ApotheoTech/Aper-Oculus/APT-KRIA-FMC.kicad_sch

## KiCad design APT-KRIA-FMC.kicad_sch (2023-12-22)

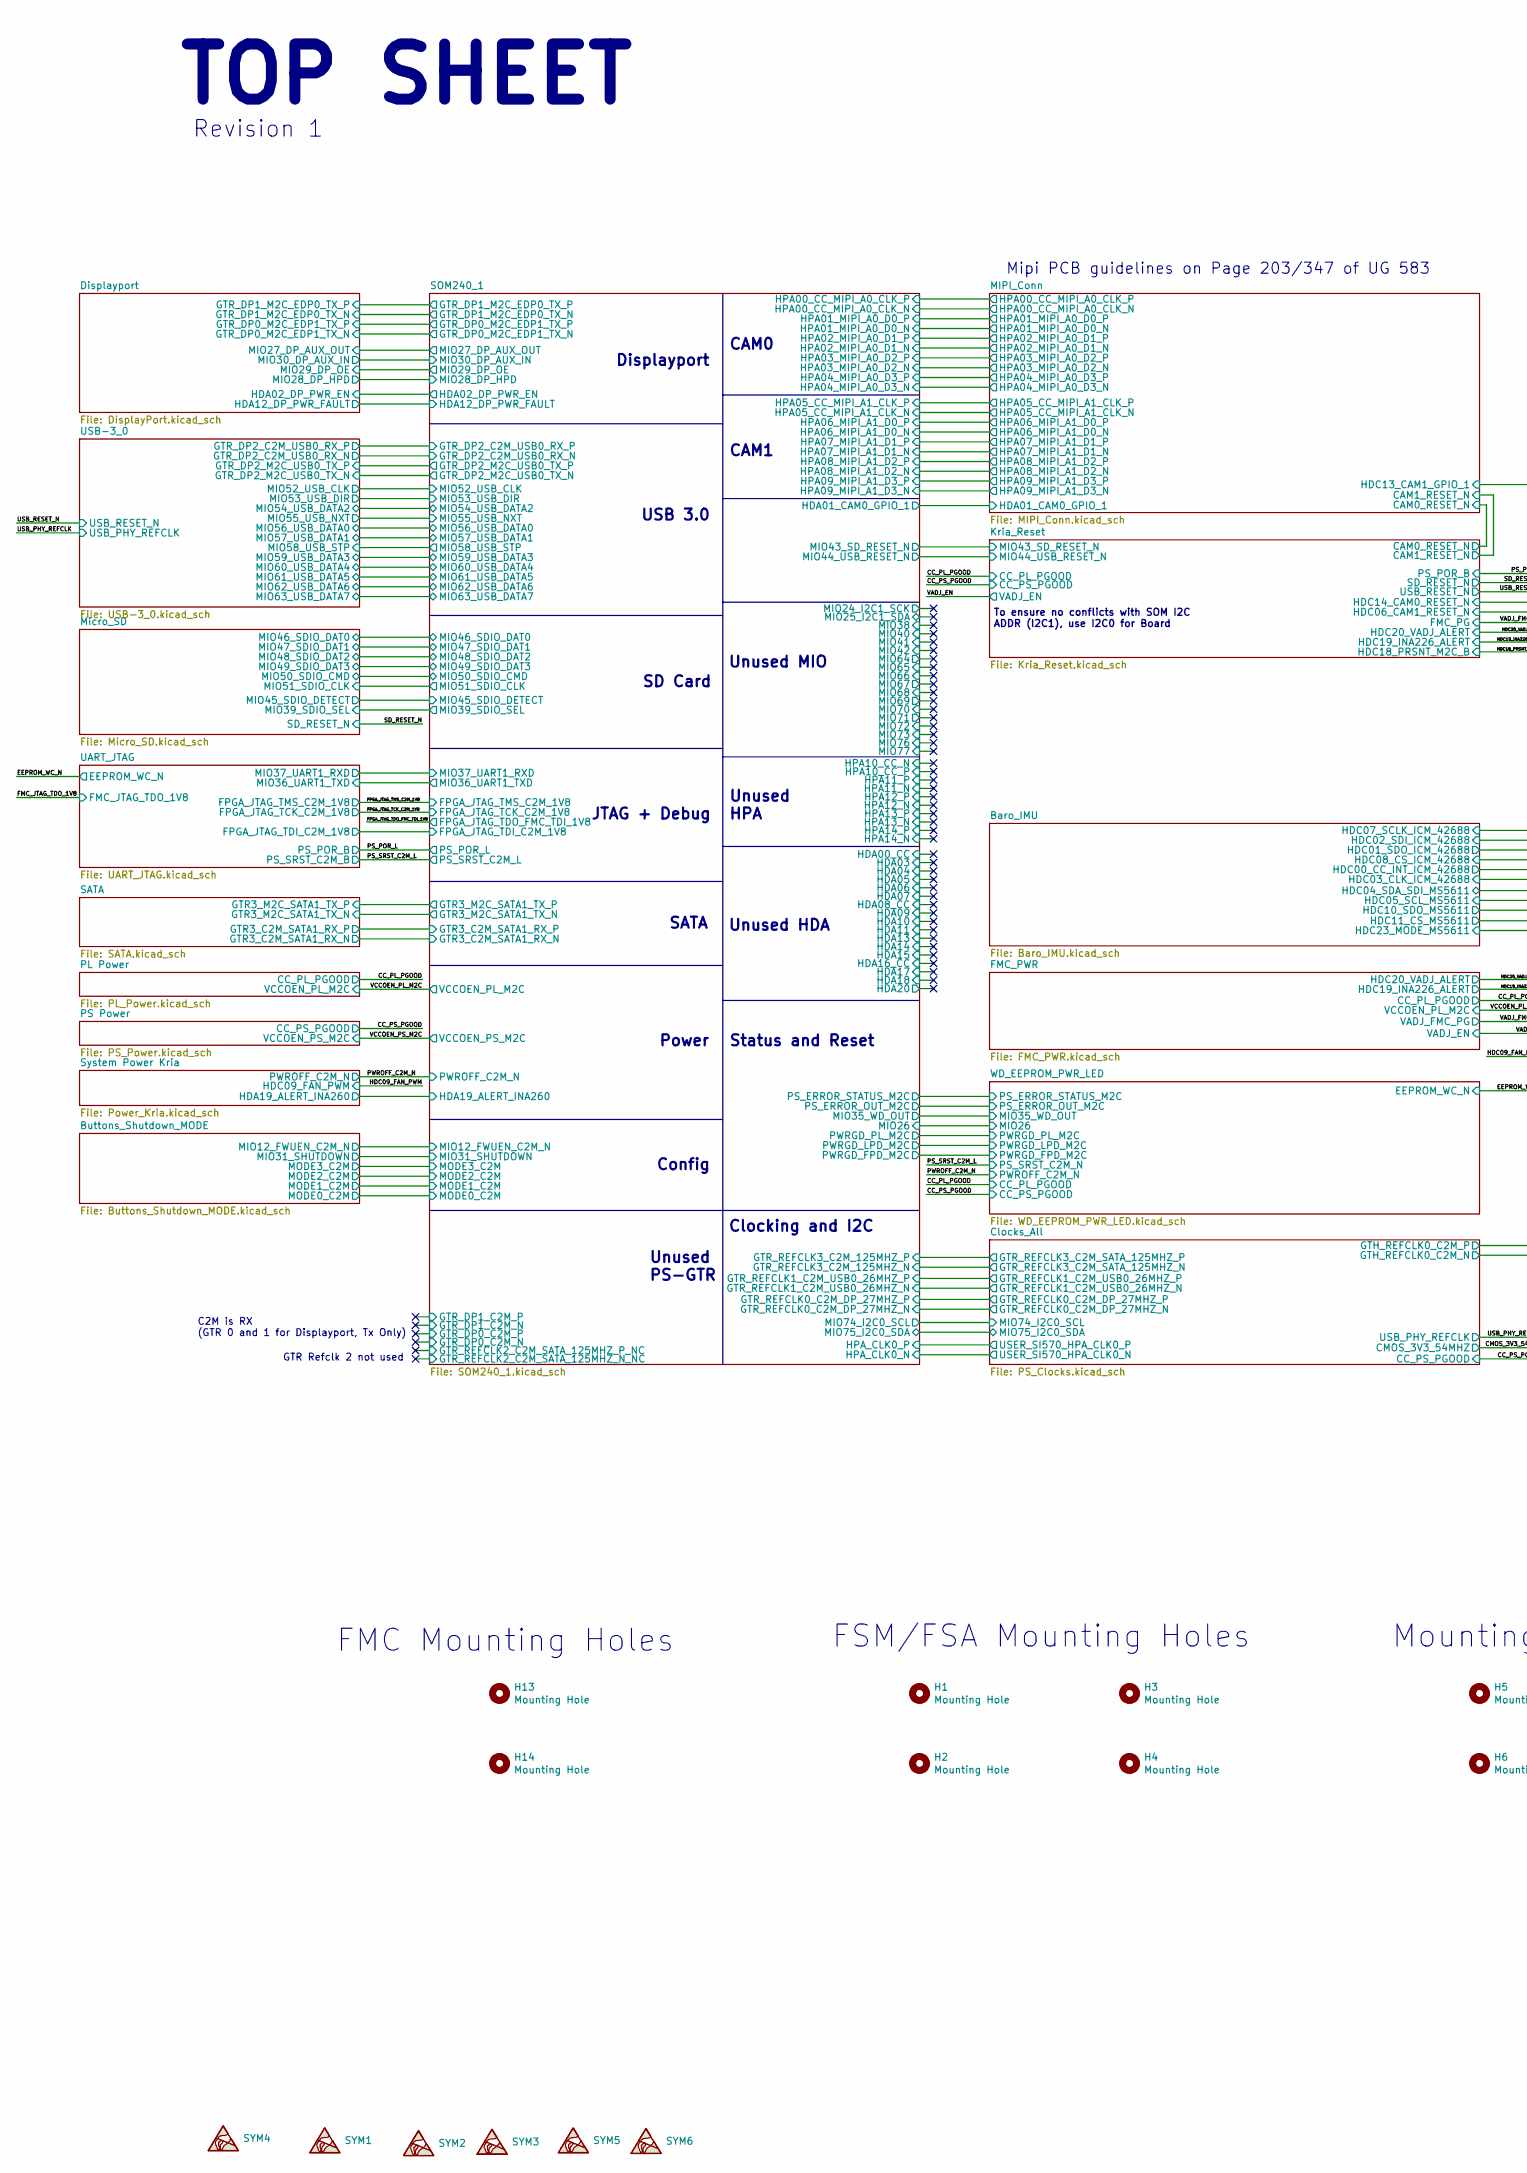
[picture p6: schematic APT-KRIA-FMC.kicad_sch, part in row 1, column 1]

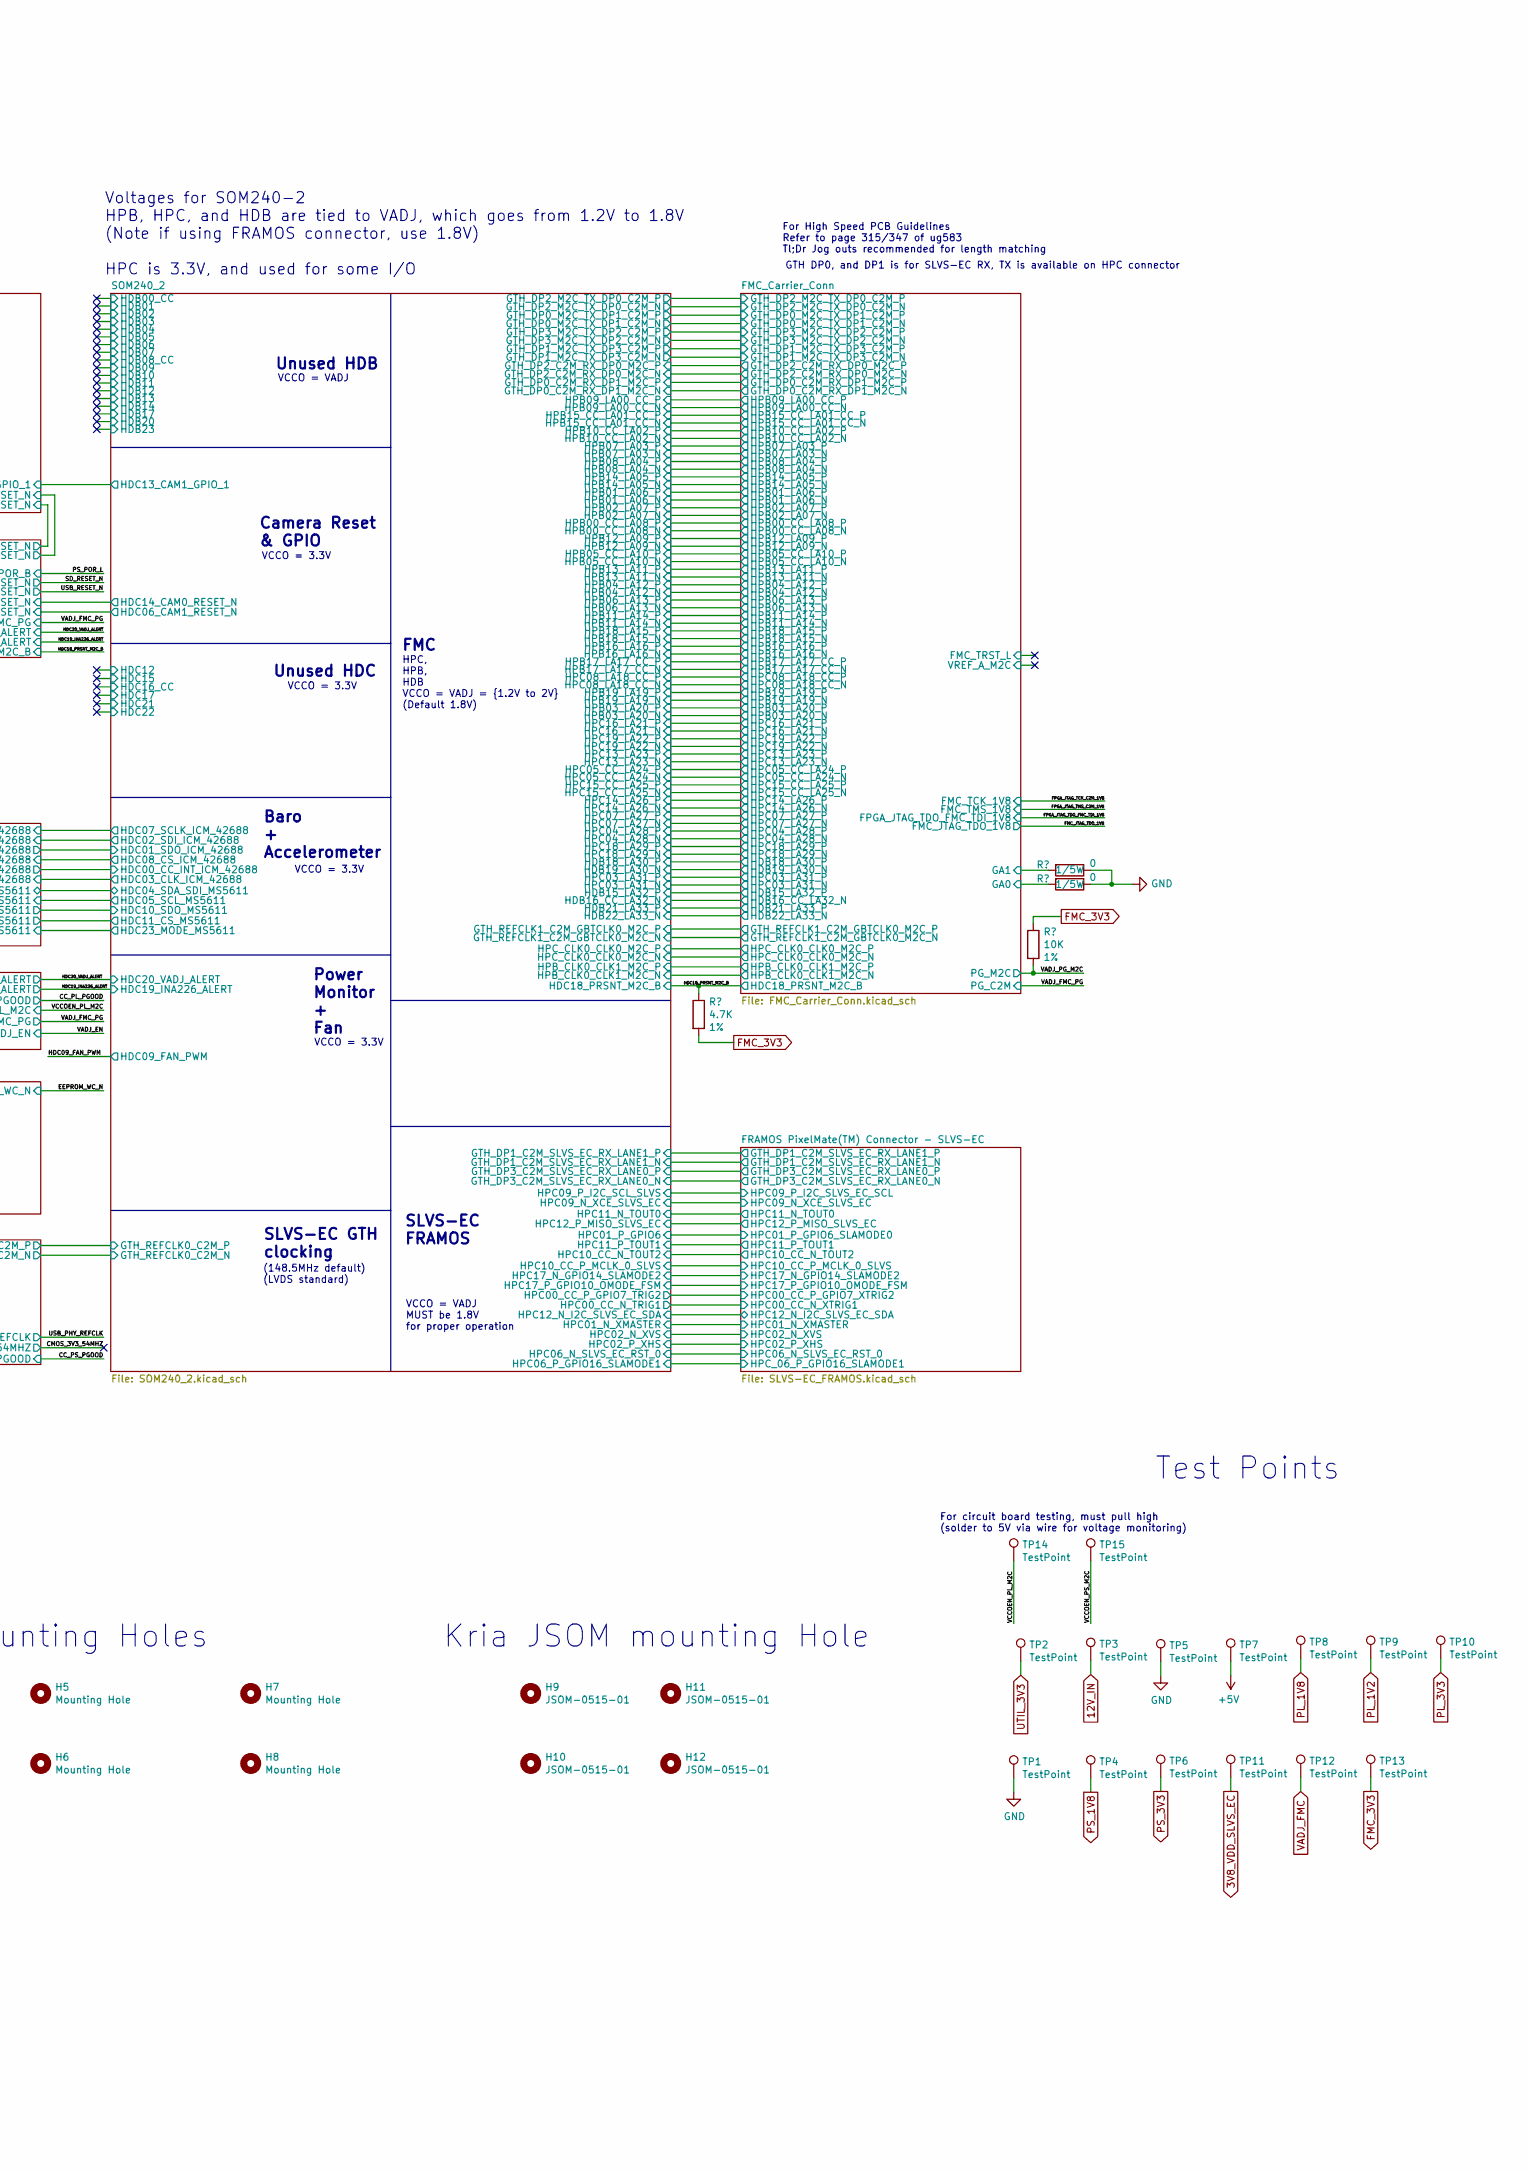
[picture p7: schematic APT-KRIA-FMC.kicad_sch, part in row 1, column 2]

Parts:
H1, H2, H3, H4: Mounting Hole; M1_6_FRAMOS
H5, H6, H7, H8: Mounting Hole; 3.4mm_Mounting_Hole
H9, H10, H11, H12: JSOM-0515-01
H13, H14: Mounting Hole; MountingHole_2.7mm_M2.5_Pad_2.9mm
R5, R6: 0; R_0402_1005Metric; PartNumber CRCW04020000Z0EDHP
R11: 4.7K; R_0402_1005Metric; Tolerance 1%; PartNumber CRCW04024K70FKED
R33: 10K; R_0402_1005Metric; Tolerance 1%; PartNumber ERJ-2RKF1002X
SYM1: SYM_ESD_Small; ApotheoTech_Sym
SYM2: SYM_ESD_Small; WEEE-Logo_4.2x6mm_SilkScreen
SYM3: SYM_ESD_Small; ESD-Logo_6.6x6mm_SilkScreen
SYM4: SYM_ESD_Small; ApotheoTech_Logo_Small
SYM5: SYM_ESD_Small; CE-Logo_8.5x6mm_SilkScreen
SYM6: SYM_ESD_Small; UKCA_Logo_8_5mm
TP1, TP2, TP3, TP4, TP5, TP6, TP7, TP8, TP9, TP10, TP11, TP12, TP13, TP14, TP15: TestPoint

Connections:
3V8_VDD_SLVS_EC: TP11.1
12V_IN: TP3.1
+5V: TP7.1
FMC_3V3: R11.2, R33.1, TP13.1
GA0: R6.2
GA1: R5.2
GND: R5.1, R6.1, TP1.1, TP5.1
HDC18_PRSNT_M2C_B: R11.1
PL_1V2: TP9.1
PL_1V8: TP8.1
PL_3V3: TP10.1
PS_1V8: TP4.1
PS_3V3: TP6.1
UTIL_3V3: TP2.1
VADJ_FMC: TP12.1
VADJ_PG_M2C: R33.2
VCCOEN_PL_M2C: TP14.1
VCCOEN_PS_M2C: TP15.1

Notes on the sheet:
VCCO = VADJ
SLVS-EC FRAMOS
VCCO = 3.3V
For High Speed PCB Guidelines Refer to page 315/347 of ug583 Tl;Dr Jog outs recommended for length matching
SD Card
Power
(148.5MHz default) (LVDS standard)
Unused HDA
Baro + Accelerometer
To ensure no conflicts with SOM I2C ADDR (I2C1), use I2C0 for Board
Mipi PCB guidelines on Page 203/347 of UG 583
Unused HDB
Clocking and I2C
FMC Mounting Holes
Config
USB 3.0
FMC
CAM0
Unused PS-GTR
Displayport
Kria JSOM mounting Hole
Test Points
VCCO = VADJ MUST be 1.8V for proper operation
SATA
Revision 1
Voltages for SOM240-2 HPB, HPC, and HDB are tied to VADJ, which goes from 1.2V to 1.8V (Note if using FRAMOS connector, use 1.8V) HPC is 3.3V, and used for some I/O
TOP SHEET
JTAG + Debug
FSM/FSA Mounting Holes
C2M is RX (GTR 0 and 1 for Displayport, Tx Only)
HPC, HPB, HDB VCCO = VADJ = {1.2V to 2V} (Default 1.8V)
GTR Refclk 2 not used
Unused HPA
Status and Reset
CAM1
For circuit board testing, must pull high (solder to 5V via wire for voltage monitoring)
SLVS-EC GTH clocking
Camera Reset & GPIO
Power Monitor + Fan
GTH DP0, and DP1 is for SLVS-EC RX, TX is available on HPC connector
Mounting Holes
Unused MIO
Unused HDC
