ApotheoTech/Aper-Oculus/Baro_IMU.kicad_sch

## KiCad design Baro_IMU.kicad_sch (2023-12-22)

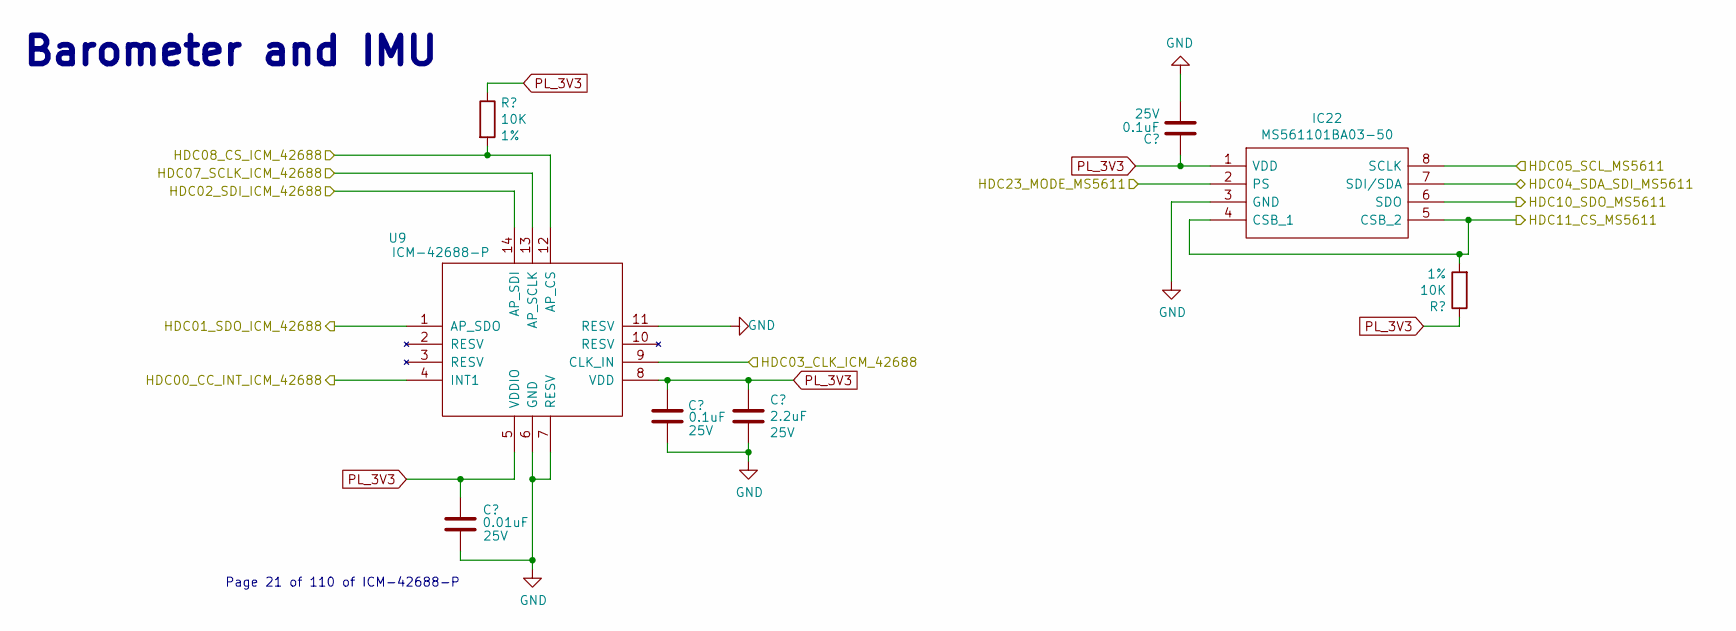
[picture p8: schematic Baro_IMU.kicad_sch]

Parts:
C179: 0.01uF; C_0402_1005Metric; Tolerance +-10%; Voltage 25V; PartNumber 04023D103KAT2A
C180, C264: 0.1uF; C_0402_1005Metric; Tolerance +-10%; Voltage 25V; PartNumber TMK105BJ104KVHF
C263: 2.2uF; C_0402_1005Metric; Tolerance +-10%; Voltage 25V; PartNumber GRM155R61E225KE1D
IC22: MS561101BA03-50; Mouser Part Number 824-MS561101BA03-50
R44, R51: 10K; R_0402_1005Metric; Tolerance 1%; PartNumber ERJ-2RKF1002X
U9: ICM-42688-P

Connections:
GND: C179.1, C180.1, C263.2, C264.1, IC22.3 (GND), U9.6 (GND), U9.7 (RESV), U9.11 (RESV)
HDC00_CC_INT_ICM_42688: U9.4 (INT1)
HDC01_SDO_ICM_42688: U9.1 (AP_SDO)
HDC02_SDI_ICM_42688: U9.14 (AP_SDI)
HDC03_CLK_ICM_42688: U9.9 (CLK_IN)
HDC04_SDA_SDI_MS5611: IC22.7 (SDI/SDA)
HDC05_SCL_MS5611: IC22.8 (SCLK)
HDC07_SCLK_ICM_42688: U9.13 (AP_SCLK)
HDC08_CS_ICM_42688: R44.2, U9.12 (AP_CS)
HDC10_SDO_MS5611: IC22.6 (SDO)
HDC11_CS_MS5611: IC22.4 (CSB_1), IC22.5 (CSB_2), R51.2
HDC23_MODE_MS5611: IC22.2 (PS)
PL_3V3: C179.2, C180.2, C263.1, C264.2, IC22.1 (VDD), R44.1, R51.1, U9.5 (VDDIO), U9.8 (VDD)

Notes on the sheet:
Barometer and IMU
Page 21 of 110 of ICM-42688-P
