ApotheoTech/Aper-Oculus/Buttons_Shutdown_MODE.kicad_sch

## KiCad design Buttons_Shutdown_MODE.kicad_sch (2023-12-22)

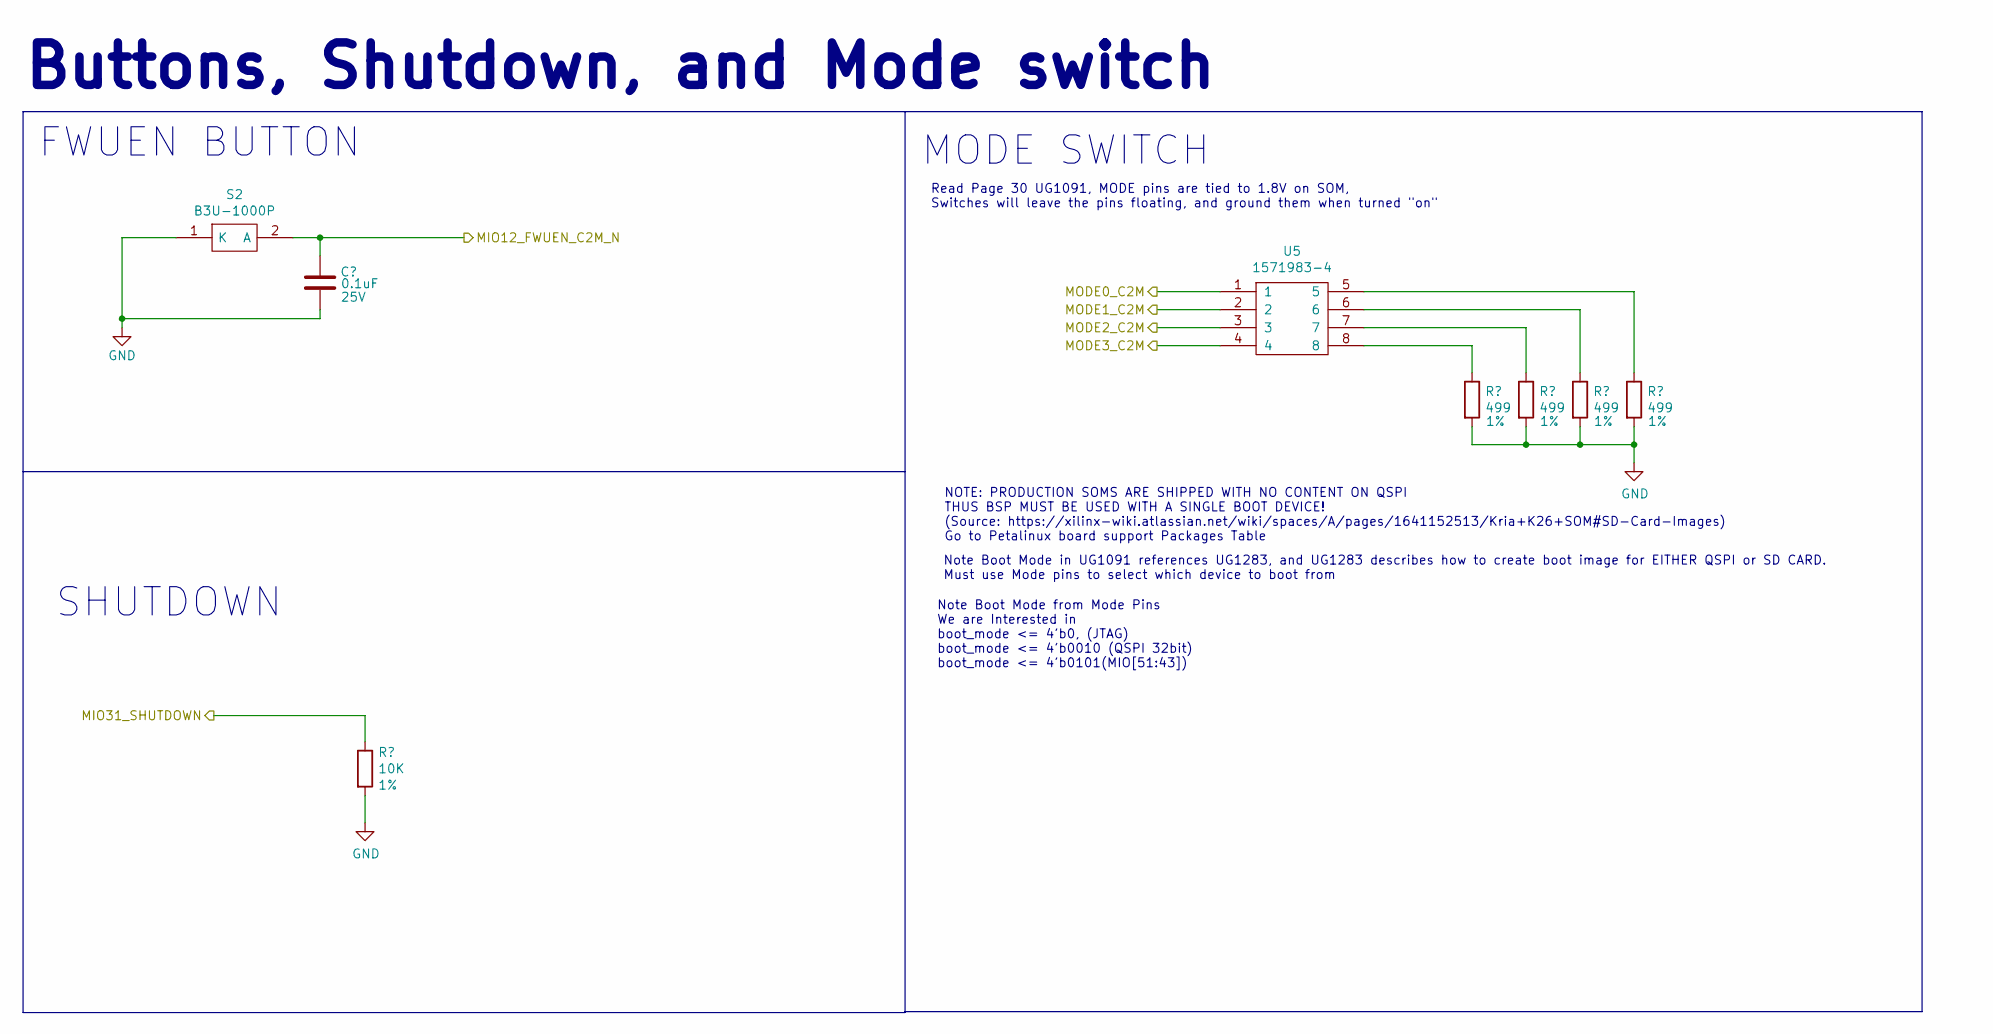
[picture p9: schematic Buttons_Shutdown_MODE.kicad_sch]

Parts:
C258: 0.1uF; C_0402_1005Metric; Tolerance +-10%; Voltage 25V; PartNumber TMK105BJ104KVHF
R218: 10K; R_0402_1005Metric; Tolerance 1%; PartNumber ERJ-2RKF1002X
R219, R220, R221, R222: 499; R_0402_1005Metric; PartNumber ERJ-2RKF4990X
S2: B3U-1000P; Mouser Part Number 653-B3U-1000P
U5: 1571983-4

Connections:
GND: C258.1, R218.2, R219.2, R220.2, R221.2, R222.2, S2.1 (K)
MIO12_FWUEN_C2M_N: C258.2, S2.2 (A)
MIO31_SHUTDOWN: R218.1
MODE0_C2M: U5.1
MODE1_C2M: U5.2
MODE2_C2M: U5.3
MODE3_C2M: U5.4
unnamed: R219.1, U5.8
unnamed: R220.1, U5.7
unnamed: R221.1, U5.6
unnamed: R222.1, U5.5

Notes on the sheet:
NOTE: PRODUCTION SOMS ARE SHIPPED WITH NO CONTENT ON QSPI THUS BSP MUST BE USED WITH A SINGLE BOOT DEVICE! (Source: https://xilinx-wiki.atlassian.net/wiki/spaces/A/pages/1641152513/Kria+K26+SOM#SD-Card-Images) Go to Petalinux board support Packages Table
SHUTDOWN
Read Page 30 UG1091, MODE pins are tied to 1.8V on SOM, Switches will leave the pins floating, and ground them when turned "on"
Buttons, Shutdown, and Mode switch
Note Boot Mode from Mode Pins We are Interested in boot_mode <= 4'b0, (JTAG) boot_mode <= 4'b0010 (QSPI 32bit) boot_mode <= 4'b0101(MIO[51:43])
MODE SWITCH
Note Boot Mode in UG1091 references UG1283, and UG1283 describes how to create boot image for EITHER QSPI or SD CARD. Must use Mode pins to select which device to boot from
FWUEN BUTTON
