ApotheoTech/Aper-Oculus/DisplayPort.kicad_sch

## KiCad design DisplayPort.kicad_sch (2023-12-22)

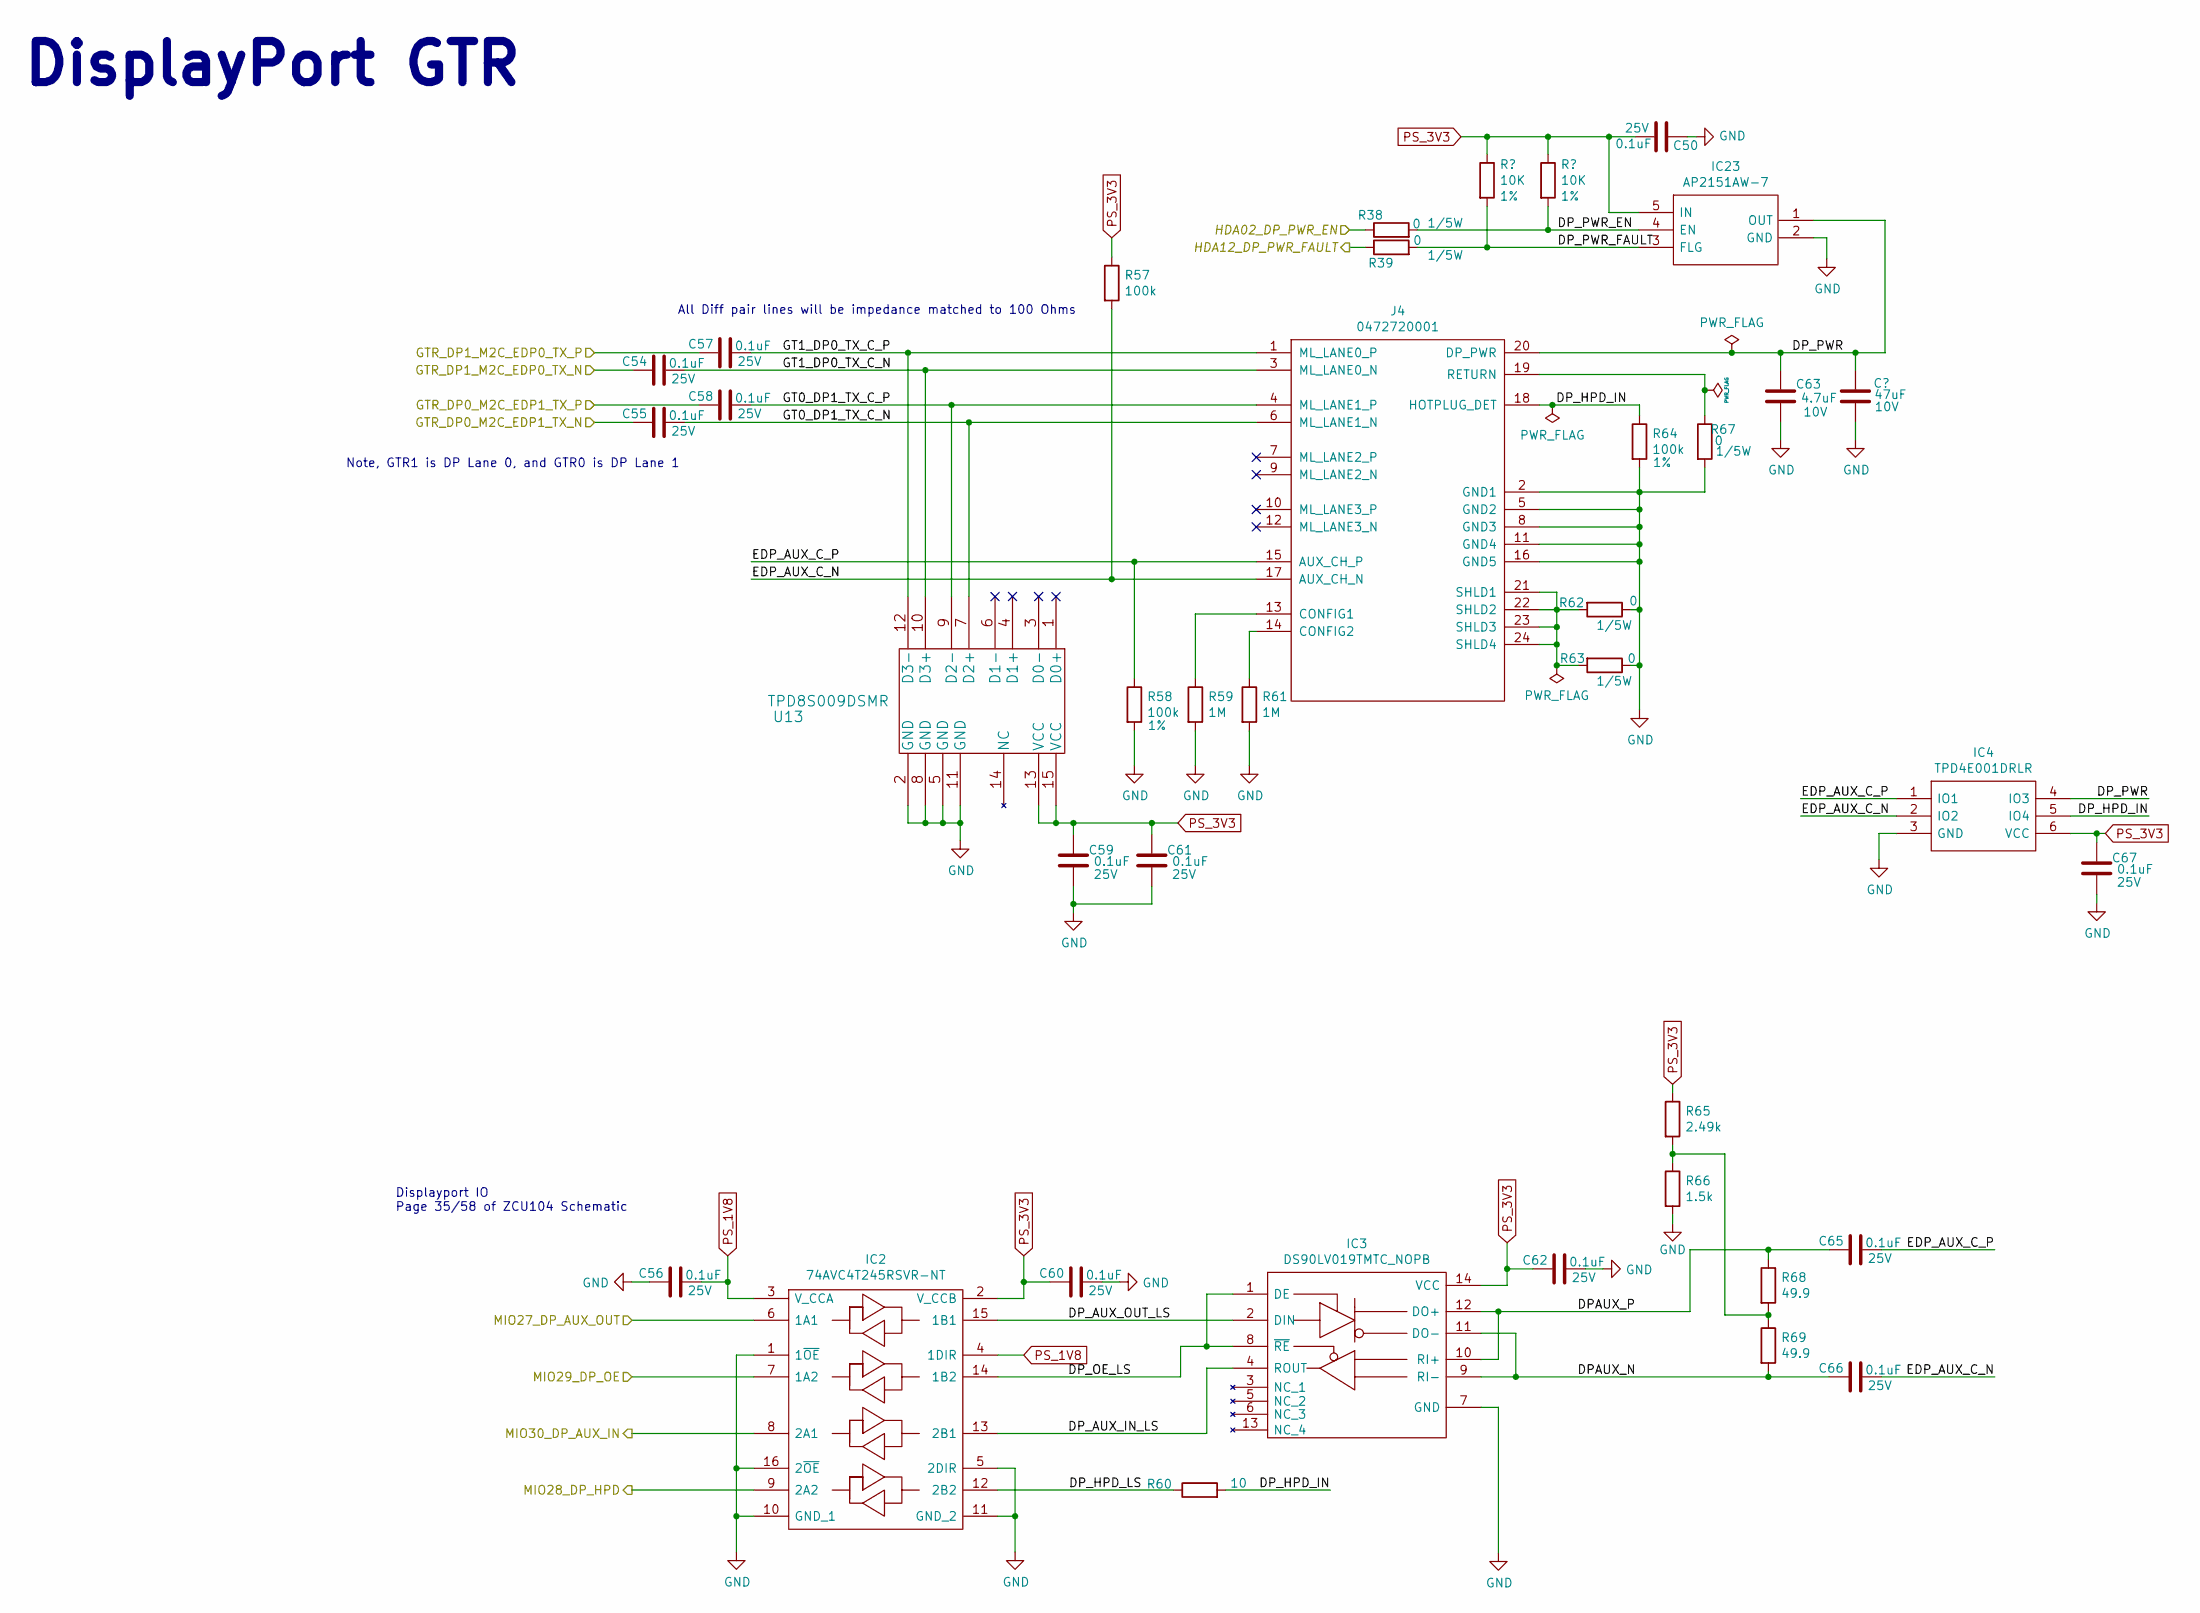
[picture p10: schematic DisplayPort.kicad_sch]

Parts:
C50, C54, C55, C56, C57, C58, C59, C60, C61, C62, C67: 0.1uF; C_0402_1005Metric; Tolerance +-10%; Voltage 25V; PartNumber TMK105BJ104KVHF
C51: 47uF; C_0805_2012Metric; Tolerance +-20%; Voltage 10V; PartNumber GRM21BR61A476ME15L
C63: 4.7uF; C_0402_1005Metric; Tolerance +-10%; Voltage 10V; PartNumber CL05A475KP5NRNC
C65, C66: 0.1uF; C_0402_1005Metric_smaller_footprint; Tolerance +-10%; Voltage 25V; PartNumber TMK105BJ104KVHF
IC2: 74AVC4T245RSVR-NT; Mouser Part Number 595-74AVC4T245RSVRNT
IC3: DS90LV019TMTC_NOPB; Mouser Part Number 926-S90LV019TMTCNOPB
IC4: TPD4E001DRLR; Mouser Part Number 595-TPD4E001DRLR
IC23: AP2151AW-7; Mouser Part Number 621-AP2151AW-7
J4: 0472720001‎
R38, R39, R62, R63, R67: 0; R_0402_1005Metric; PartNumber CRCW04020000Z0EDHP
R40, R41: 10K; R_0402_1005Metric; Tolerance 1%; PartNumber ERJ-2RKF1002X
R57, R58, R64: 100k; R_0402_1005Metric; PartNumber CRCW0402100KFKEDHP
R59, R61: 1M; R_0402_1005Metric; PartNumber CRCW04021M00FKED
R60: 10; R_0402_1005Metric; PartNumber ERJ-2RKF10R0X
R65: 2.49k; R_0402_1005Metric; PartNumber ERJ-2RKF2491X
R66: 1.5k; R_0402_1005Metric; PartNumber ERJ-H2RF1501X
R68, R69: 49.9; R_0402_1005Metric; PartNumber ERJ-2RKF49R9X
U13: TPD8S009DSMR

Connections:
DPAUX_N: C66.1, IC3.9 (RI-), IC3.11 (DO-), R69.2
DPAUX_P: C65.1, IC3.10 (RI+), IC3.12 (DO+), R68.1
DP_AUX_IN_LS: IC2.13 (2B1), IC3.4 (ROUT)
DP_AUX_OUT_LS: IC2.15 (1B1), IC3.2 (DIN)
DP_HPD_IN: IC4.5 (IO4), J4.18 (HOTPLUG_DET), R60.2, R64.1
DP_HPD_LS: IC2.12 (2B2), R60.1
DP_OE_LS: IC2.14 (1B2), IC3.1 (DE), IC3.8 (~RE)
DP_PWR: C51.2, C63.1, IC4.4 (IO3), IC23.1 (OUT), J4.20 (DP_PWR)
DP_PWR_EN: IC23.4 (EN), R38.2, R41.2
DP_PWR_FAULT: IC23.3 (FLG), R39.2, R40.2
EDP_AUX_C_N: C66.2, IC4.2 (IO2), J4.17 (AUX_CH_N), R57.2
EDP_AUX_C_P: C65.2, IC4.1 (IO1), J4.15 (AUX_CH_P), R58.1
GND: C50.1, C51.1, C56.1, C59.1, C60.2, C61.1, C62.2, C63.2, C67.1, IC2.1 (1~OE), IC2.5 (2DIR), IC2.10 (GND_1), IC2.11 (GND_2), IC2.16 (2~OE), IC3.7 (GND), IC4.3 (GND), IC23.2 (GND), J4.2 (GND1), J4.5 (GND2), J4.8 (GND3), J4.11 (GND4), J4.16 (GND5), R58.2, R59.2, R61.2, R62.1, R63.1, R64.2, R66.2, R67.2, U13.2 (GND), U13.5 (GND), U13.8 (GND), U13.11 (GND)
GT0_DP1_TX_C_N: C55.2, J4.6 (ML_LANE1_N), U13.7 (D2+)
GT0_DP1_TX_C_P: C58.2, J4.4 (ML_LANE1_P), U13.9 (D2-)
GT1_DP0_TX_C_N: C54.2, J4.3 (ML_LANE0_N), U13.10 (D3+)
GT1_DP0_TX_C_P: C57.2, J4.1 (ML_LANE0_P), U13.12 (D3-)
GTR_DP0_M2C_EDP1_TX_N: C55.1
GTR_DP0_M2C_EDP1_TX_P: C58.1
GTR_DP1_M2C_EDP0_TX_N: C54.1
GTR_DP1_M2C_EDP0_TX_P: C57.1
HDA02_DP_PWR_EN: R38.1
HDA12_DP_PWR_FAULT: R39.1
MIO27_DP_AUX_OUT: IC2.6 (1A1)
MIO28_DP_HPD: IC2.9 (2A2)
MIO29_DP_OE: IC2.7 (1A2)
MIO30_DP_AUX_IN: IC2.8 (2A1)
unnamed: J4.13 (CONFIG1), R59.1
unnamed: J4.14 (CONFIG2), R61.1
unnamed: J4.19 (RETURN), R67.1
unnamed: J4.21 (SHLD1), J4.22 (SHLD2), J4.23 (SHLD3), J4.24 (SHLD4), R62.2, R63.2
unnamed: R65.2, R66.1, R68.2, R69.1
PS_1V8: C56.2, IC2.3 (V_CCA), IC2.4 (1DIR)
PS_3V3: C50.2, C59.2, C60.1, C61.2, C62.1, C67.2, IC2.2 (V_CCB), IC3.14 (VCC), IC4.6 (VCC), IC23.5 (IN), R40.1, R41.1, R57.1, R65.1, U13.13 (VCC), U13.15 (VCC)

Notes on the sheet:
DisplayPort GTR
Displayport IO Page 35/58 of ZCU104 Schematic
All Diff pair lines will be impedance matched to 100 Ohms
Note, GTR1 is DP Lane 0, and GTR0 is DP Lane 1
