ApotheoTech/Aper-Oculus/FMC_Carrier_Conn.kicad_sch

## KiCad design FMC_Carrier_Conn.kicad_sch (2023-12-22)

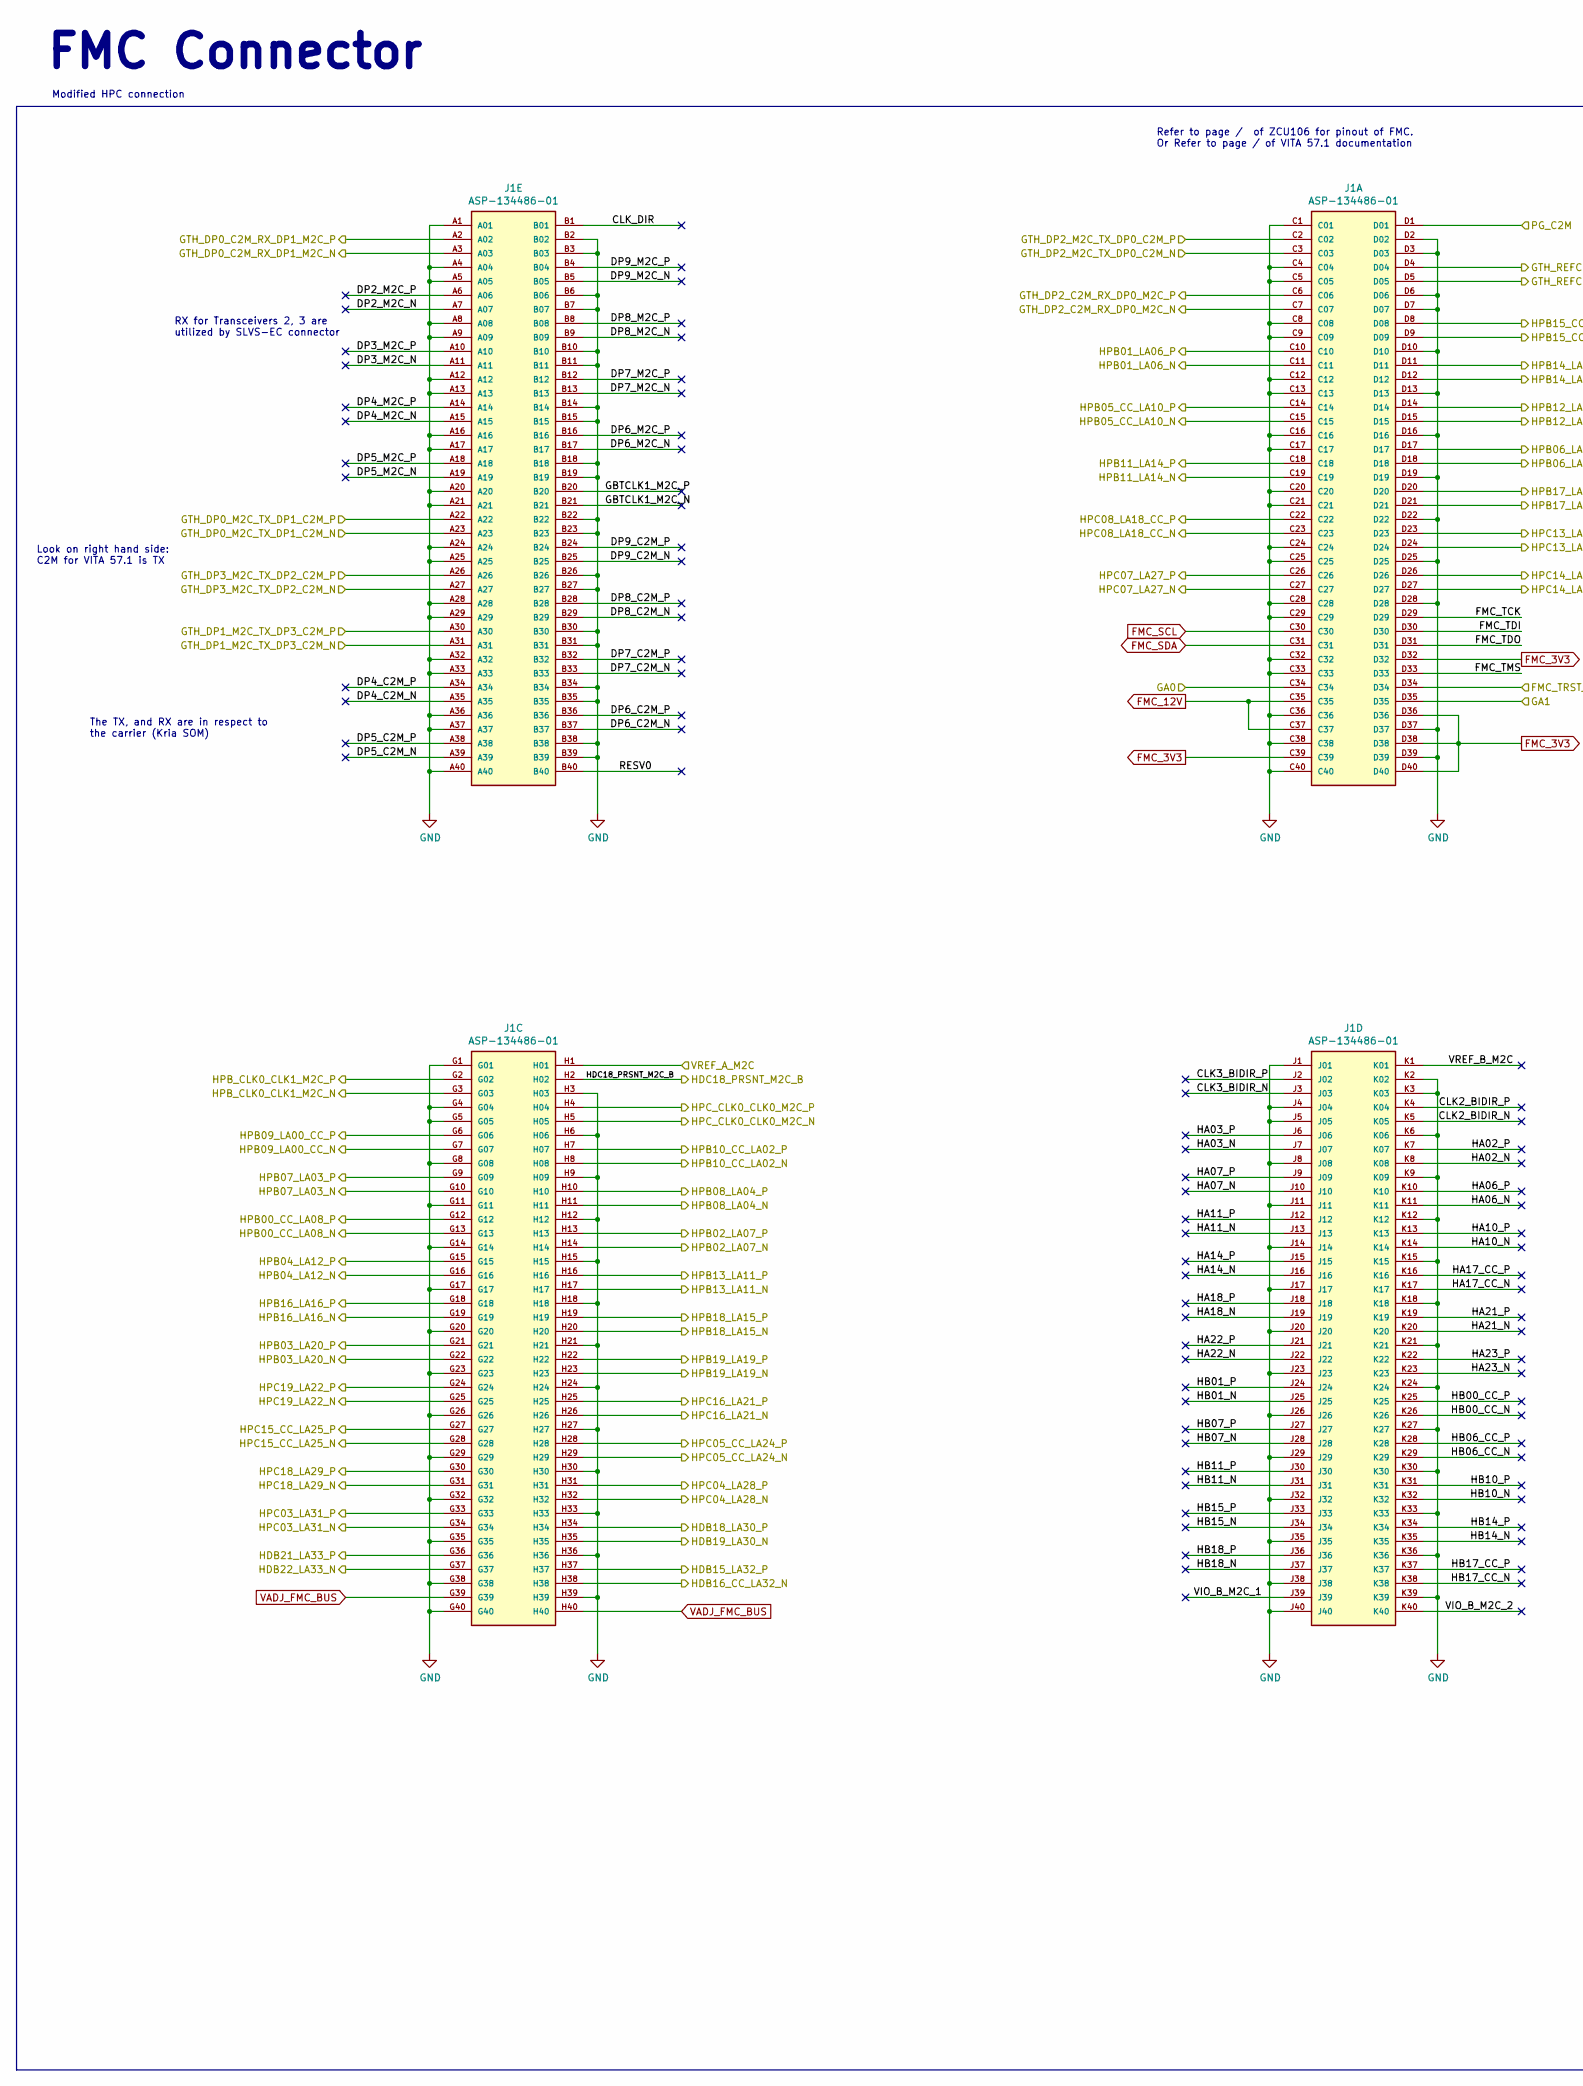
[picture p11: schematic FMC_Carrier_Conn.kicad_sch, part in row 1, column 1]

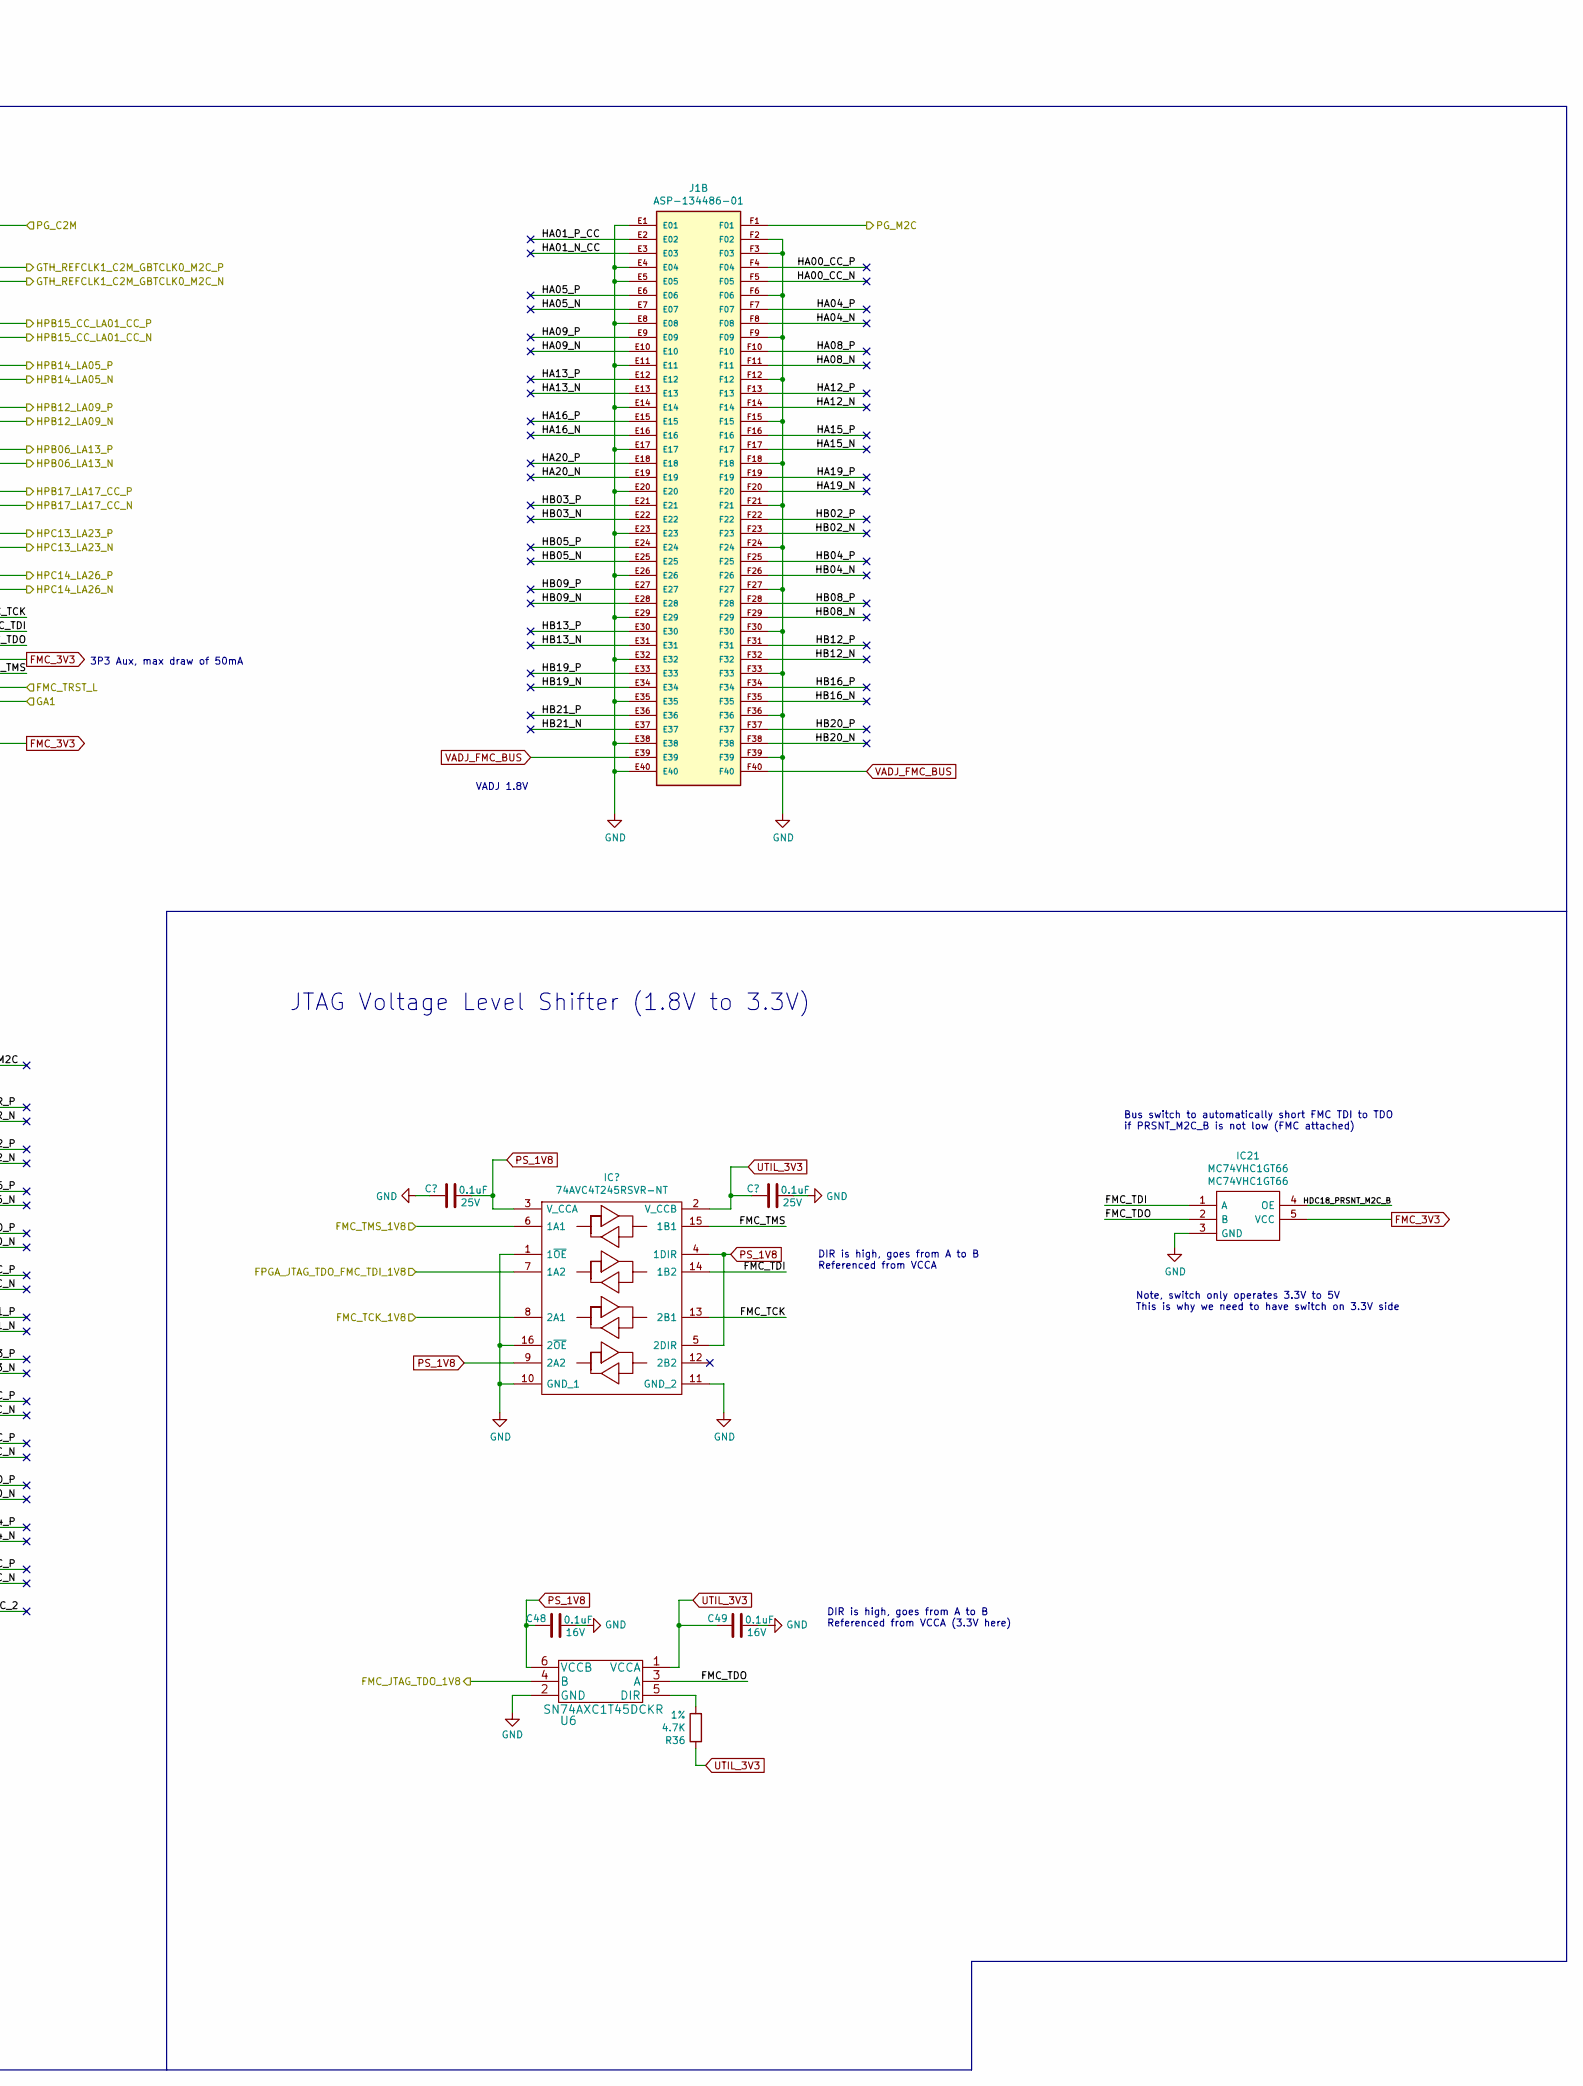
[picture p12: schematic FMC_Carrier_Conn.kicad_sch, part in row 1, column 2]

Parts:
C46, C47: 0.1uF; C_0402_1005Metric; Tolerance +-10%; Voltage 25V; PartNumber TMK105BJ104KVHF
C48, C49: 0.1uF; C_0402_1005Metric; Tolerance +-10%; Voltage 16V; PartNumber EMK105B7104KV-F
IC17: 74AVC4T245RSVR-NT; Mouser Part Number 595-74AVC4T245RSVRNT
IC21: MC74VHC1GT66; M74VHC1GT66; PartNumber MC74VHC1GT66
J1: ASP-134486-01; PARTREV P
R36: 4.7K; R_0402_1005Metric; Tolerance 1%; PartNumber CRCW04024K70FKED
U6: SN74AXC1T45DCKR

Connections:
CLK2_BIDIR_N: J1.K5 (K05)
CLK2_BIDIR_P: J1.K4 (K04)
CLK3_BIDIR_N: J1.J3 (J03)
CLK3_BIDIR_P: J1.J2 (J02)
CLK_DIR: J1.B1 (B01)
DP2_M2C_N: J1.A7 (A07)
DP2_M2C_P: J1.A6 (A06)
DP3_M2C_N: J1.A11
DP3_M2C_P: J1.A10
DP4_C2M_N: J1.A35
DP4_C2M_P: J1.A34
DP4_M2C_N: J1.A15
DP4_M2C_P: J1.A14
DP5_C2M_N: J1.A39
DP5_C2M_P: J1.A38
DP5_M2C_N: J1.A19
DP5_M2C_P: J1.A18
DP6_C2M_N: J1.B37
DP6_C2M_P: J1.B36
DP6_M2C_N: J1.B17
DP6_M2C_P: J1.B16
DP7_C2M_N: J1.B33
DP7_C2M_P: J1.B32
DP7_M2C_N: J1.B13
DP7_M2C_P: J1.B12
DP8_C2M_N: J1.B29
DP8_C2M_P: J1.B28
DP8_M2C_N: J1.B9 (B09)
DP8_M2C_P: J1.B8 (B08)
DP9_C2M_N: J1.B25
DP9_C2M_P: J1.B24
DP9_M2C_N: J1.B5 (B05)
DP9_M2C_P: J1.B4 (B04)
FMC_3V3: IC21.5 (VCC), J1.C39, J1.D32, J1.D36, J1.D38, J1.D40
FMC_12V: J1.C35, J1.C37
FMC_JTAG_TDO_1V8: U6.4 (B)
FMC_SCL: J1.C30
FMC_SDA: J1.C31
FMC_TCK: IC17.13 (2B1), J1.D29
FMC_TCK_1V8: IC17.8 (2A1)
FMC_TDI: IC17.14 (1B2), IC21.1 (A), J1.D30
FMC_TDO: IC21.2 (B), J1.D31, U6.3 (A)
FMC_TMS: IC17.15 (1B1), J1.D33
FMC_TMS_1V8: IC17.6 (1A1)
FMC_TRST_L: J1.D34
FPGA_JTAG_TDO_FMC_TDI_1V8: IC17.7 (1A2)
GA0: J1.C34
GA1: J1.D35
GBTCLK1_M2C_N: J1.B21
GBTCLK1_M2C_P: J1.B20
GND: C46.1, C47.2, C48.2, C49.2, IC17.1 (1~OE), IC17.10 (GND_1), IC17.11 (GND_2), IC17.16 (2~OE), IC21.3 (GND), J1.A1 (A01), J1.A4 (A04), J1.A5 (A05), J1.A8 (A08), J1.A9 (A09), J1.A12, J1.A13, J1.A16, J1.A17, J1.A20, J1.A21, J1.A24, J1.A25, J1.A28, J1.A29, J1.A32, J1.A33, J1.A36, J1.A37, J1.A40, J1.B2 (B02), J1.B3 (B03), J1.B6 (B06), J1.B7 (B07), J1.B10, J1.B11, J1.B14, J1.B15, J1.B18, J1.B19, J1.B22, J1.B23, J1.B26, J1.B27, J1.B30, J1.B31, J1.B34, J1.B35, J1.B38, J1.B39, J1.C1 (C01), J1.C4 (C04), J1.C5 (C05), J1.C8 (C08), J1.C9 (C09), J1.C12, J1.C13, J1.C16, J1.C17, J1.C20, J1.C21, J1.C24, J1.C25, J1.C28, J1.C29, J1.C32, J1.C33, J1.C36, J1.C38, J1.C40, J1.D2 (D02), J1.D3 (D03), J1.D6 (D06), J1.D7 (D07), J1.D10, J1.D13, J1.D16, J1.D19, J1.D22, J1.D25, J1.D28, J1.D37, J1.D39, J1.E1 (E01), J1.E4 (E04), J1.E5 (E05), J1.E8 (E08), J1.E11, J1.E14, J1.E17, J1.E20, J1.E23, J1.E26, J1.E29, J1.E32, J1.E35, J1.E38, J1.E40, J1.F2 (F02), J1.F3 (F03), J1.F6 (F06), J1.F9 (F09), J1.F12, J1.F15, J1.F18, J1.F21, J1.F24, J1.F27, J1.F30, J1.F33, J1.F36, J1.F39, J1.G1 (G01), J1.G4 (G04), J1.G5 (G05), J1.G8 (G08), J1.G11, J1.G14, J1.G17, J1.G20, J1.G23, J1.G26, J1.G29, J1.G32, J1.G35, J1.G38, J1.G40, J1.H3 (H03), J1.H6 (H06), J1.H9 (H09), J1.H12, J1.H15, J1.H18, J1.H21, J1.H24, J1.H27, J1.H30, J1.H33, J1.H36, J1.H39, J1.J1 (J01), J1.J4 (J04), J1.J5 (J05), J1.J8 (J08), J1.J11, J1.J14, J1.J17, J1.J20, J1.J23, J1.J26, J1.J29, J1.J32, J1.J35, J1.J38, J1.J40, J1.K2 (K02), J1.K3 (K03), J1.K6 (K06), J1.K9 (K09), J1.K12, J1.K15, J1.K18, J1.K21, J1.K24, J1.K27, J1.K30, J1.K33, J1.K36, J1.K39, U6.2 (GND)
GTH_DP0_C2M_RX_DP1_M2C_N: J1.A3 (A03)
GTH_DP0_C2M_RX_DP1_M2C_P: J1.A2 (A02)
GTH_DP0_M2C_TX_DP1_C2M_N: J1.A23
GTH_DP0_M2C_TX_DP1_C2M_P: J1.A22
GTH_DP1_M2C_TX_DP3_C2M_N: J1.A31
GTH_DP1_M2C_TX_DP3_C2M_P: J1.A30
GTH_DP2_C2M_RX_DP0_M2C_N: J1.C7 (C07)
GTH_DP2_C2M_RX_DP0_M2C_P: J1.C6 (C06)
GTH_DP2_M2C_TX_DP0_C2M_N: J1.C3 (C03)
GTH_DP2_M2C_TX_DP0_C2M_P: J1.C2 (C02)
GTH_DP3_M2C_TX_DP2_C2M_N: J1.A27
GTH_DP3_M2C_TX_DP2_C2M_P: J1.A26
GTH_REFCLK1_C2M_GBTCLK0_M2C_N: J1.D5 (D05)
GTH_REFCLK1_C2M_GBTCLK0_M2C_P: J1.D4 (D04)
HA00_CC_N: J1.F5 (F05)
HA00_CC_P: J1.F4 (F04)
HA01_N_CC: J1.E3 (E03)
HA01_P_CC: J1.E2 (E02)
HA02_N: J1.K8 (K08)
HA02_P: J1.K7 (K07)
HA03_N: J1.J7 (J07)
HA03_P: J1.J6 (J06)
HA04_N: J1.F8 (F08)
HA04_P: J1.F7 (F07)
HA05_N: J1.E7 (E07)
HA05_P: J1.E6 (E06)
HA06_N: J1.K11
HA06_P: J1.K10
HA07_N: J1.J10
HA07_P: J1.J9 (J09)
HA08_N: J1.F11
HA08_P: J1.F10
HA09_N: J1.E10
HA09_P: J1.E9 (E09)
HA10_N: J1.K14
HA10_P: J1.K13
HA11_N: J1.J13
HA11_P: J1.J12
HA12_N: J1.F14
HA12_P: J1.F13
HA13_N: J1.E13
HA13_P: J1.E12
HA14_N: J1.J16
HA14_P: J1.J15
HA15_N: J1.F17
HA15_P: J1.F16
HA16_N: J1.E16
HA16_P: J1.E15
HA17_CC_N: J1.K17
HA17_CC_P: J1.K16
HA18_N: J1.J19
HA18_P: J1.J18
HA19_N: J1.F20
HA19_P: J1.F19
HA20_N: J1.E19
HA20_P: J1.E18
HA21_N: J1.K20
HA21_P: J1.K19
HA22_N: J1.J22
HA22_P: J1.J21
HA23_N: J1.K23
HA23_P: J1.K22
HB00_CC_N: J1.K26
HB00_CC_P: J1.K25
HB01_N: J1.J25
HB01_P: J1.J24
HB02_N: J1.F23
HB02_P: J1.F22
HB03_N: J1.E22
HB03_P: J1.E21
HB04_N: J1.F26
HB04_P: J1.F25
HB05_N: J1.E25
HB05_P: J1.E24
HB06_CC_N: J1.K29
HB06_CC_P: J1.K28
HB07_N: J1.J28
HB07_P: J1.J27
HB08_N: J1.F29
HB08_P: J1.F28
HB09_N: J1.E28
HB09_P: J1.E27
HB10_N: J1.K32
HB10_P: J1.K31
HB11_N: J1.J31
HB11_P: J1.J30
HB12_N: J1.F32
HB12_P: J1.F31
HB13_N: J1.E31
HB13_P: J1.E30
HB14_N: J1.K35
HB14_P: J1.K34
HB15_N: J1.J34
HB15_P: J1.J33
HB16_N: J1.F35
HB16_P: J1.F34
HB17_CC_N: J1.K38
HB17_CC_P: J1.K37
HB18_N: J1.J37
HB18_P: J1.J36
HB19_N: J1.E34
HB19_P: J1.E33
HB20_N: J1.F38
HB20_P: J1.F37
HB21_N: J1.E37
HB21_P: J1.E36
HDB15_LA32_P: J1.H37
HDB16_CC_LA32_N: J1.H38
HDB18_LA30_P: J1.H34
HDB19_LA30_N: J1.H35
HDB21_LA33_P: J1.G36
HDB22_LA33_N: J1.G37
HDC18_PRSNT_M2C_B: IC21.4 (OE), J1.H2 (H02)
HPB00_CC_LA08_N: J1.G13
HPB00_CC_LA08_P: J1.G12
HPB01_LA06_N: J1.C11
HPB01_LA06_P: J1.C10
HPB02_LA07_N: J1.H14
HPB02_LA07_P: J1.H13
HPB03_LA20_N: J1.G22
HPB03_LA20_P: J1.G21
HPB04_LA12_N: J1.G16
HPB04_LA12_P: J1.G15
HPB05_CC_LA10_N: J1.C15
HPB05_CC_LA10_P: J1.C14
HPB06_LA13_N: J1.D18
HPB06_LA13_P: J1.D17
HPB07_LA03_N: J1.G10
HPB07_LA03_P: J1.G9 (G09)
HPB08_LA04_N: J1.H11
HPB08_LA04_P: J1.H10
HPB09_LA00_CC_N: J1.G7 (G07)
HPB09_LA00_CC_P: J1.G6 (G06)
HPB10_CC_LA02_N: J1.H8 (H08)
HPB10_CC_LA02_P: J1.H7 (H07)
HPB11_LA14_N: J1.C19
HPB11_LA14_P: J1.C18
HPB12_LA09_N: J1.D15
HPB12_LA09_P: J1.D14
HPB13_LA11_N: J1.H17
HPB13_LA11_P: J1.H16
HPB14_LA05_N: J1.D12
HPB14_LA05_P: J1.D11
HPB15_CC_LA01_CC_N: J1.D9 (D09)
HPB15_CC_LA01_CC_P: J1.D8 (D08)
HPB16_LA16_N: J1.G19
HPB16_LA16_P: J1.G18
HPB17_LA17_CC_N: J1.D21
HPB17_LA17_CC_P: J1.D20
HPB18_LA15_N: J1.H20
HPB18_LA15_P: J1.H19
HPB19_LA19_N: J1.H23
HPB19_LA19_P: J1.H22
HPB_CLK0_CLK1_M2C_N: J1.G3 (G03)
HPB_CLK0_CLK1_M2C_P: J1.G2 (G02)
HPC03_LA31_N: J1.G34
HPC03_LA31_P: J1.G33
HPC04_LA28_N: J1.H32
HPC04_LA28_P: J1.H31
HPC05_CC_LA24_N: J1.H29
HPC05_CC_LA24_P: J1.H28
HPC07_LA27_N: J1.C27
HPC07_LA27_P: J1.C26
HPC08_LA18_CC_N: J1.C23
HPC08_LA18_CC_P: J1.C22
HPC13_LA23_N: J1.D24
HPC13_LA23_P: J1.D23
HPC14_LA26_N: J1.D27
HPC14_LA26_P: J1.D26
HPC15_CC_LA25_N: J1.G28
HPC15_CC_LA25_P: J1.G27
HPC16_LA21_N: J1.H26
HPC16_LA21_P: J1.H25
HPC18_LA29_N: J1.G31
HPC18_LA29_P: J1.G30
HPC19_LA22_N: J1.G25
HPC19_LA22_P: J1.G24
HPC_CLK0_CLK0_M2C_N: J1.H5 (H05)
HPC_CLK0_CLK0_M2C_P: J1.H4 (H04)
unnamed: R36.2, U6.5 (DIR)
PG_C2M: J1.D1 (D01)
PG_M2C: J1.F1 (F01)
PS_1V8: C46.2, C48.1, IC17.3 (V_CCA), IC17.4 (1DIR), IC17.5 (2DIR), IC17.9 (2A2), U6.6 (VCCB)
RESV0: J1.B40
UTIL_3V3: C47.1, C49.1, IC17.2 (V_CCB), R36.1, U6.1 (VCCA)
VADJ_FMC_BUS: J1.E39, J1.F40, J1.G39, J1.H40
VIO_B_M2C_1: J1.J39
VIO_B_M2C_2: J1.K40
VREF_A_M2C: J1.H1 (H01)
VREF_B_M2C: J1.K1 (K01)

Notes on the sheet:
The TX, and RX are in respect to the carrier (Kria SOM)
DIR is high, goes from A to B Referenced from VCCA (3.3V here)
JTAG Voltage Level Shifter (1.8V to 3.3V)
Note, switch only operates 3.3V to 5V This is why we need to have switch on 3.3V side
Look on right hand side: C2M for VITA 57.1 is TX
DIR is high, goes from A to B Referenced from VCCA
FMC Connector
Modified HPC connection
Bus switch to automatically short FMC TDI to TDO if PRSNT_M2C_B is not low (FMC attached)
3P3 Aux, max draw of 50mA
Refer to page / of ZCU106 for pinout of FMC. Or Refer to page / of VITA 57.1 documentation
VADJ 1.8V
RX for Transceivers 2, 3 are utilized by SLVS-EC connector
