ApotheoTech/Aper-Oculus/FMC_PWR.kicad_sch

## KiCad design FMC_PWR.kicad_sch (2023-12-22)

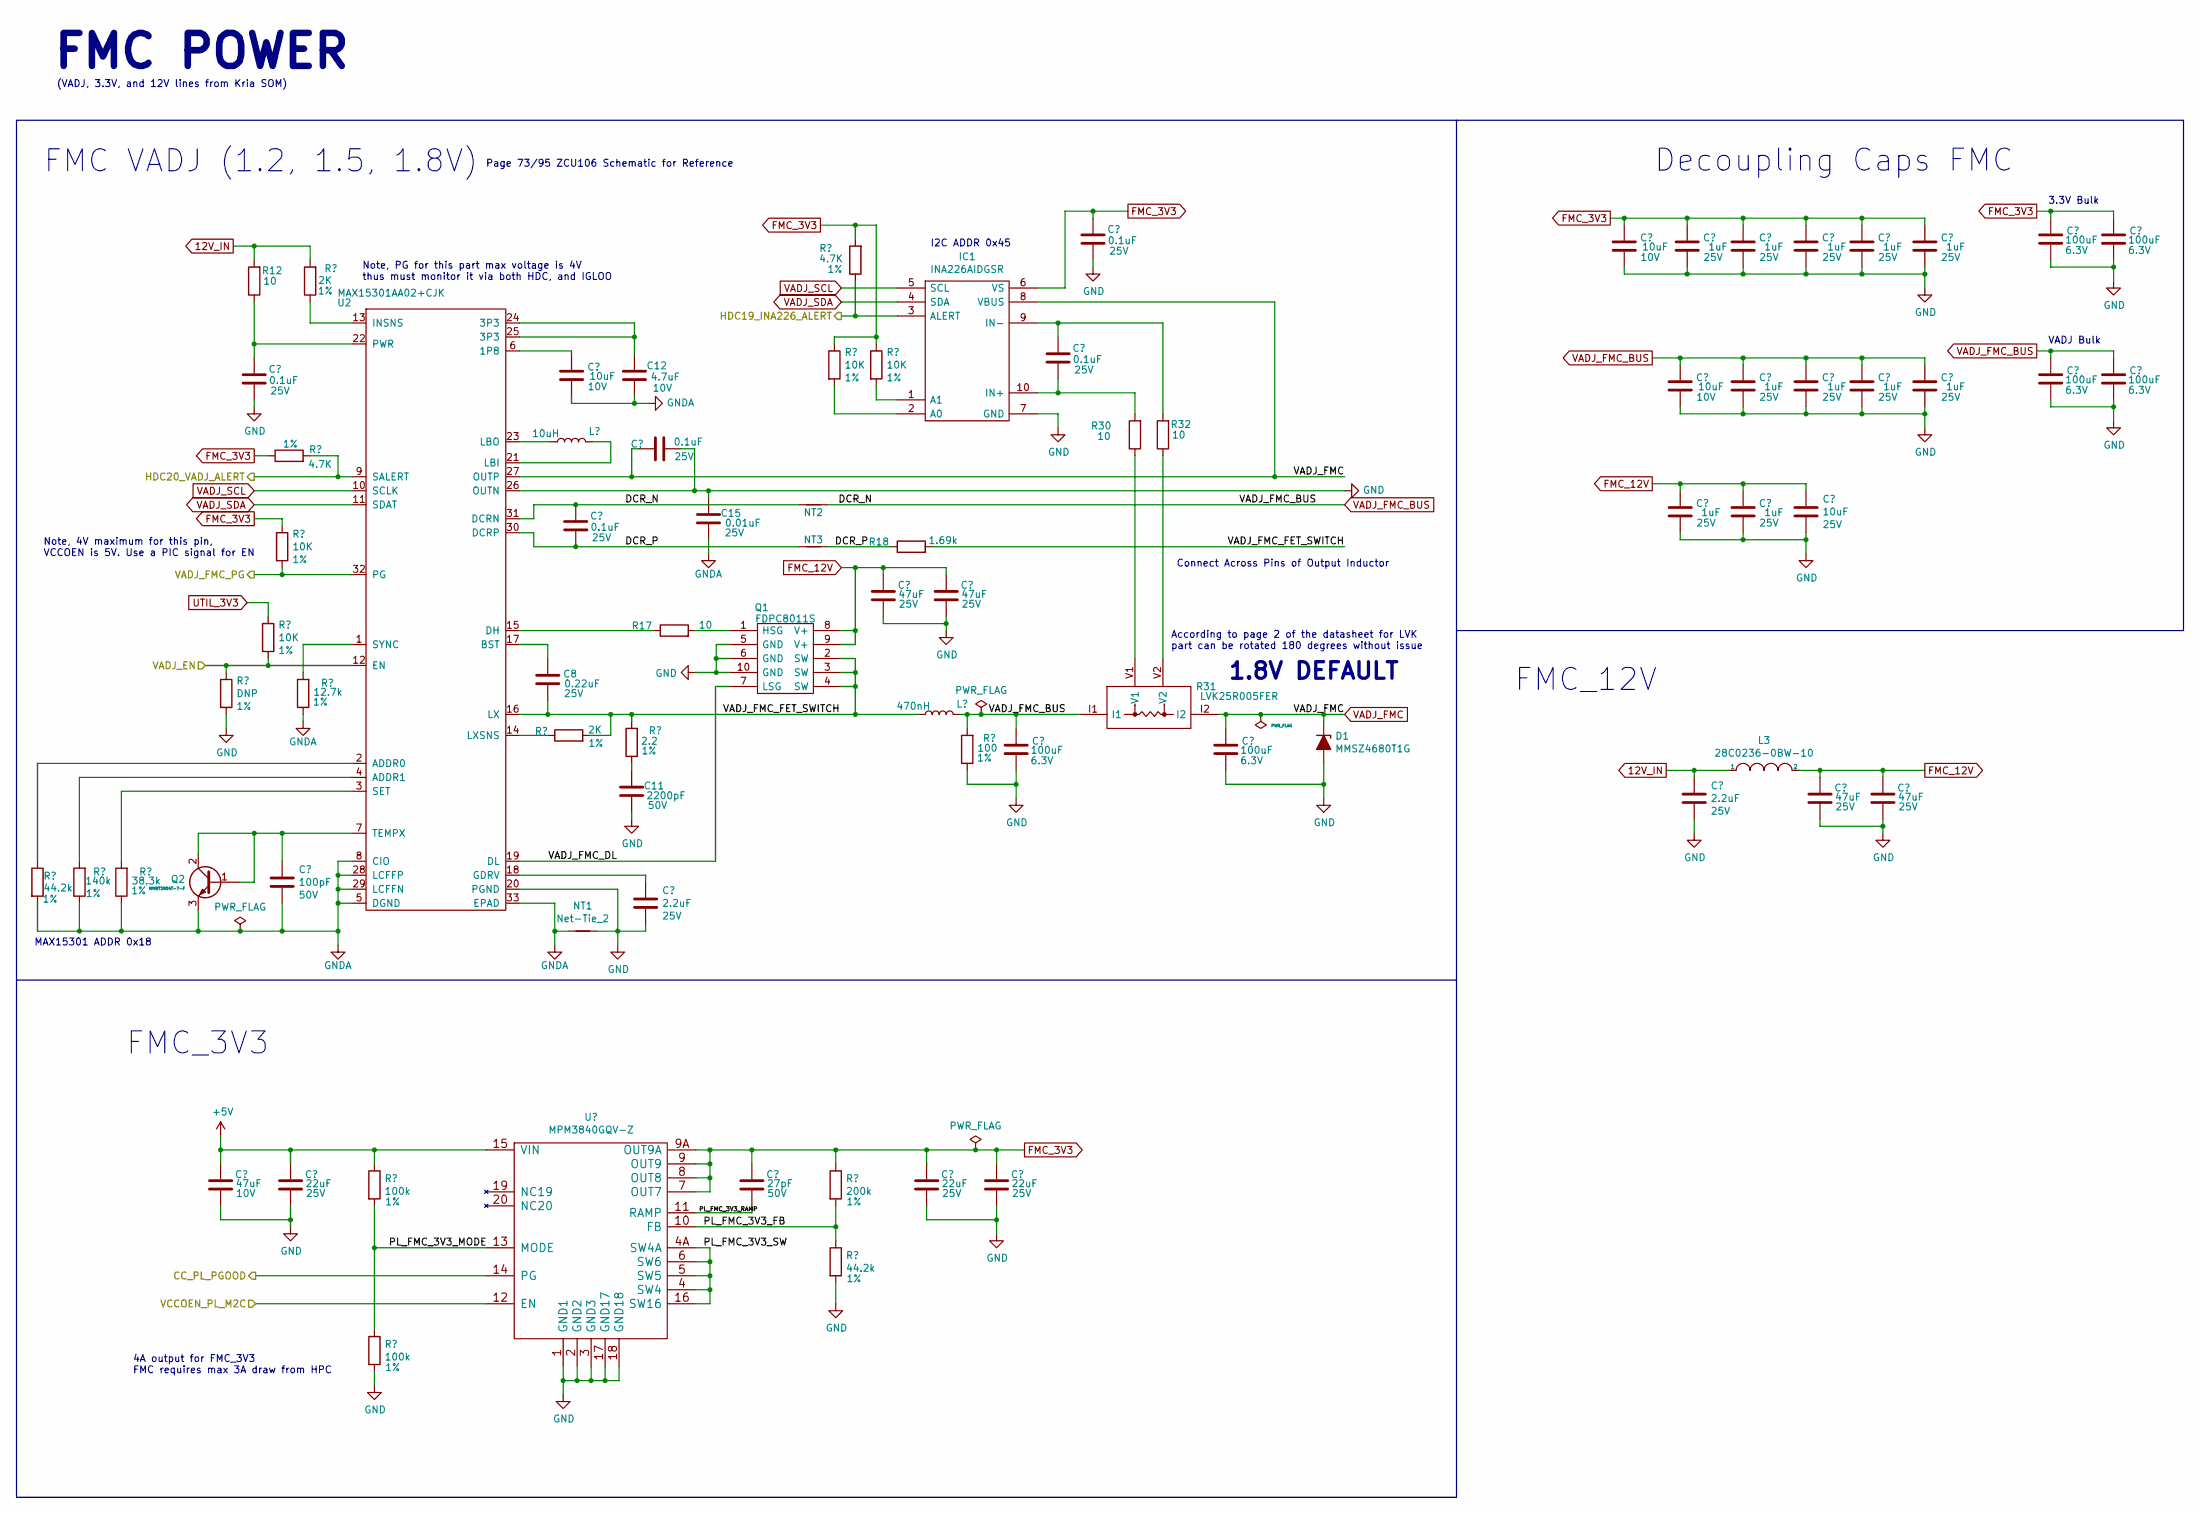
[picture p13: schematic FMC_PWR.kicad_sch]

Parts:
C1: 47uF; C_0805_2012Metric; Tolerance +-20%; Voltage 10V; PartNumber GRM21BR61A476ME15L
C2, C4, C5: 22uF; C_0805_2012Metric; Tolerance +-20%; Voltage 25V; PartNumber CC0805MKX5R8BB226
C3: 27pF; C_0402_1005Metric; Tolerance +-5%; Voltage 50V; PartNumber 04025A270JAT2A
C7, C10, C14, C20, C21: 0.1uF; C_0402_1005Metric; Tolerance +-10%; Voltage 25V; PartNumber TMK105BJ104KVHF
C8: 0.22uF; C_0402_1005Metric; Tolerance +-10%; Voltage 25V; PartNumber C1005X5R1E224K050BC
C9, C23, C24: 10uF; C_0402_1005Metric; Tolerance +-20%; Voltage 10V; PartNumber CL05A106MP5NUNC
C11: 2200pF; C_0402_1005Metric; Tolerance +-5%; Voltage 50V; PartNumber GRM155R71H222JA01J
C12: 4.7uF; C_0402_1005Metric; Tolerance +-10%; Voltage 10V; PartNumber CL05A475KP5NRNC
C13, C41: 2.2uF; C_0805_2012Metric; Tolerance +-10%; Voltage 25V; PartNumber CL21B225KAFNNNE
C15: 0.01uF; C_0402_1005Metric; Tolerance +-10%; Voltage 25V; PartNumber 04023D103KAT2A
C16, C17, C42, C43: 47uF; C_1206_3216Metric; Tolerance +-20%; Voltage 25V; PartNumber C3216X5R1E476M160AC
C18, C22, C37, C38, C39, C40: 100uF; C_1210_3225Metric; Tolerance +-20%; Voltage 6.3V; PartNumber C3225X6S0J107M250AB
C19: 100pF; C_0402_1005Metric; Tolerance +-10%; Voltage 50V; PartNumber CC0402KRX7R9BB101
C25, C26, C27, C28, C29, C30, C31, C33, C34, C35, C36: 1uF; C_0402_1005Metric; Tolerance +-10%; Voltage 25V; PartNumber C1005X5R1E105K050BE
C32: 10uF; C_1206_3216Metric; Tolerance +-10%; Voltage 25V; PartNumber CL31B106KAHNFNE
D1: MMSZ4680T1G; D_SOD-123; PartNumber MMSZ4680T1G
IC1: INA226AIDGSR; Mouser Part Number 595-INA226AIDGSR
L1: 10uH; L_1008_2520Metric; PartNumber 74479887310A
L2: 470nH; 744316047; PartNumber 744316047
L3: 28C0236-0BW-10; 28C02360BW10
NT1: Net-Tie_2; NetTie-2_SMD_Pad0.5mm
NT2, NT3: Net-Tie_2; Short_0201
Q1: FDPC8011S; Mouser Part Number 512-FDPC8011S
Q2: MMBT3904T-7-F
R1, R2: 100k; R_0402_1005Metric; PartNumber CRCW0402100KFKEDHP
R3: 200k; R_0402_1005Metric; PartNumber ERJ-2RKF2003X
R4, R20: 44.2k; R_0402_1005Metric; PartNumber ERJ-2RKF4422X
R12, R17, R30, R32: 10; R_0402_1005Metric; PartNumber ERJ-2RKF10R0X
R13, R27, R29, R50: 10K; R_0402_1005Metric; Tolerance 1%; PartNumber ERJ-2RKF1002X
R14, R15: 2K; R_0402_1005Metric; Tolerance 1%; PartNumber ERJ-2RKF2001X
R16: 2.2; R_0603_1608Metric; Tolerance 1%; PartNumber ERJ-3RQF2R2V
R18: 1.69k; R_0402_1005Metric; PartNumber ERJ-2RKF1691X
R19: 100; R_0402_1005Metric; Tolerance 1%; PartNumber ERJ-2RKF1000X
R21: 140k; R_0402_1005Metric; Tolerance 1%; PartNumber ERJ-2RKF1403X
R22: 38.3k; R_0402_1005Metric; Tolerance 1%; PartNumber ERJ-2RKF3832X
R23, R28: 4.7K; R_0402_1005Metric; Tolerance 1%; PartNumber CRCW04024K70FKED
R26: 12.7k; R_0402_1005Metric; Tolerance 1%; PartNumber ERJ-2RKF1272X
R31: LVK25R005FER; Mouser Part Number 588-LVK25R005FER
R53: DNP; R_0402_1005Metric; Tolerance 1%; PartNumber ERJ-2RKF1002X
U1: MPM3840GQV-Z; MPM3840GQV-P
U2: MAX15301AA02+CJK

Connections:
12V_IN: C41.1, L3.1, R12.2, R14.2
+5V: C1.2, C2.2, R1.1, U1.15 (VIN)
CC_PL_PGOOD: U1.14 (PG)
DCR_P: C10.2, NT3.1, NT3.2, R18.1, U2.30 (DCRP)
FMC_3V3: C3.2, C4.2, C5.2, C21.1, C23.2, C26.2, C27.2, C30.2, C33.2, C35.2, C37.2, C39.2, IC1.6 (VS), R3.1, R13.1, R23.1, R27.1, R28.2, R29.1, U1.7 (OUT7), U1.8 (OUT8), U1.9 (OUT9), U1.9A (OUT9A)
FMC_12V: C16.2, C17.2, C25.2, C29.2, C32.1, C42.2, C43.2, L3.2, Q1.8 (V+), Q1.9 (V+)
GND: C1.1, C2.1, C4.1, C5.1, C7.2, C11.1, C13.2, C14.1, C15.2, C16.1, C17.1, C18.1, C21.2, C22.1, C23.1, C24.1, C25.1, C26.1, C27.1, C28.1, C29.1, C30.1, C31.1, C32.2, C33.1, C34.1, C35.1, C36.1, C37.1, C38.1, C39.1, C40.1, C41.2, C42.1, C43.1, D1.2 (A), IC1.7 (GND), NT1.2, Q1.5 (GND), Q1.6 (GND), Q1.10 (GND), R2.2, R4.2, R19.1, R53.2, U1.1 (GND1), U1.2 (GND2), U1.3 (GND3), U1.17 (GND17), U1.18 (GND18), U2.20 (PGND), U2.26 (OUTN)
GNDA: C9.1, C12.2, C15.1, C19.2, NT1.1, Q2.3 (E), R20.2, R21.1, R22.1, R26.1, U2.5 (DGND), U2.8 (CIO), U2.28 (LCFFP), U2.29 (LCFFN), U2.33 (EPAD)
HDC19_INA226_ALERT: IC1.3 (ALERT), R28.1
HDC20_VADJ_ALERT: R23.2, U2.9 (SALERT)
unnamed: C7.1, R12.1, U2.22 (PWR)
unnamed: C8.2, U2.17 (BST)
unnamed: C9.2, U2.6 (1P8)
unnamed: C11.2, R16.1
unnamed: C12.1, U2.24 (3P3), U2.25 (3P3)
unnamed: C13.1, U2.18 (GDRV)
unnamed: C19.1, Q2.1 (B), Q2.2 (C), U2.7 (TEMPX)
unnamed: C20.1, IC1.9 (IN-), R32.2
unnamed: C20.2, IC1.10 (IN+), R30.2
unnamed: IC1.1 (A1), R29.2
unnamed: IC1.2 (A0), R27.2
unnamed: L1.1, U2.23 (LBO)
unnamed: L1.2, U2.21 (LBI)
unnamed: Q1.1 (HSG), R17.2
unnamed: R14.1, U2.13 (INSNS)
unnamed: R15.1, U2.14 (LXSNS)
unnamed: R17.1, U2.15 (DH)
unnamed: R20.1, U2.2 (ADDR0)
unnamed: R21.2, U2.4 (ADDR1)
unnamed: R22.2, U2.3 (SET)
unnamed: R26.2, U2.1 (SYNC)
unnamed: R30.1, R31.V1
unnamed: R31.V2, R32.1
PL_FMC_3V3_FB: R3.2, R4.1, U1.10 (FB)
PL_FMC_3V3_MODE: R1.2, R2.1, U1.13 (MODE)
PL_FMC_3V3_RAMP: C3.1, U1.11 (RAMP)
PL_FMC_3V3_SW: U1.4 (SW4), U1.4A (SW4A), U1.5 (SW5), U1.6 (SW6), U1.16 (SW16)
UTIL_3V3: R50.1
VADJ_EN: R50.2, R53.1, U2.12 (EN)
VADJ_FMC: C14.2, C22.2, D1.1 (K), IC1.8 (VBUS), R31.I2, U2.27 (OUTP)
VADJ_FMC_BUS: C10.1, C18.2, C24.2, C28.2, C31.2, C34.2, C36.2, C38.2, C40.2, L2.2, NT2.1, NT2.2, R19.2, R31.I1, U2.31 (DCRN)
VADJ_FMC_DL: Q1.7 (LSG), U2.19 (DL)
VADJ_FMC_FET_SWITCH: C8.1, L2.1, Q1.2 (SW), Q1.3 (SW), Q1.4 (SW), R15.2, R16.2, R18.2, U2.16 (LX)
VADJ_FMC_PG: R13.2, U2.32 (PG)
VADJ_SCL: IC1.5 (SCL), U2.10 (SCLK)
VADJ_SDA: IC1.4 (SDA), U2.11 (SDAT)
VCCOEN_PL_M2C: U1.12 (EN)

Notes on the sheet:
(VADJ, 3.3V, and 12V lines from Kria SOM)
FMC_12V
Note, PG for this part max voltage is 4V thus must monitor it via both HDC, and IGLOO
I2C ADDR 0x45
1.8V DEFAULT
VADJ Bulk
Connect Across Pins of Output Inductor
FMC VADJ (1.2, 1.5, 1.8V)
MAX15301 ADDR 0x18
According to page 2 of the datasheet for LVK part can be rotated 180 degrees without issue
FMC POWER
FMC_3V3
4A output for FMC_3V3 FMC requires max 3A draw from HPC
Decoupling Caps FMC
Page 73/95 ZCU106 Schematic for Reference
Note, 4V maximum for this pin, VCCOEN is 5V. Use a PIC signal for EN
3.3V Bulk
