ApotheoTech/Aper-Oculus/Kria_Reset.kicad_sch

## KiCad design Kria_Reset.kicad_sch (2023-12-22)

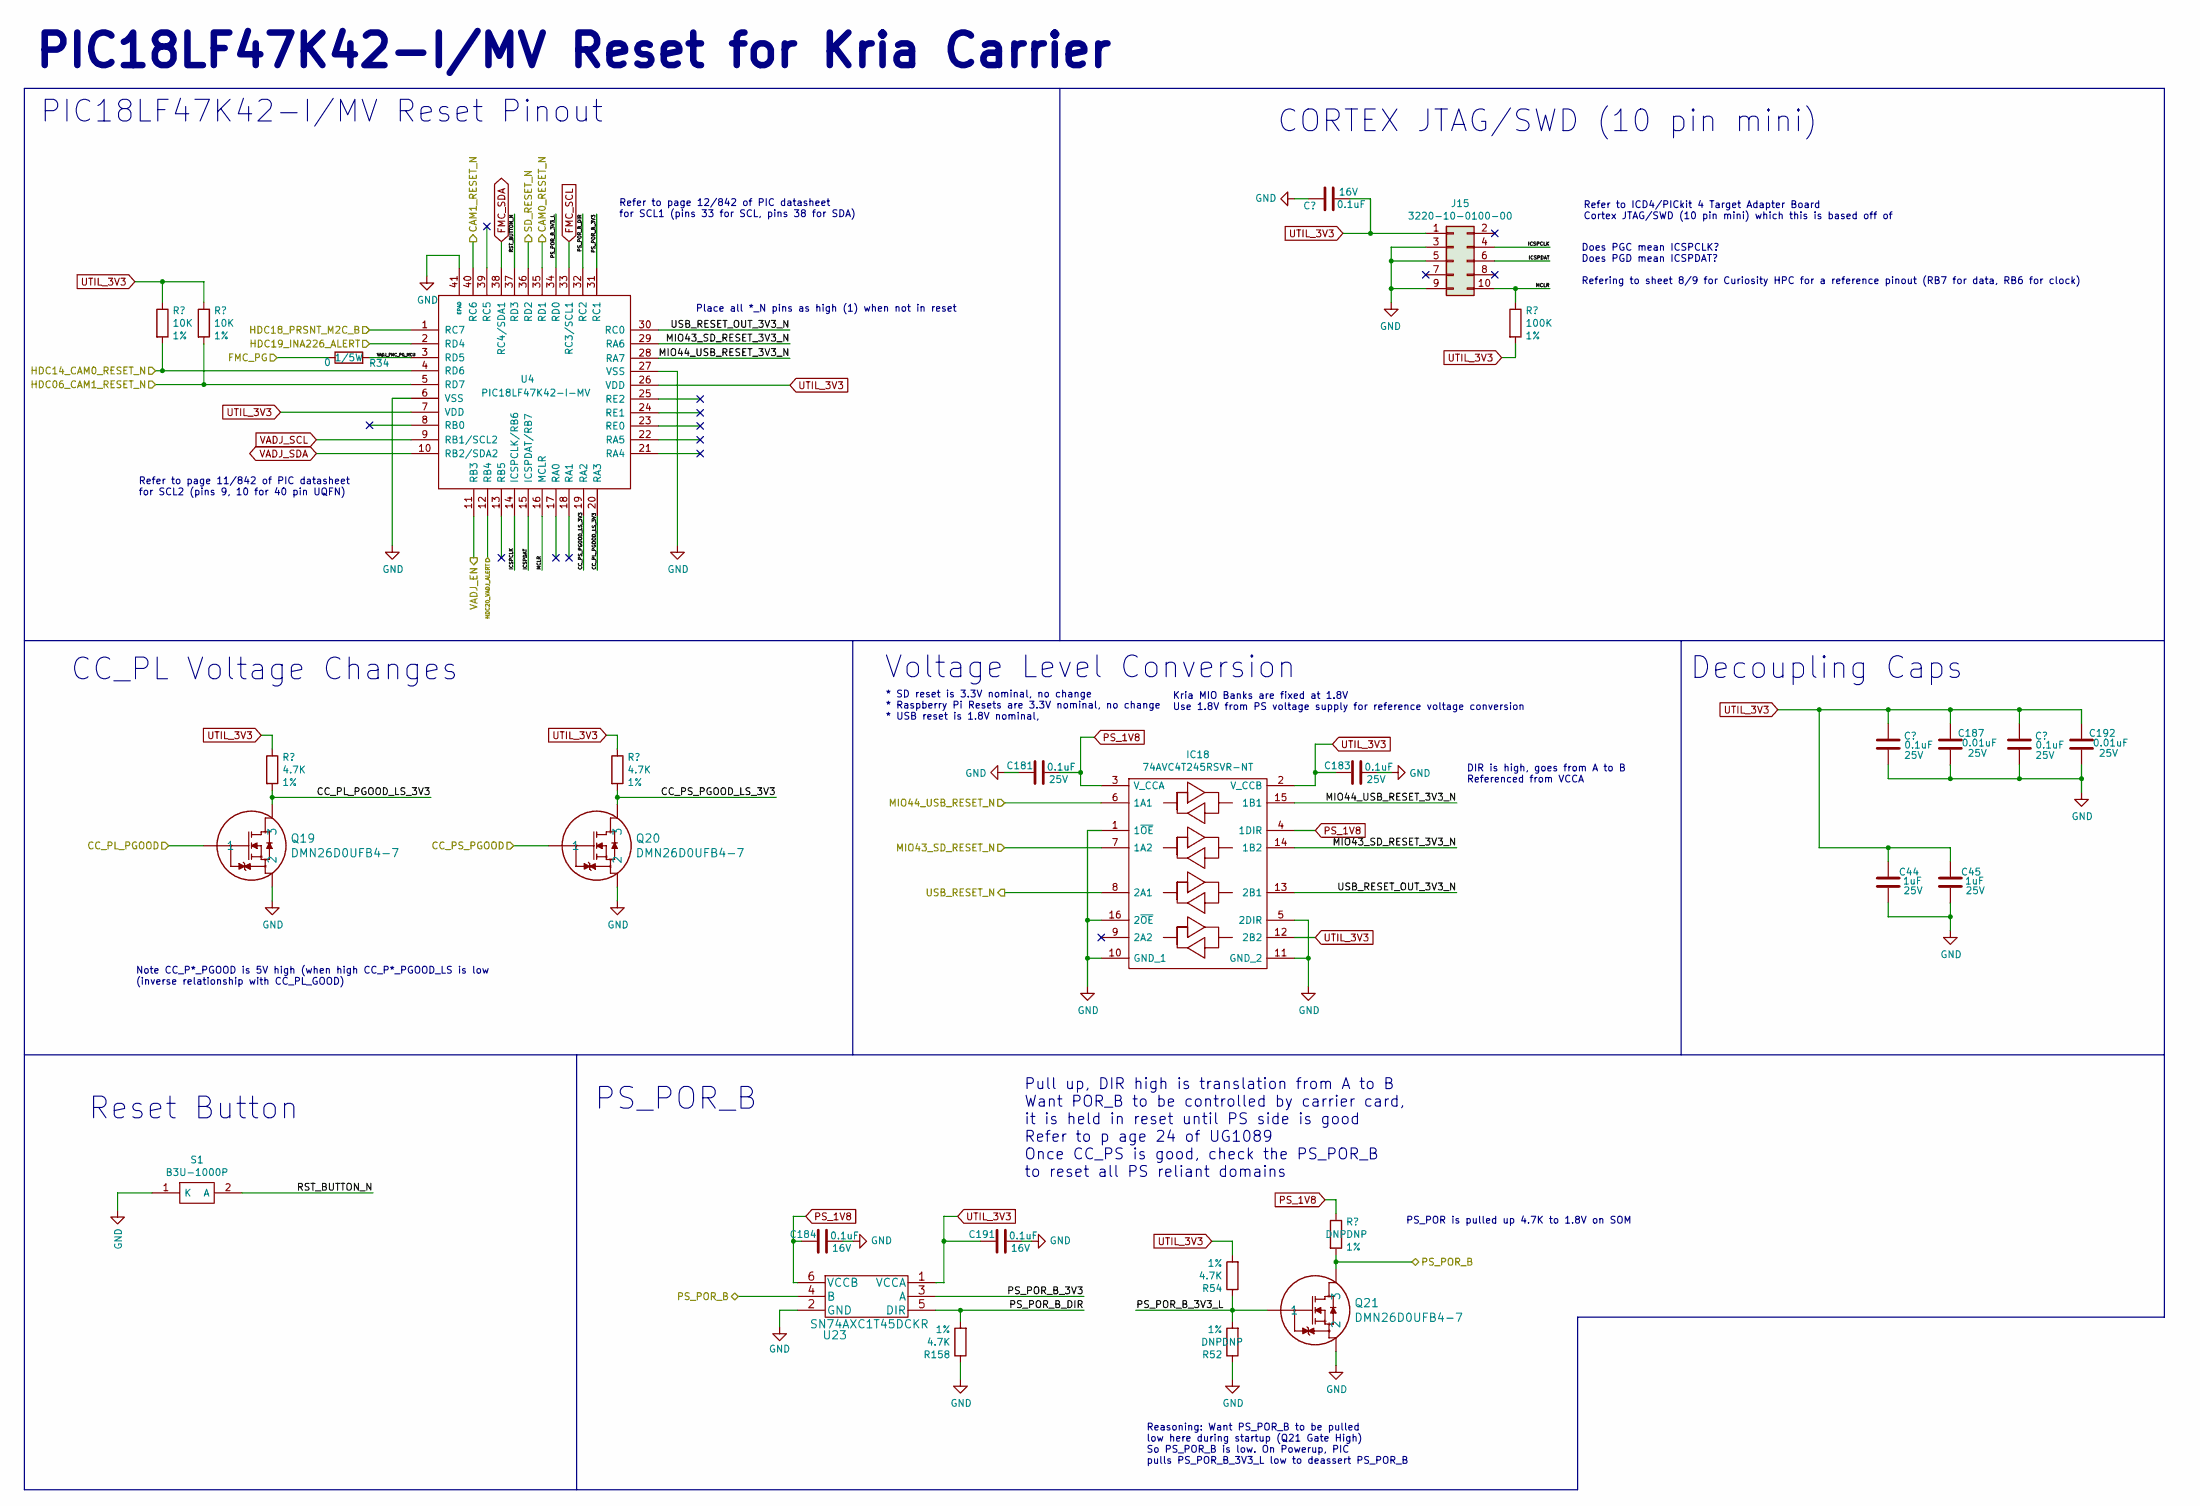
[picture p14: schematic Kria_Reset.kicad_sch]

Parts:
C44, C45: 1uF; C_0402_1005Metric; Tolerance +-10%; Voltage 25V; PartNumber C1005X5R1E105K050BE‎
C181, C183, C185, C189: 0.1uF; C_0402_1005Metric; Tolerance +-10%; Voltage 25V; PartNumber TMK105BJ104KVHF
C182, C184, C191: 0.1uF; C_0402_1005Metric; Tolerance +-10%; Voltage 16V; PartNumber EMK105B7104KV-F
C187, C192: 0.01uF; C_0402_1005Metric; Tolerance +-10%; Voltage 25V; PartNumber 04023D103KAT2A
IC18: 74AVC4T245RSVR-NT; Mouser Part Number 595-74AVC4T245RSVRNT
J15: 3220-10-0100-00
Q19, Q20, Q21: DMN26D0UFB4-7
R34: 0; R_0402_1005Metric; PartNumber CRCW04020000Z0EDHP
R35: 100K; R_0402_1005Metric; Tolerance 1%; PartNumber CRCW0402100KFKEDHP
R42, R43: 10K; R_0402_1005Metric; Tolerance 1%; PartNumber ERJ-2RKF1002X
R52, R159: DNP; R_0402_1005Metric; Tolerance 1%; PartNumber CRCW04024K70FKED
R54, R155, R157, R158: 4.7K; R_0402_1005Metric; Tolerance 1%; PartNumber CRCW04024K70FKED
S1: B3U-1000P; Mouser Part Number 653-B3U-1000P
U4: PIC18LF47K42-I-MV
U23: SN74AXC1T45DCKR

Connections:
CAM0_RESET_N: U4.35 (RD1)
CAM1_RESET_N: U4.40 (RC6)
CC_PL_PGOOD: Q19.1
CC_PL_PGOOD_LS_3V3: Q19.3, R155.2, U4.20 (RA3)
CC_PS_PGOOD: Q20.1
CC_PS_PGOOD_LS_3V3: Q20.3, R157.2, U4.19 (RA2)
FMC_PG: R34.1
FMC_SCL: U4.33 (RC3/SCL1)
FMC_SDA: U4.38 (RC4/SDA1)
GND: C44.1, C45.1, C181.1, C182.1, C183.2, C184.2, C185.1, C187.1, C189.1, C191.2, C192.1, IC18.1 (1~OE), IC18.5 (2DIR), IC18.10 (GND_1), IC18.11 (GND_2), IC18.16 (2~OE), J15.3, J15.5, J15.9, Q19.2, Q20.2, Q21.2, R52.1, R158.1, S1.1 (K), U4.6 (VSS), U4.27 (VSS), U4.41 (EPAD), U23.2 (GND)
HDC06_CAM1_RESET_N: R43.2, U4.5 (RD7)
HDC14_CAM0_RESET_N: R42.2, U4.4 (RD6)
HDC18_PRSNT_M2C_B: U4.1 (RC7)
HDC19_INA226_ALERT: U4.2 (RD4)
HDC20_VADJ_ALERT: U4.12 (RB4)
ICSPCLK: J15.4, U4.14 (ICSPCLK/RB6)
ICSPDAT: J15.6, U4.15 (ICSPDAT/RB7)
MCLR: J15.10, R35.1, U4.16 (MCLR)
MIO43_SD_RESET_3V3_N: IC18.14 (1B2), U4.29 (RA6)
MIO43_SD_RESET_N: IC18.7 (1A2)
MIO44_USB_RESET_3V3_N: IC18.15 (1B1), U4.28 (RA7)
MIO44_USB_RESET_N: IC18.6 (1A1)
PS_1V8: C181.2, C184.1, IC18.3 (V_CCA), IC18.4 (1DIR), R159.1, U23.6 (VCCB)
PS_POR_B: Q21.3, R159.2, U23.4 (B)
PS_POR_B_3V3: U4.31 (RC1), U23.3 (A)
PS_POR_B_3V3_L: Q21.1, R52.2, R54.1, U4.34 (RD0)
PS_POR_B_DIR: R158.2, U4.32 (RC2), U23.5 (DIR)
RST_BUTTON_N: S1.2 (A), U4.37 (RD3)
SD_RESET_N: U4.36 (RD2)
USB_RESET_N: IC18.8 (2A1)
USB_RESET_OUT_3V3_N: IC18.13 (2B1), U4.30 (RC0)
UTIL_3V3: C44.2, C45.2, C182.2, C183.1, C185.2, C187.2, C189.2, C191.1, C192.2, IC18.2 (V_CCB), IC18.12 (2B2), J15.1, R35.2, R42.1, R43.1, R54.2, R155.1, R157.1, U4.7 (VDD), U4.26 (VDD), U23.1 (VCCA)
VADJ_EN: U4.11 (RB3)
VADJ_FMC_PG_MCU: R34.2, U4.3 (RD5)
VADJ_SCL: U4.9 (RB1/SCL2)
VADJ_SDA: U4.10 (RB2/SDA2)

Notes on the sheet:
Decoupling Caps
Note CC_P*_PGOOD is 5V high (when high CC_P*_PGOOD_LS is low (inverse relationship with CC_PL_GOOD)
Refer to page 12/842 of PIC datasheet for SCL1 (pins 33 for SCL, pins 38 for SDA)
PS_POR is pulled up 4.7K to 1.8V on SOM
Refer to page 11/842 of PIC datasheet for SCL2 (pins 9, 10 for 40 pin UQFN)
* SD reset is 3.3V nominal, no change * Raspberry Pi Resets are 3.3V nominal, no change * USB reset is 1.8V nominal,
Voltage Level Conversion
Pull up, DIR high is translation from A to B Want POR_B to be controlled by carrier card, it is held in reset until PS side is good Refer to p age 24 of UG1089 Once CC_PS is good, check the PS_POR_B to reset all PS reliant domains
Reasoning: Want PS_POR_B to be pulled low here during startup (Q21 Gate High) So PS_POR_B is low. On Powerup, PIC pulls PS_POR_B_3V3_L low to deassert PS_POR_B
CC_PL Voltage Changes
PIC18LF47K42-I/MV Reset Pinout
PIC18LF47K42-I/MV Reset for Kria Carrier
PS_POR_B
Reset Button
Place all *_N pins as high (1) when not in reset
DIR is high, goes from A to B Referenced from VCCA
CORTEX JTAG/SWD (10 pin mini)
Does PGC mean ICSPCLK? Does PGD mean ICSPDAT? Refering to sheet 8/9 for Curiosity HPC for a reference pinout (RB7 for data, RB6 for clock)
Kria MIO Banks are fixed at 1.8V Use 1.8V from PS voltage supply for reference voltage conversion
Refer to ICD4/PICkit 4 Target Adapter Board Cortex JTAG/SWD (10 pin mini) which this is based off of
