ApotheoTech/Aper-Oculus/MIPI_Conn.kicad_sch

## KiCad design MIPI_Conn.kicad_sch (2023-12-22)

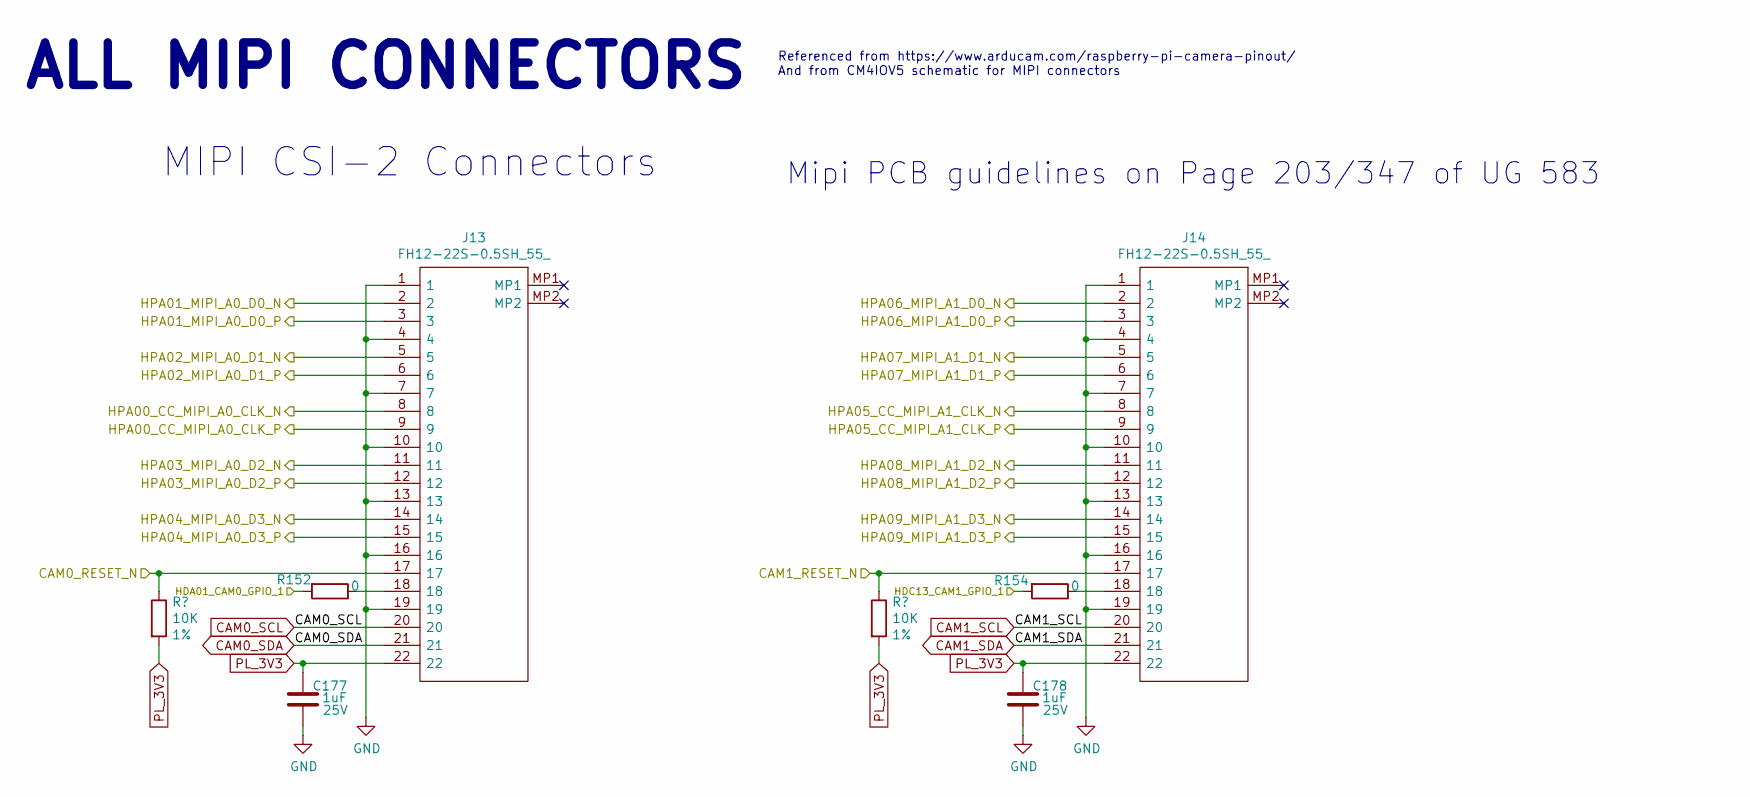
[picture p15: schematic MIPI_Conn.kicad_sch]

Parts:
C177, C178: 1uF; C_0402_1005Metric; Tolerance +-10%; Voltage 25V; PartNumber C1005X5R1E105K050BE‎
J13, J14: FH12-22S-0.5SH_55_; FH1222S05SH55; Mouser Part Number 798-FH12-22S-0.5SH55
R151, R153: 10K; R_0402_1005Metric; Tolerance 1%; PartNumber ERJ-2RKF1002X
R152, R154: 0; R_0402_1005Metric; PartNumber CRCW04020000Z0EDHP

Connections:
CAM0_RESET_N: J13.17, R151.1
CAM0_SCL: J13.20
CAM0_SDA: J13.21
CAM1_RESET_N: J14.17, R153.1
CAM1_SCL: J14.20
CAM1_SDA: J14.21
GND: C177.1, C178.1, J13.1, J13.4, J13.7, J13.10, J13.13, J13.16, J13.19, J14.1, J14.4, J14.7, J14.10, J14.13, J14.16, J14.19
HDA01_CAM0_GPIO_1: R152.2
HDC13_CAM1_GPIO_1: R154.2
HPA00_CC_MIPI_A0_CLK_N: J13.8
HPA00_CC_MIPI_A0_CLK_P: J13.9
HPA01_MIPI_A0_D0_N: J13.2
HPA01_MIPI_A0_D0_P: J13.3
HPA02_MIPI_A0_D1_N: J13.5
HPA02_MIPI_A0_D1_P: J13.6
HPA03_MIPI_A0_D2_N: J13.11
HPA03_MIPI_A0_D2_P: J13.12
HPA04_MIPI_A0_D3_N: J13.14
HPA04_MIPI_A0_D3_P: J13.15
HPA05_CC_MIPI_A1_CLK_N: J14.8
HPA05_CC_MIPI_A1_CLK_P: J14.9
HPA06_MIPI_A1_D0_N: J14.2
HPA06_MIPI_A1_D0_P: J14.3
HPA07_MIPI_A1_D1_N: J14.5
HPA07_MIPI_A1_D1_P: J14.6
HPA08_MIPI_A1_D2_N: J14.11
HPA08_MIPI_A1_D2_P: J14.12
HPA09_MIPI_A1_D3_N: J14.14
HPA09_MIPI_A1_D3_P: J14.15
unnamed: J13.18, R152.1
unnamed: J14.18, R154.1
PL_3V3: C177.2, C178.2, J13.22, J14.22, R151.2, R153.2

Notes on the sheet:
Referenced from https://www.arducam.com/raspberry-pi-camera-pinout/ And from CM4IOV5 schematic for MIPI connectors
ALL MIPI CONNECTORS
Mipi PCB guidelines on Page 203/347 of UG 583
MIPI CSI-2 Connectors
