ApotheoTech/Aper-Oculus/Micro_SD.kicad_sch

## KiCad design Micro_SD.kicad_sch (2023-12-22)

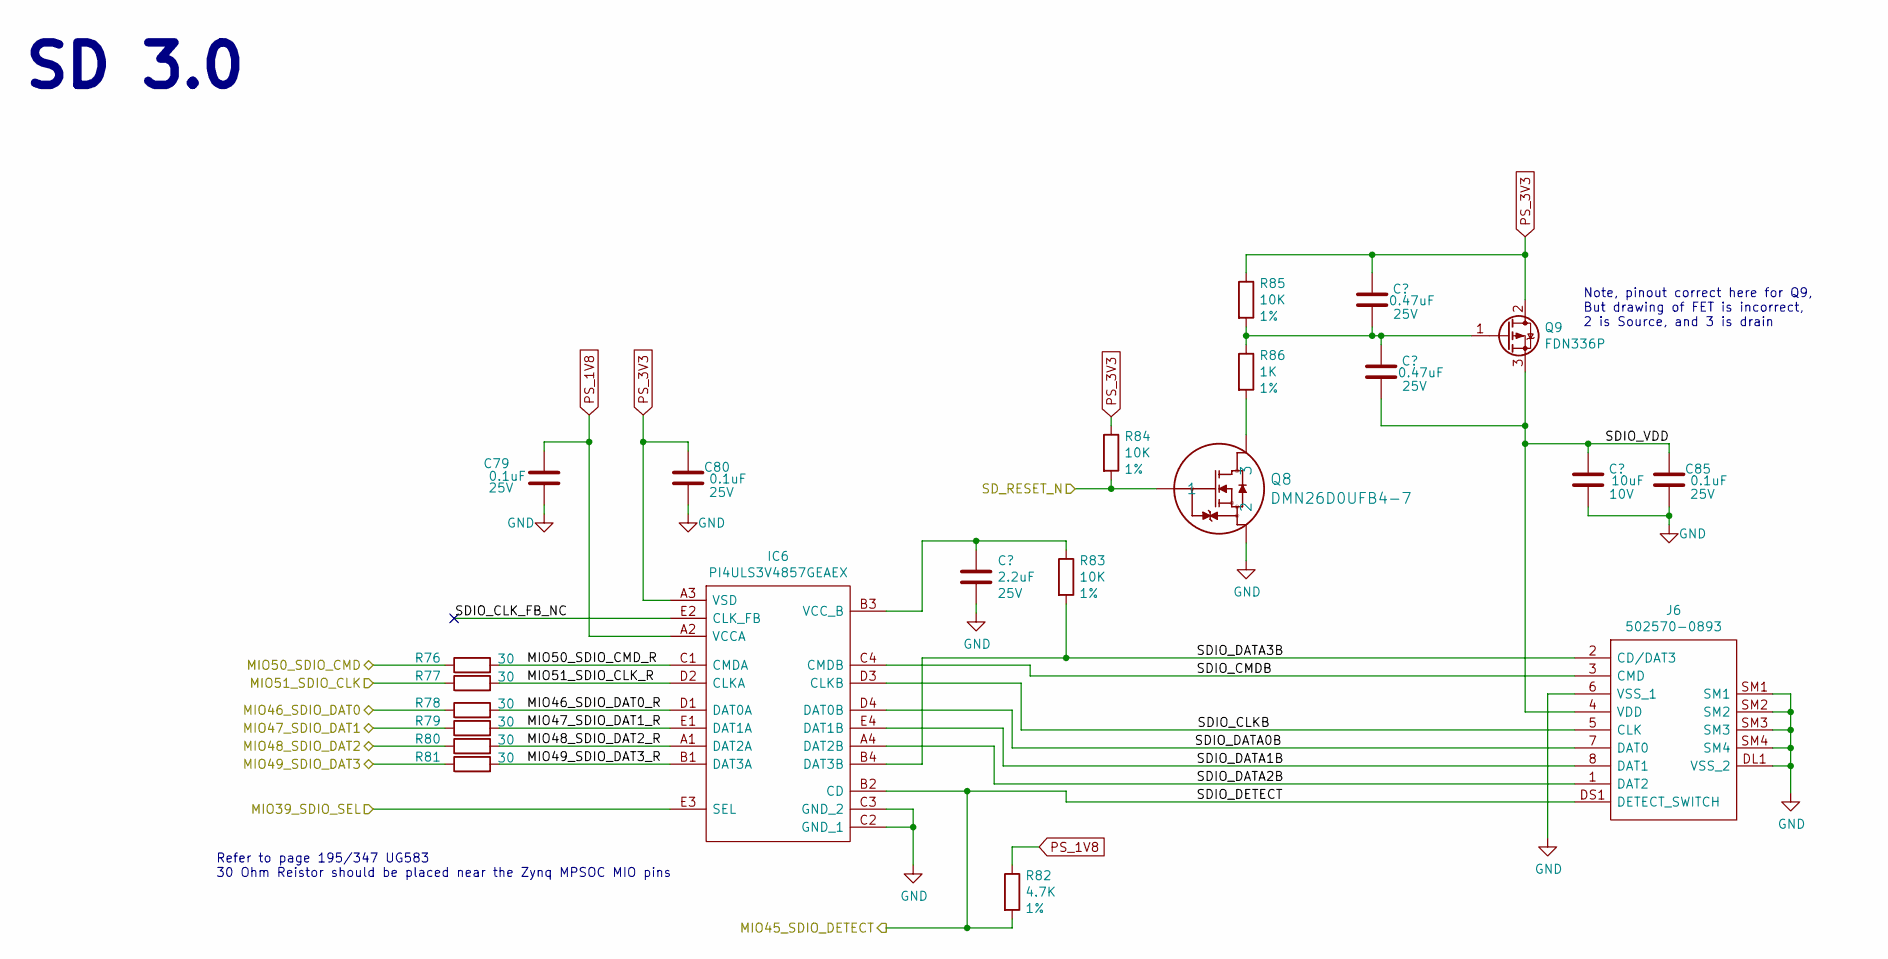
[picture p16: schematic Micro_SD.kicad_sch]

Parts:
C79, C80, C85: 0.1uF; C_0402_1005Metric; Tolerance +-10%; Voltage 25V; PartNumber TMK105BJ104KVHF
C81: 2.2uF; C_0402_1005Metric; Tolerance +-10%; Voltage 25V; PartNumber GRM155R61E225KE1D
C82, C83: 0.47uF; C_0402_1005Metric; Tolerance +-10%; Voltage 25V; PartNumber GRT155R61E474KE01D
C84: 10uF; C_0603_1608Metric; Tolerance +-10%; Voltage 10V; PartNumber 0603ZD106KAT2A
IC6: PI4ULS3V4857GEAEX; Mouser Part Number 621-I4ULS3V4857GEAEX
J6: 502570-0893; 5025700893; Mouser Part Number 538-502570-0893
Q8: DMN26D0UFB4-7
Q9: FDN336P; FDN336P_SOT23
R76, R77, R78, R79, R80, R81: 30; R_0402_1005Metric; PartNumber ERJ-2RKF30R0X
R82: 4.7K; R_0402_1005Metric; Tolerance 1%; PartNumber CRCW04024K70FKED
R83, R84, R85: 10K; R_0402_1005Metric; Tolerance 1%; PartNumber ERJ-2RKF1002X
R86: 1K; R_0402_1005Metric; Tolerance 1%; PartNumber ERJ-2RKF1001X‎

Connections:
GND: C79.1, C80.1, C81.2, C84.1, C85.1, IC6.C2 (GND_1), IC6.C3 (GND_2), J6.6 (VSS_1), J6.DL1 (VSS_2), J6.SM1, J6.SM2, J6.SM3, J6.SM4, Q8.2
MIO39_SDIO_SEL: IC6.E3 (SEL)
MIO45_SDIO_DETECT: IC6.B2 (CD), J6.DS1 (DETECT_SWITCH), R82.2
MIO46_SDIO_DAT0: R78.1
MIO46_SDIO_DAT0_R: IC6.D1 (DAT0A), R78.2
MIO47_SDIO_DAT1: R79.1
MIO47_SDIO_DAT1_R: IC6.E1 (DAT1A), R79.2
MIO48_SDIO_DAT2: R80.1
MIO48_SDIO_DAT2_R: IC6.A1 (DAT2A), R80.2
MIO49_SDIO_DAT3: R81.1
MIO49_SDIO_DAT3_R: IC6.B1 (DAT3A), R81.2
MIO50_SDIO_CMD: R76.1
MIO50_SDIO_CMD_R: IC6.C1 (CMDA), R76.2
MIO51_SDIO_CLK: R77.1
MIO51_SDIO_CLK_R: IC6.D2 (CLKA), R77.2
unnamed: C81.1, IC6.B3 (VCC_B), R83.1
unnamed: C82.1, C83.2, Q9.1 (G), R85.2, R86.1
unnamed: Q8.3, R86.2
PS_1V8: C79.2, IC6.A2 (VCCA), R82.1
PS_3V3: C80.2, C82.2, IC6.A3 (VSD), Q9.2 (D), R84.1, R85.1
SDIO_CLKB: IC6.D3 (CLKB), J6.5 (CLK)
SDIO_CLK_FB_NC: IC6.E2 (CLK_FB)
SDIO_CMDB: IC6.C4 (CMDB), J6.3 (CMD)
SDIO_DATA0B: IC6.D4 (DAT0B), J6.7 (DAT0)
SDIO_DATA1B: IC6.E4 (DAT1B), J6.8 (DAT1)
SDIO_DATA2B: IC6.A4 (DAT2B), J6.1 (DAT2)
SDIO_DATA3B: IC6.B4 (DAT3B), J6.2 (CD/DAT3), R83.2
SDIO_VDD: C83.1, C84.2, C85.2, J6.4 (VDD), Q9.3 (S)
SD_RESET_N: Q8.1, R84.2

Notes on the sheet:
SD 3.0
Refer to page 195/347 UG583 30 Ohm Reistor should be placed near the Zynq MPSOC MIO pins
Note, pinout correct here for Q9, But drawing of FET is incorrect, 2 is Source, and 3 is drain
