ApotheoTech/Aper-Oculus/PL_Power.kicad_sch

## KiCad design PL_Power.kicad_sch (2023-12-22)

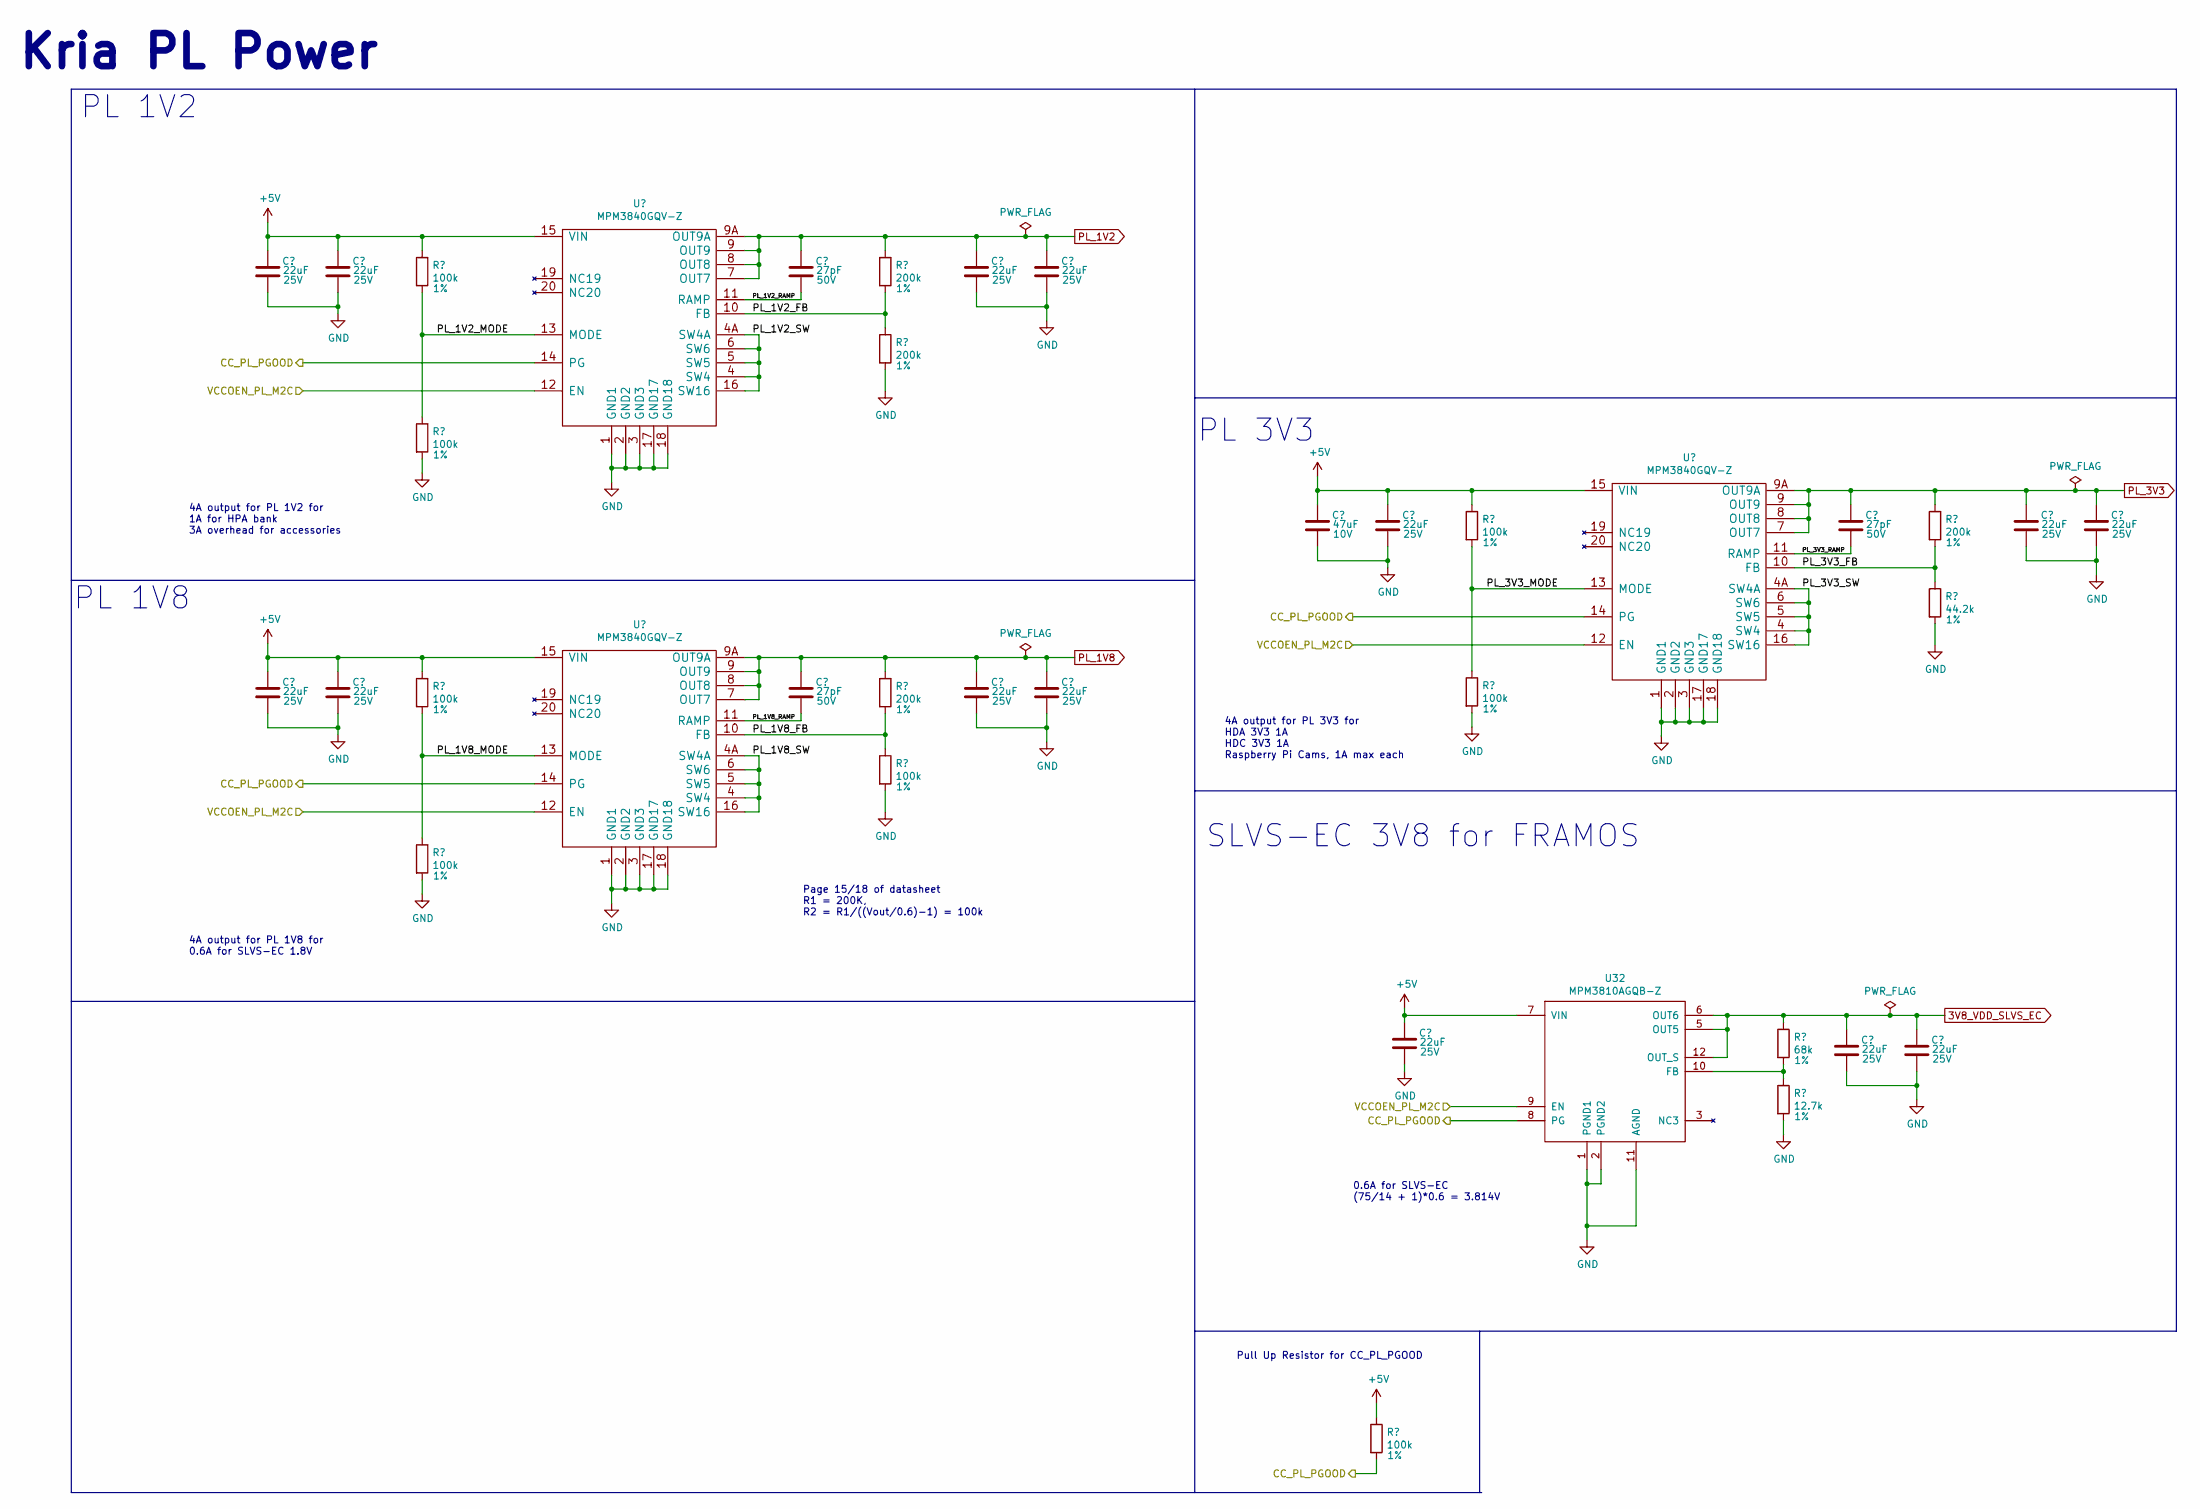
[picture p17: schematic PL_Power.kicad_sch]

Parts:
C236, C237, C238, C239, C242, C243, C244, C245, C247, C248, C249, C251, C252, C253: 22uF; C_0805_2012Metric; Tolerance +-20%; Voltage 25V; PartNumber CC0805MKX5R8BB226
C240, C241, C250: 27pF; C_0402_1005Metric; Tolerance +-5%; Voltage 50V; PartNumber 04025A270JAT2A
C246: 47uF; C_0805_2012Metric; Tolerance +-20%; Voltage 10V; PartNumber GRM21BR61A476ME15L
R202, R203, R204, R205, R209, R210, R211, R212: 100k; R_0402_1005Metric; PartNumber CRCW0402100KFKEDHP
R206, R207, R208, R215: 200k; R_0402_1005Metric; PartNumber ERJ-2RKF2003X
R213: 68k; R_0402_1005Metric; PartNumber RMCF0402FT68K0
R214: 12.7k; R_0402_1005Metric; PartNumber ERJ-2RKF1272X
R216: 44.2k; R_0402_1005Metric; PartNumber ERJ-2RKF4422X
U30, U31, U33: MPM3840GQV-Z; MPM3840GQV-P
U32: MPM3810AGQB-Z; MPM3810GQB

Connections:
3V8_VDD_SLVS_EC: C249.2, C251.2, R213.1, U32.5 (OUT5), U32.6 (OUT6), U32.12 (OUT_S)
+5V: C236.2, C237.2, C238.2, C239.2, C246.2, C247.2, C248.2, R202.1, R204.1, R210.1, R211.1, U30.15 (VIN), U31.15 (VIN), U32.7 (VIN), U33.15 (VIN)
CC_PL_PGOOD: R210.2, U30.14 (PG), U31.14 (PG), U32.8 (PG), U33.14 (PG)
GND: C236.1, C237.1, C238.1, C239.1, C242.1, C243.1, C244.1, C245.1, C246.1, C247.1, C248.1, C249.1, C251.1, C252.1, C253.1, R203.2, R205.2, R207.2, R209.2, R212.2, R214.2, R216.2, U30.1 (GND1), U30.2 (GND2), U30.3 (GND3), U30.17 (GND17), U30.18 (GND18), U31.1 (GND1), U31.2 (GND2), U31.3 (GND3), U31.17 (GND17), U31.18 (GND18), U32.1 (PGND1), U32.2 (PGND2), U32.11 (AGND), U33.1 (GND1), U33.2 (GND2), U33.3 (GND3), U33.17 (GND17), U33.18 (GND18)
unnamed: R213.2, R214.1, U32.10 (FB)
PL_1V2: C240.2, C242.2, C244.2, R206.1, U30.7 (OUT7), U30.8 (OUT8), U30.9 (OUT9), U30.9A (OUT9A)
PL_1V2_FB: R206.2, R207.1, U30.10 (FB)
PL_1V2_MODE: R202.2, R203.1, U30.13 (MODE)
PL_1V2_RAMP: C240.1, U30.11 (RAMP)
PL_1V2_SW: U30.4 (SW4), U30.4A (SW4A), U30.5 (SW5), U30.6 (SW6), U30.16 (SW16)
PL_1V8: C241.2, C243.2, C245.2, R208.1, U31.7 (OUT7), U31.8 (OUT8), U31.9 (OUT9), U31.9A (OUT9A)
PL_1V8_FB: R208.2, R209.1, U31.10 (FB)
PL_1V8_MODE: R204.2, R205.1, U31.13 (MODE)
PL_1V8_RAMP: C241.1, U31.11 (RAMP)
PL_1V8_SW: U31.4 (SW4), U31.4A (SW4A), U31.5 (SW5), U31.6 (SW6), U31.16 (SW16)
PL_3V3: C250.2, C252.2, C253.2, R215.1, U33.7 (OUT7), U33.8 (OUT8), U33.9 (OUT9), U33.9A (OUT9A)
PL_3V3_FB: R215.2, R216.1, U33.10 (FB)
PL_3V3_MODE: R211.2, R212.1, U33.13 (MODE)
PL_3V3_RAMP: C250.1, U33.11 (RAMP)
PL_3V3_SW: U33.4 (SW4), U33.4A (SW4A), U33.5 (SW5), U33.6 (SW6), U33.16 (SW16)
VCCOEN_PL_M2C: U30.12 (EN), U31.12 (EN), U32.9 (EN), U33.12 (EN)

Notes on the sheet:
PL 1V2
4A output for PL 1V2 for 1A for HPA bank 3A overhead for accessories
Kria PL Power
Pull Up Resistor for CC_PL_PGOOD
4A output for PL 3V3 for HDA 3V3 1A HDC 3V3 1A Raspberry Pi Cams, 1A max each
PL 3V3
4A output for PL 1V8 for 0.6A for SLVS-EC 1.8V
Page 15/18 of datasheet R1 = 200K, R2 = R1/((Vout/0.6)-1) = 100k
SLVS-EC 3V8 for FRAMOS
PL 1V8
0.6A for SLVS-EC (75/14 + 1)*0.6 = 3.814V
