ApotheoTech/Aper-Oculus/PS_Clocks.kicad_sch

## KiCad design PS_Clocks.kicad_sch (2023-12-22)

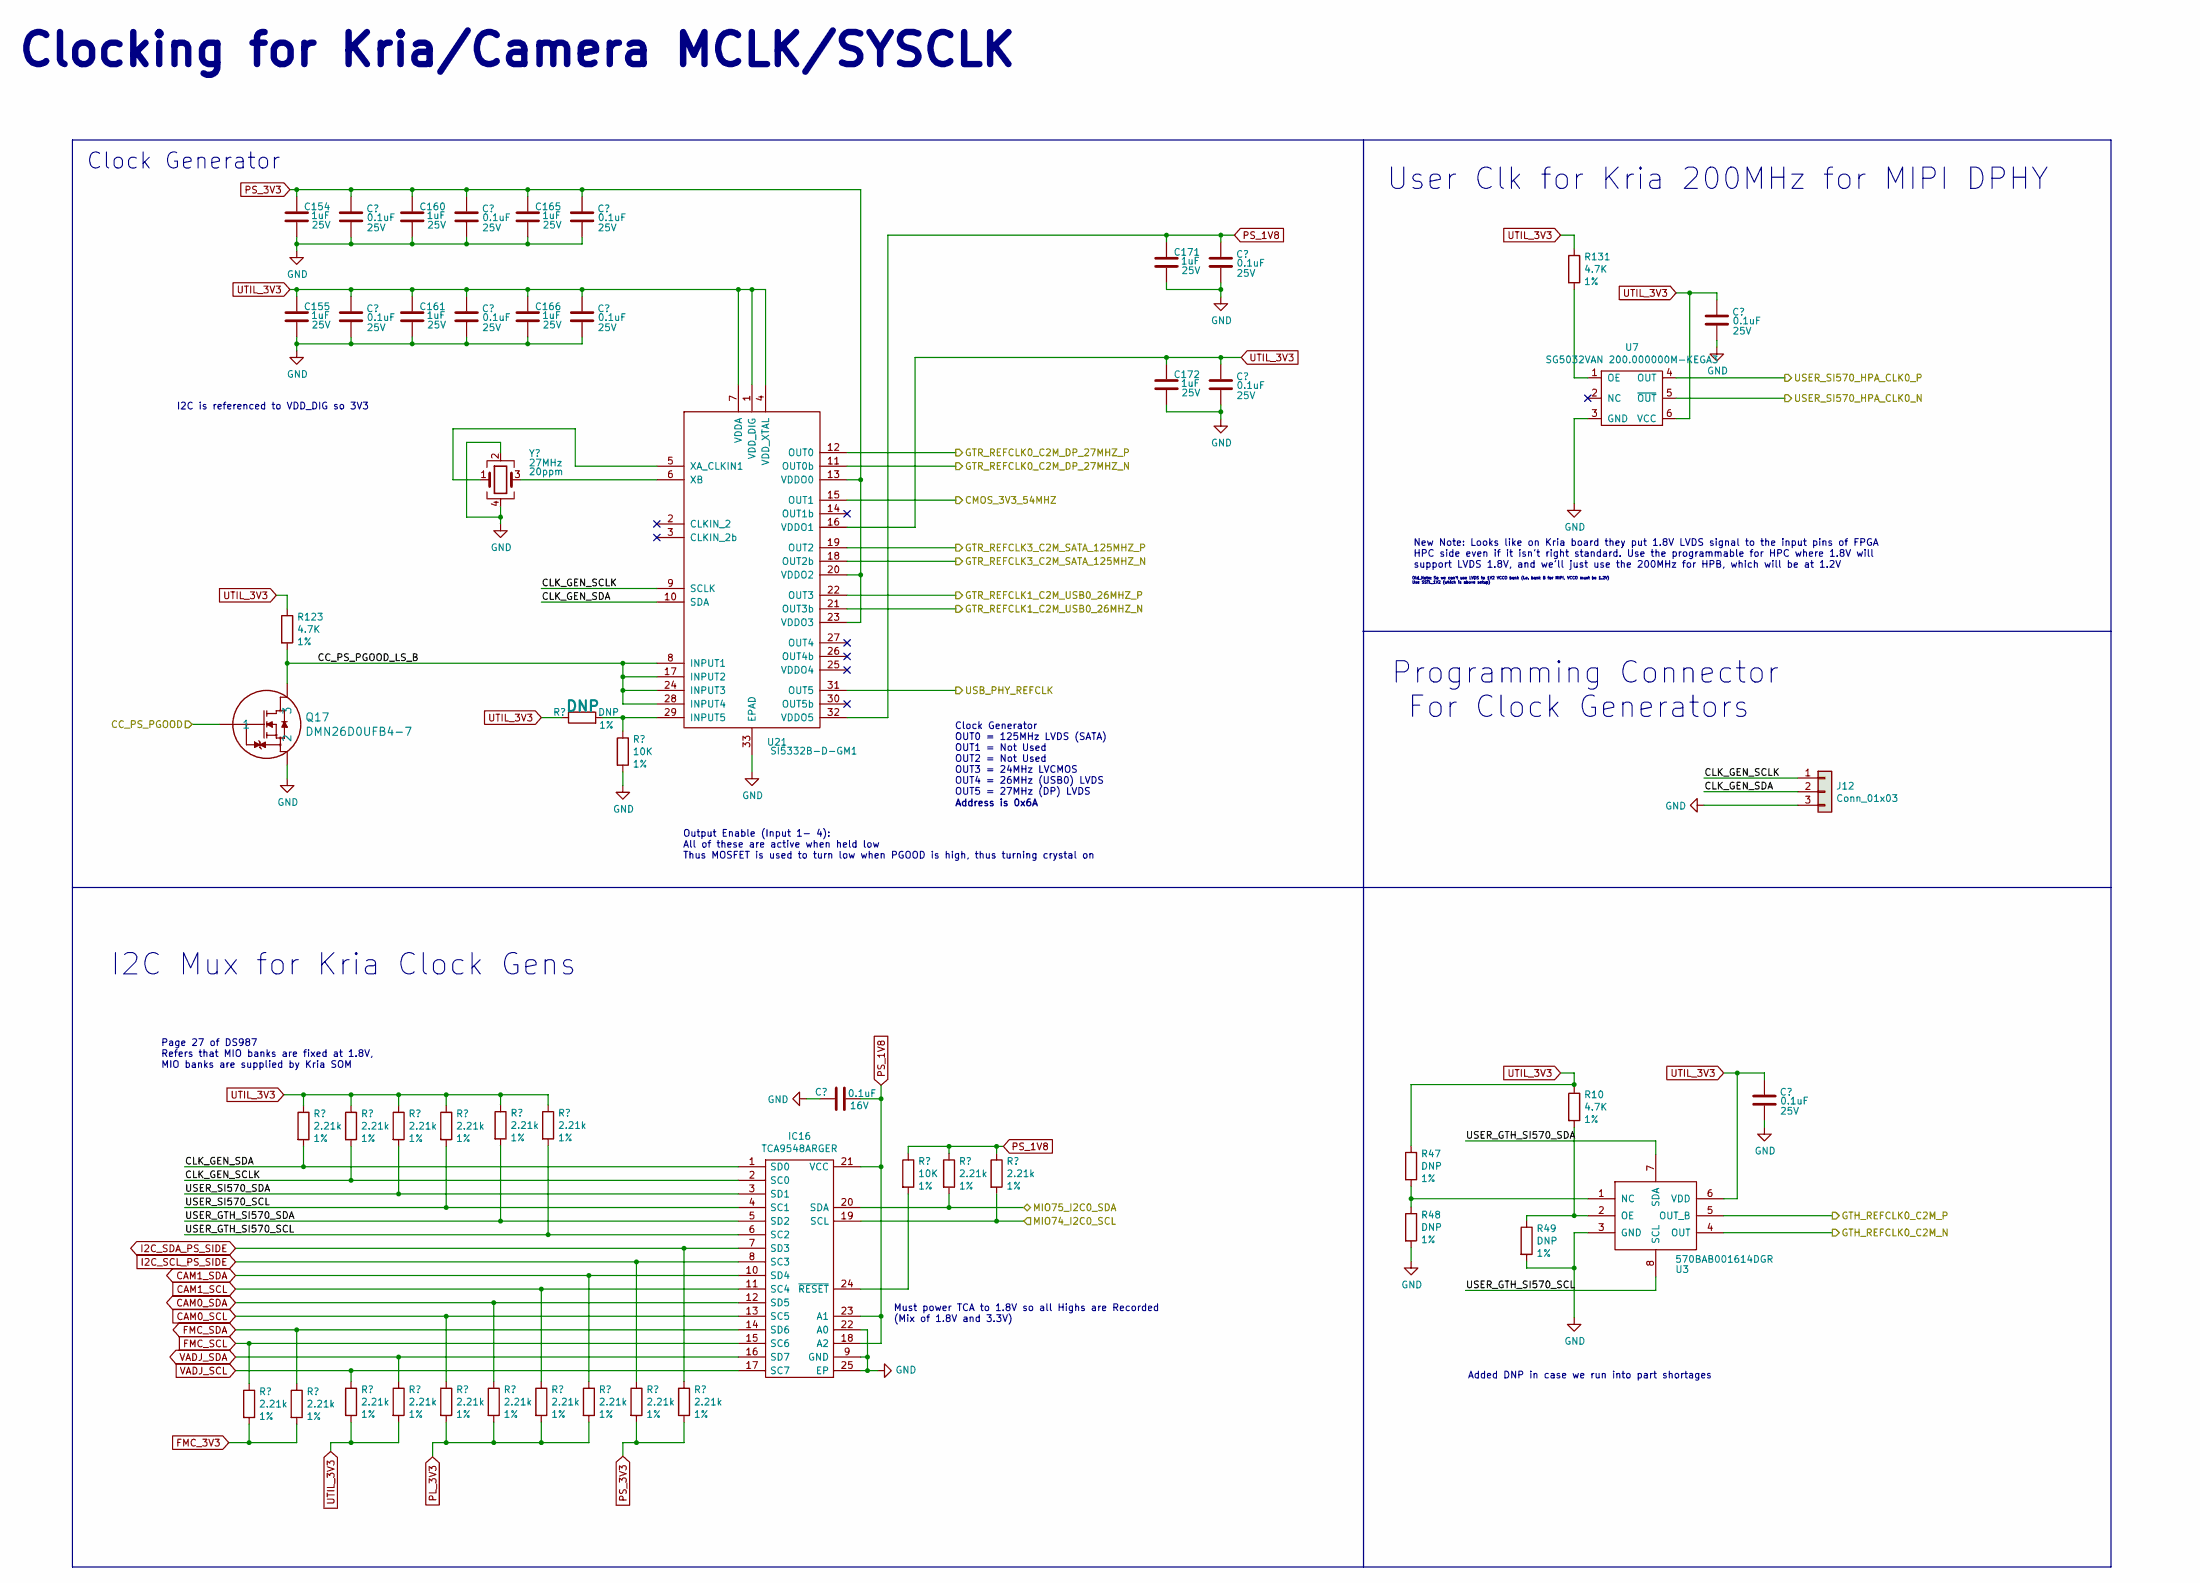
[picture p18: schematic PS_Clocks.kicad_sch]

Parts:
C6, C157, C158, C162, C163, C168, C169, C173, C174, C175: 0.1uF; C_0402_1005Metric; Tolerance +-10%; Voltage 25V; PartNumber TMK105BJ104KVHF
C154, C155, C160, C161, C165, C166, C171, C172: 1uF; C_0402_1005Metric; Tolerance +-10%; Voltage 25V; PartNumber C1005X5R1E105K050BE‎
C176: 0.1uF; C_0402_1005Metric; Tolerance +-10%; Voltage 16V; PartNumber EMK105B7104KV-F
IC16: TCA9548ARGER; Mouser Part Number 595-TCA9548ARGER
J12: Conn_01x03; PinHeader_1x03_P2.54mm_Vertical
Q17: DMN26D0UFB4-7
R7, R9, R24, R25, R133, R135, R136, R137, R138, R139, R140, R142, R144, R145, R146, R147, R149, R150: 2.21k; R_0402_1005Metric; Tolerance 1%; PartNumber ERJ-2RKF2211X
R10, R123, R131: 4.7K; R_0402_1005Metric; Tolerance 1%; PartNumber CRCW04024K70FKED
R47, R48, R49: DNP; R_0402_1005Metric; Tolerance 1%; PartNumber CRCW04024K70FKED
R129: DNP; R_0402_1005Metric; Tolerance 1%; PartNumber ERJ-2RKF1002X
R130, R148: 10K; R_0402_1005Metric; Tolerance 1%; PartNumber ERJ-2RKF1002X
U3: 570BAB001614DGR
U7: SG5032VAN 200.000000M-KEGA3; SG5032_5mm_3_2mm
U21: SI5332B-D-GM1
Y3: 27MHz; Crystal_3.2x2.5mm_12MHz; Tolerance 20ppm; PartNumber ECS-270-18-33-JEM-TR‎

Connections:
CAM0_SCL: IC16.13 (SC5), R140.1
CAM0_SDA: IC16.12 (SD5), R142.1
CAM1_SCL: IC16.11 (SC4), R144.1
CAM1_SDA: IC16.10 (SD4), R145.1
CC_PS_PGOOD: Q17.1
CC_PS_PGOOD_LS_B: Q17.3, R123.2, U21.8 (INPUT1), U21.17 (INPUT2), U21.24 (INPUT3), U21.28 (INPUT4)
CLK_GEN_SCLK: IC16.2 (SC0), J12.1, R135.2, U21.9 (SCLK)
CLK_GEN_SDA: IC16.1 (SD0), J12.2, R133.2, U21.10 (SDA)
CMOS_3V3_54MHZ: U21.15 (OUT1)
FMC_3V3: R24.2, R25.2
FMC_SCL: IC16.15 (SC6), R24.1
FMC_SDA: IC16.14 (SD6), R25.1
GND: C6.1, C154.1, C155.1, C157.1, C158.1, C160.1, C161.1, C162.1, C163.1, C165.1, C166.1, C168.1, C169.1, C171.1, C172.1, C173.1, C174.1, C175.1, C176.1, IC16.9 (GND), IC16.22 (A0), IC16.25 (EP), J12.3, Q17.2, R48.2, R49.2, R130.2, U3.3 (GND), U7.3 (GND), U21.33 (EPAD), Y3.2, Y3.4
GTH_REFCLK0_C2M_N: U3.4 (OUT)
GTH_REFCLK0_C2M_P: U3.5 (OUT_B)
GTR_REFCLK0_C2M_DP_27MHZ_N: U21.11 (OUT0b)
GTR_REFCLK0_C2M_DP_27MHZ_P: U21.12 (OUT0)
GTR_REFCLK1_C2M_USB0_26MHZ_N: U21.21 (OUT3b)
GTR_REFCLK1_C2M_USB0_26MHZ_P: U21.22 (OUT3)
GTR_REFCLK3_C2M_SATA_125MHZ_N: U21.18 (OUT2b)
GTR_REFCLK3_C2M_SATA_125MHZ_P: U21.19 (OUT2)
I2C_SCL_PS_SIDE: IC16.8 (SC3), R146.1
I2C_SDA_PS_SIDE: IC16.7 (SD3), R147.1
MIO74_I2C0_SCL: IC16.19 (SCL), R150.2
MIO75_I2C0_SDA: IC16.20 (SDA), R149.2
unnamed: IC16.24 (~RESET), R148.2
unnamed: R10.2, R49.1, U3.2 (OE)
unnamed: R47.2, R48.1, U3.1 (NC)
unnamed: R129.2, R130.1, U21.29 (INPUT5)
unnamed: R131.2, U7.1 (OE)
unnamed: U21.5 (XA_CLKIN1), Y3.1
unnamed: U21.6 (XB), Y3.3
PL_3V3: R140.2, R142.2, R144.2, R145.2
PS_1V8: C171.2, C173.2, C176.2, IC16.18 (A2), IC16.21 (VCC), IC16.23 (A1), R148.1, R149.1, R150.1, U21.32 (VDDO5)
PS_3V3: C154.2, C157.2, C160.2, C162.2, C165.2, C168.2, R146.2, R147.2, U21.13 (VDDO0), U21.20 (VDDO2), U21.23 (VDDO3)
USB_PHY_REFCLK: U21.31 (OUT5)
USER_GTH_SI570_SCL: IC16.6 (SC2), R9.2, U3.8 (SCL)
USER_GTH_SI570_SDA: IC16.5 (SD2), R7.2, U3.7 (SDA)
USER_SI570_HPA_CLK0_N: U7.5 (~OUT)
USER_SI570_HPA_CLK0_P: U7.4 (OUT)
USER_SI570_SCL: IC16.4 (SC1), R139.2
USER_SI570_SDA: IC16.3 (SD1), R137.2
UTIL_3V3: C6.2, C155.2, C158.2, C161.2, C163.2, C166.2, C169.2, C172.2, C174.2, C175.2, R7.1, R9.1, R10.1, R47.1, R123.1, R129.1, R131.1, R133.1, R135.1, R136.2, R137.1, R138.2, R139.1, U3.6 (VDD), U7.6 (VCC), U21.1 (VDD_DIG), U21.4 (VDD_XTAL), U21.7 (VDDA), U21.16 (VDDO1)
VADJ_SCL: IC16.17 (SC7), R136.1
VADJ_SDA: IC16.16 (SD7), R138.1

Notes on the sheet:
Clock Generator
Old_Note: So we can't use LVDS to 1V2 VCCO bank (i.e. bank B for MIPI, VCCO must be 1.2V) Use SSTL_1V2 (which is above setup)
Programming Connector For Clock Generators
I2C is referenced to VDD_DIG so 3V3
Output Enable (Input 1- 4): All of these are active when held low Thus MOSFET is used to turn low when PGOOD is high, thus turning crystal on
I2C Mux for Kria Clock Gens
Address is 0x6A
New Note: Looks like on Kria board they put 1.8V LVDS signal to the input pins of FPGA HPC side even if it isn't right standard. Use the programmable for HPC where 1.8V will support LVDS 1.8V, and we'll just use the 200MHz for HPB, which will be at 1.2V
Must power TCA to 1.8V so all Highs are Recorded (Mix of 1.8V and 3.3V)
Page 27 of DS987 Refers that MIO banks are fixed at 1.8V, MIO banks are supplied by Kria SOM
Clocking for Kria/Camera MCLK/SYSCLK
Added DNP in case we run into part shortages
User Clk for Kria 200MHz for MIPI DPHY
Clock Generator OUT0 = 125MHz LVDS (SATA) OUT1 = Not Used OUT2 = Not Used OUT3 = 24MHz LVCMOS OUT4 = 26MHz (USB0) LVDS OUT5 = 27MHz (DP) LVDS
