ApotheoTech/Aper-Oculus/PS_Power.kicad_sch

## KiCad design PS_Power.kicad_sch (2023-12-22)

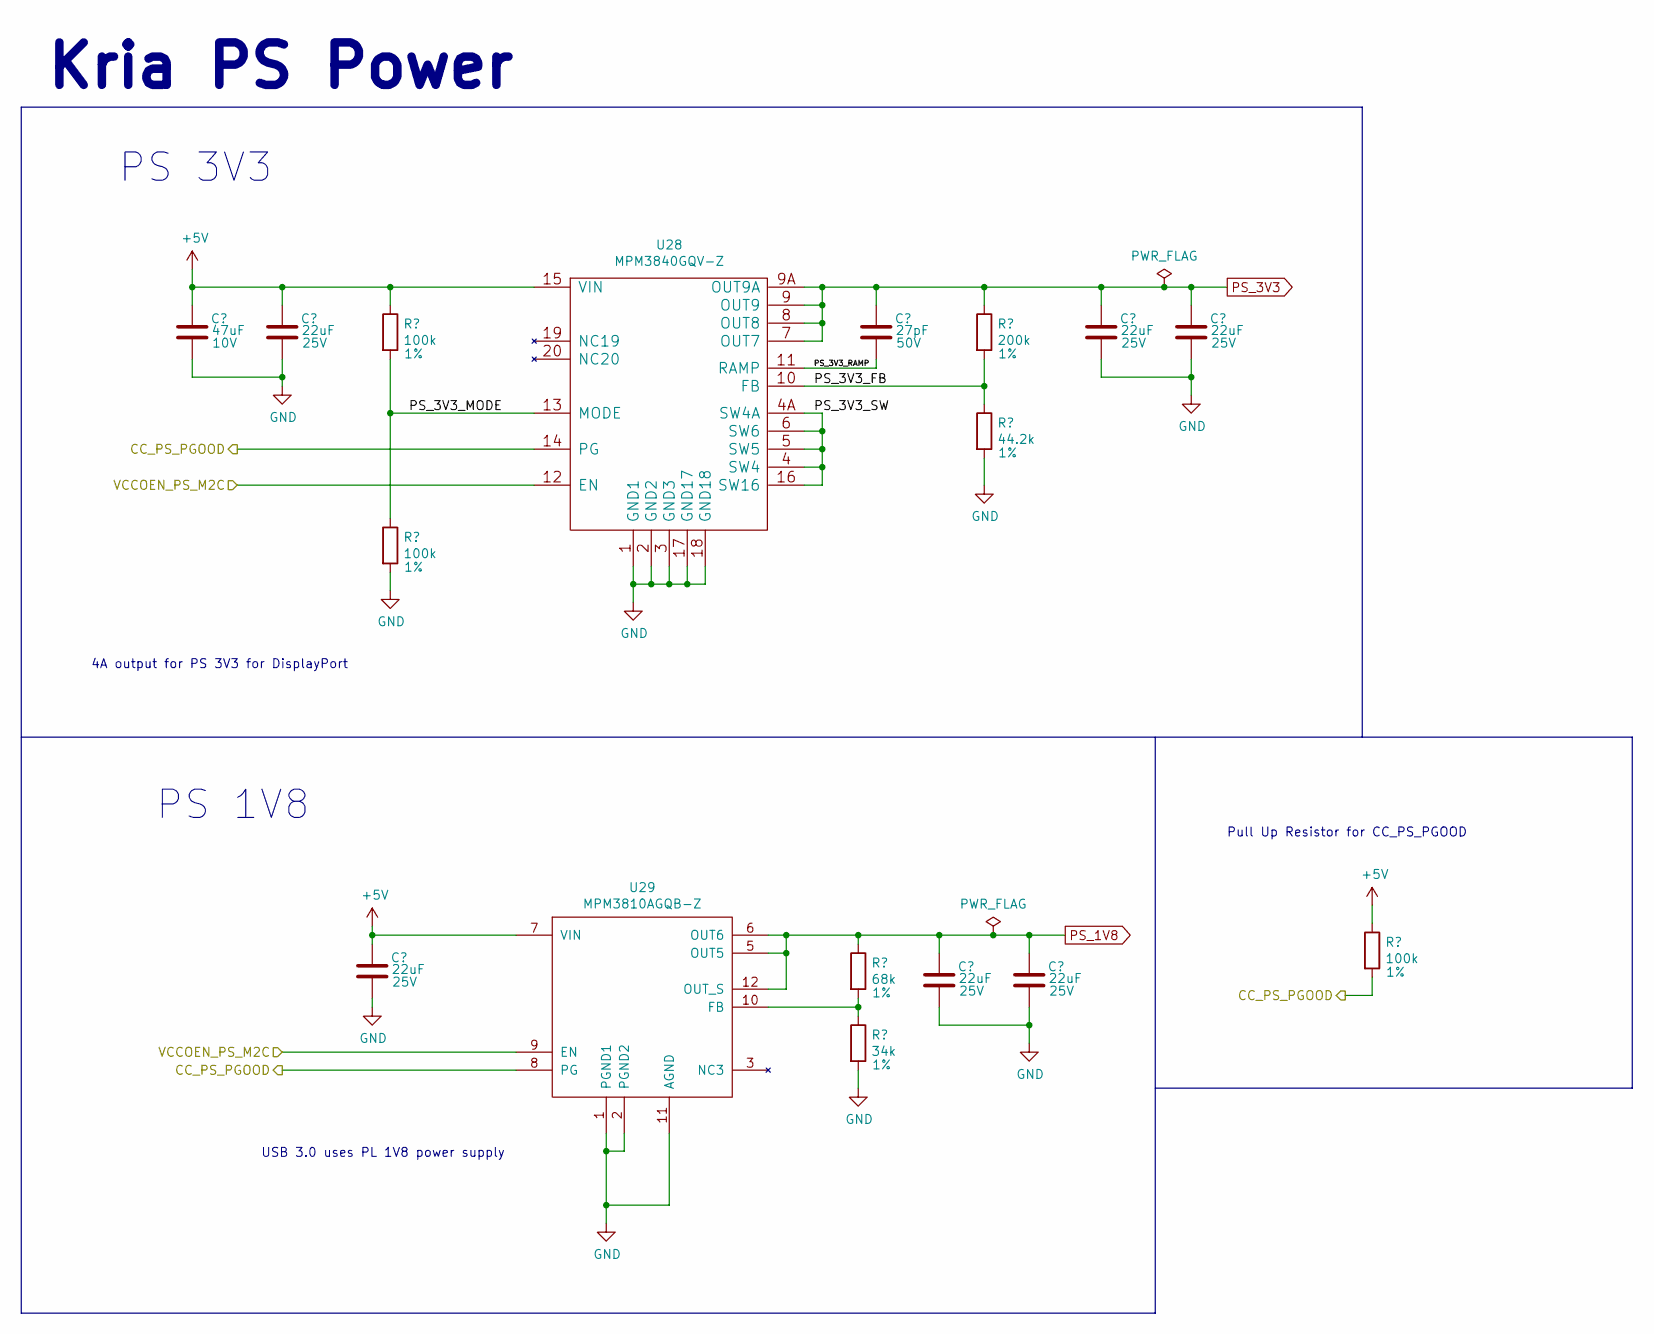
[picture p19: schematic PS_Power.kicad_sch]

Parts:
C228: 47uF; C_0805_2012Metric; Tolerance +-20%; Voltage 10V; PartNumber GRM21BR61A476ME15L
C229, C230, C232, C233, C234, C235: 22uF; C_0805_2012Metric; Tolerance +-20%; Voltage 25V; PartNumber CC0805MKX5R8BB226
C231: 27pF; C_0402_1005Metric; Tolerance +-5%; Voltage 50V; PartNumber 04025A270JAT2A
R195, R196, R201: 100k; R_0402_1005Metric; PartNumber CRCW0402100KFKEDHP
R197: 68k; R_0402_1005Metric; PartNumber RMCF0402FT68K0
R198: 34k; R_0402_1005Metric; PartNumber ERJ-2RKF3402X
R199: 200k; R_0402_1005Metric; PartNumber ERJ-2RKF2003X
R200: 44.2k; R_0402_1005Metric; PartNumber ERJ-2RKF4422X
U28: MPM3840GQV-Z; MPM3840GQV-P
U29: MPM3810AGQB-Z; MPM3810GQB

Connections:
+5V: C228.2, C229.2, C230.2, R195.1, R201.1, U28.15 (VIN), U29.7 (VIN)
CC_PS_PGOOD: R201.2, U28.14 (PG), U29.8 (PG)
GND: C228.1, C229.1, C230.1, C232.1, C233.1, C234.1, C235.1, R196.2, R198.2, R200.2, U28.1 (GND1), U28.2 (GND2), U28.3 (GND3), U28.17 (GND17), U28.18 (GND18), U29.1 (PGND1), U29.2 (PGND2), U29.11 (AGND)
unnamed: R197.2, R198.1, U29.10 (FB)
PS_1V8: C232.2, C234.2, R197.1, U29.5 (OUT5), U29.6 (OUT6), U29.12 (OUT_S)
PS_3V3: C231.2, C233.2, C235.2, R199.1, U28.7 (OUT7), U28.8 (OUT8), U28.9 (OUT9), U28.9A (OUT9A)
PS_3V3_FB: R199.2, R200.1, U28.10 (FB)
PS_3V3_MODE: R195.2, R196.1, U28.13 (MODE)
PS_3V3_RAMP: C231.1, U28.11 (RAMP)
PS_3V3_SW: U28.4 (SW4), U28.4A (SW4A), U28.5 (SW5), U28.6 (SW6), U28.16 (SW16)
VCCOEN_PS_M2C: U28.12 (EN), U29.9 (EN)

Notes on the sheet:
Kria PS Power
4A output for PS 3V3 for DisplayPort
PS 3V3
PS 1V8
Pull Up Resistor for CC_PS_PGOOD
USB 3.0 uses PL 1V8 power supply
