ApotheoTech/Aper-Oculus/Power_Kria.kicad_sch

## KiCad design Power_Kria.kicad_sch (2023-12-22)

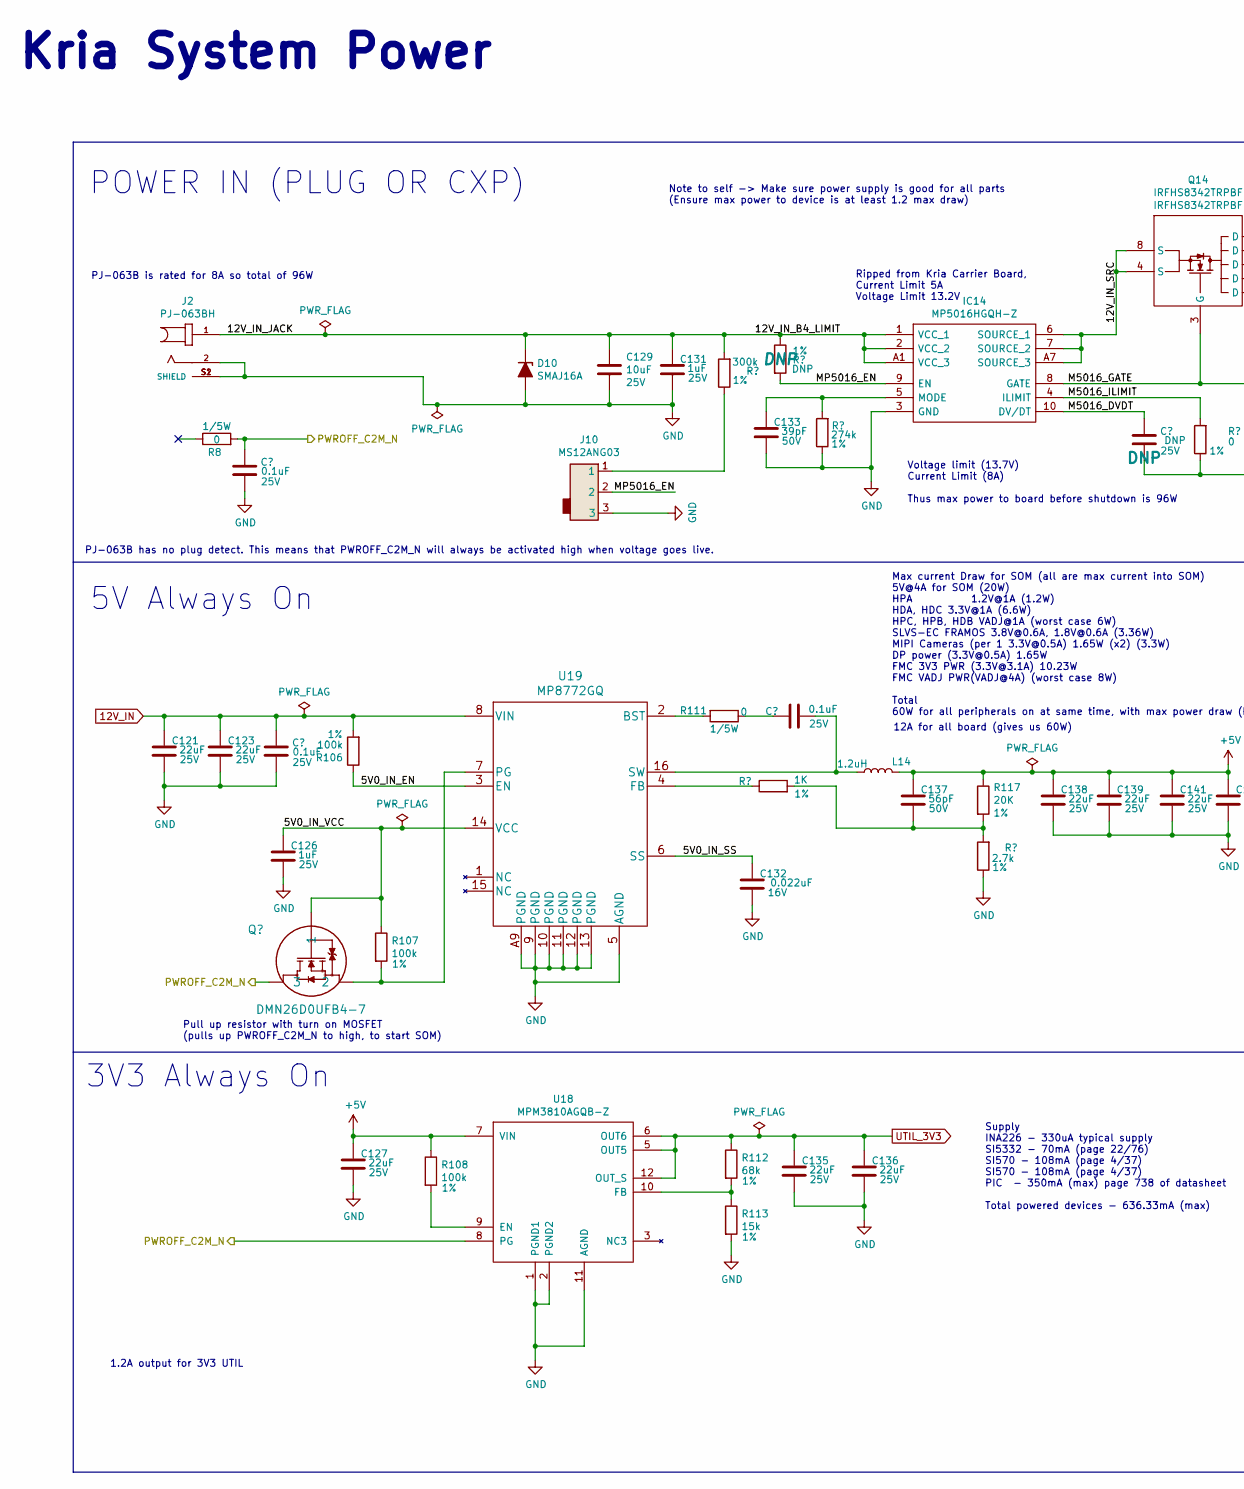
[picture p20: schematic Power_Kria.kicad_sch, part in row 1, column 1]

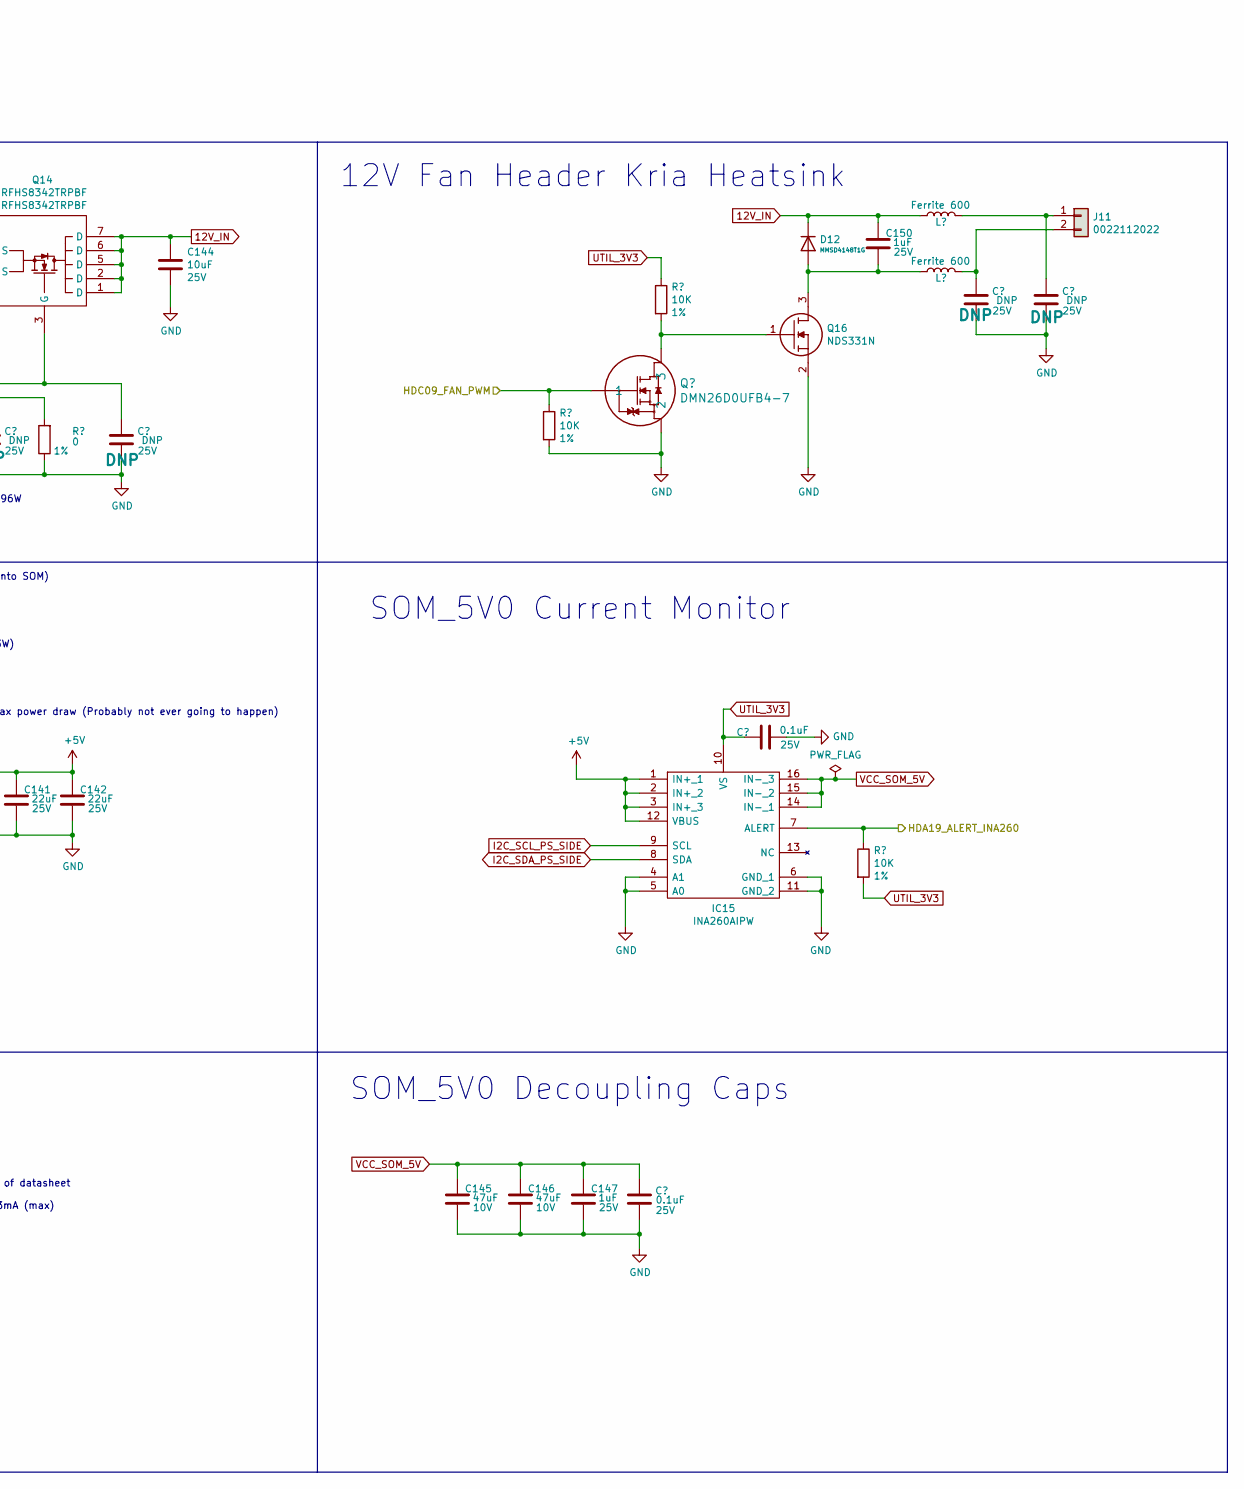
[picture p21: schematic Power_Kria.kicad_sch, part in row 1, column 2]

Parts:
C121, C123, C127, C135, C136, C138, C139, C141, C142: 22uF; C_0805_2012Metric; Tolerance +-20%; Voltage 25V; PartNumber CC0805MKX5R8BB226
C124, C125, C134, C148, C149: 0.1uF; C_0402_1005Metric; Tolerance +-10%; Voltage 25V; PartNumber TMK105BJ104KVHF
C126, C131, C147, C150: 1uF; C_0402_1005Metric; Tolerance +-10%; Voltage 25V; PartNumber C1005X5R1E105K050BE‎
C129, C144: 10uF; C_1206_3216Metric; Tolerance +-10%; Voltage 25V; PartNumber CL31B106KAHNFNE
C132: 0.022uF; C_0402_1005Metric; Tolerance +-10%; Voltage 16V; PartNumber EMK105B7223KV-F
C133: 39pF; C_0402_1005Metric; Tolerance +-5%; Voltage 50V; PartNumber 04025A390JAT2A
C137: 56pF; C_0402_1005Metric; Tolerance +-5%; Voltage 50V; PartNumber 04025A560JAT2A
C140, C143, C151, C152: DNP; C_0402_1005Metric; Tolerance +-10%; Voltage 25V; PartNumber TMK105BJ104KVHF
C145, C146: 47uF; C_0805_2012Metric; Tolerance +-20%; Voltage 10V; PartNumber GRM21BR61A476ME15L
D10: SMAJ16A; D_SMA; PartNumber SMAJ16A
D12: MMSD4148T1G; D_SOD-123; PartNumber MMSD4148T1G
IC14: MP5016HGQH-Z; MP5016HGQHZ; Mouser Part Number 946-MP5016HGQH-Z
IC15: INA260AIPW; Mouser Part Number 595-INA260AIPW
J2: PJ-063BH; CUI_PJ-063BH; PARTREV 1.02
J10: MS12ANG03; PartNumber MS12ANG03
J11: 0022112022‎; 0022112022; PartNumber 0022112022‎
L14: 1.2uH; XAL5030-122ME; PartNumber XEL5030-122ME
L15, L16: Ferrite 600; L_0603_1608Metric; PartNumber BLM18KG601SN1D
Q13, Q15: DMN26D0UFB4-7
Q14: IRFHS8342TRPBF; PartNumber IRFHS8342TRPBF
Q16: NDS331N; Mouser Part Number 512-NDS331N
R8, R111: 0; R_0402_1005Metric; PartNumber CRCW04020000Z0EDHP
R37: 300k; R_0402_1005Metric; Tolerance 1%; PartNumber ERJ-2RKF3003X
R106, R107, R108: 100k; R_0402_1005Metric; PartNumber CRCW0402100KFKEDHP
R112: 68k; R_0402_1005Metric; PartNumber RMCF0402FT68K0
R113: 15k; R_0402_1005Metric; PartNumber ERJ-2RKF1502X
R114: DNP; R_0402_1005Metric; Tolerance 1%; PartNumber ERJ-2RKF3003X
R115: 1K; R_0402_1005Metric; Tolerance 1%; PartNumber ERJ-2RKF1001X‎
R116: 274k; R_0402_1005Metric; Tolerance 1%; PartNumber ERJ-2RKF2743X
R117: 20K; R_0402_1005Metric; Tolerance 1%; PartNumber ERJ-2RKF2002X
R118: 2.7k; R_0402_1005Metric; Tolerance 1%; PartNumber ERJ-2RKF2701X
R119: 0; R_0402_1005Metric; Tolerance 1%; PartNumber CRCW04020000Z0EDHP
R120, R121, R122: 10K; R_0402_1005Metric; Tolerance 1%; PartNumber ERJ-2RKF1002X
U18: MPM3810AGQB-Z; MPM3810GQB
U19: MP8772GQ

Connections:
5V0_IN_EN: R106.1, U19.3 (EN)
5V0_IN_SS: C132.2, U19.6 (SS)
5V0_IN_VCC: C126.2, Q13.1, R107.1, U19.14 (VCC)
12V_IN: C121.2, C123.2, C125.2, C144.1, C150.2, D12.1 (K), L15.1, Q14.1 (D), Q14.2 (D), Q14.5 (D), Q14.6 (D), Q14.7 (D), R106.2, U19.8 (VIN)
12V_IN_B4_LIMIT: C129.1, C131.2, D10.1 (K), IC14.1 (VCC_1), IC14.2 (VCC_2), IC14.A1 (VCC_3), J2.1, R37.2, R114.1
12V_IN_SRC: IC14.6 (SOURCE_1), IC14.7 (SOURCE_2), IC14.A7 (SOURCE_3), Q14.4 (S), Q14.8 (S)
+5V: C127.2, C137.2, C138.2, C139.2, C141.2, C142.2, IC15.1 (IN+_1), IC15.2 (IN+_2), IC15.3 (IN+_3), IC15.12 (VBUS), L14.2, R108.1, R117.1, U18.7 (VIN)
GND: C121.1, C123.1, C124.1, C125.1, C126.1, C127.1, C129.2, C131.1, C132.1, C133.1, C135.1, C136.1, C138.1, C139.1, C140.1, C141.1, C142.1, C143.1, C144.2, C145.1, C146.1, C147.1, C148.1, C149.1, C151.1, C152.1, D10.2 (A), IC14.3 (GND), IC15.4 (A1), IC15.5 (A0), IC15.6 (GND_1), IC15.11 (GND_2), J2.2, J2.S1 (SHIELD), J2.S2 (SHIELD), J10.3, Q15.2, Q16.2, R113.2, R116.1, R118.1, R119.1, R120.2, U18.1 (PGND1), U18.2 (PGND2), U18.11 (AGND), U19.5 (AGND), U19.9 (PGND), U19.10 (PGND), U19.11 (PGND), U19.12 (PGND), U19.13 (PGND), U19.A9 (PGND)
HDA19_ALERT_INA260: IC15.7 (ALERT), R122.1
HDC09_FAN_PWM: Q15.1, R120.1
I2C_SCL_PS_SIDE: IC15.9 (SCL)
I2C_SDA_PS_SIDE: IC15.8 (SDA)
M5016_DVDT: C140.2, IC14.10 (DV/DT)
M5016_GATE: C143.2, IC14.8 (GATE), Q14.3 (G)
M5016_ILIMIT: IC14.4 (ILIMIT), R119.2
MP5016_EN: IC14.9 (EN), J10.2, R114.2
unnamed: C133.2, IC14.5 (MODE), R116.2
unnamed: C134.1, L14.1, U19.16 (SW)
unnamed: C134.2, R111.1
unnamed: C137.1, R115.2, R117.2, R118.2
unnamed: C150.1, D12.2 (A), L16.1, Q16.3
unnamed: C151.2, J11.2, L16.2
unnamed: C152.2, J11.1, L15.2
unnamed: J10.1, R37.1
unnamed: Q13.2, R107.2, U19.7 (PG)
unnamed: Q15.3, Q16.1, R121.2
unnamed: R108.2, U18.9 (EN)
unnamed: R111.2, U19.2 (BST)
unnamed: R112.2, R113.1, U18.10 (FB)
unnamed: R115.1, U19.4 (FB)
PWROFF_C2M_N: C124.2, Q13.3, R8.2, U18.8 (PG)
UTIL_3V3: C135.2, C136.2, C149.2, IC15.10 (VS), R112.1, R121.1, R122.2, U18.5 (OUT5), U18.6 (OUT6), U18.12 (OUT_S)
VCC_SOM_5V: C145.2, C146.2, C147.2, C148.2, IC15.14 (IN-_1), IC15.15 (IN-_2), IC15.16 (IN-_3)

Notes on the sheet:
3V3 Always On
Supply INA226 - 330uA typical supply SI5332 - 70mA (page 22/76) SI570 - 108mA (page 4/37) SI570 - 108mA (page 4/37) PIC - 350mA (max) page 738 of datasheet Total powered devices - 636.33mA (max)
PJ-063B has no plug detect. This means that PWROFF_C2M_N will always be activated high when voltage goes live.
12A for all board (gives us 60W)
Kria System Power
SOM_5V0 Current Monitor
Ripped from Kria Carrier Board, Current Limit 5A Voltage Limit 13.2V
Note to self -> Make sure power supply is good for all parts (Ensure max power to device is at least 1.2 max draw)
SOM_5V0 Decoupling Caps
POWER IN (PLUG OR CXP)
1.2A output for 3V3 UTIL
Pull up resistor with turn on MOSFET (pulls up PWROFF_C2M_N to high, to start SOM)
PJ-063B is rated for 8A so total of 96W
Voltage limit (13.7V) Current Limit (8A) Thus max power to board before shutdown is 96W
5V Always On
12V Fan Header Kria Heatsink
Max current Draw for SOM (all are max current into SOM) 5V@4A for SOM (20W) HPA 1.2V@1A (1.2W) HDA, HDC 3.3V@1A (6.6W) HPC, HPB, HDB VADJ@1A (worst case 6W) SLVS-EC FRAMOS 3.8V@0.6A, 1.8V@0.6A (3.36W) MIPI Cameras (per 1 3.3V@0.5A) 1.65W (x2) (3.3W) DP power (3.3V@0.5A) 1.65W FMC 3V3 PWR (3.3V@3.1A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
