ApotheoTech/Aper-Oculus/SATA.kicad_sch

## KiCad design SATA.kicad_sch (2023-12-22)

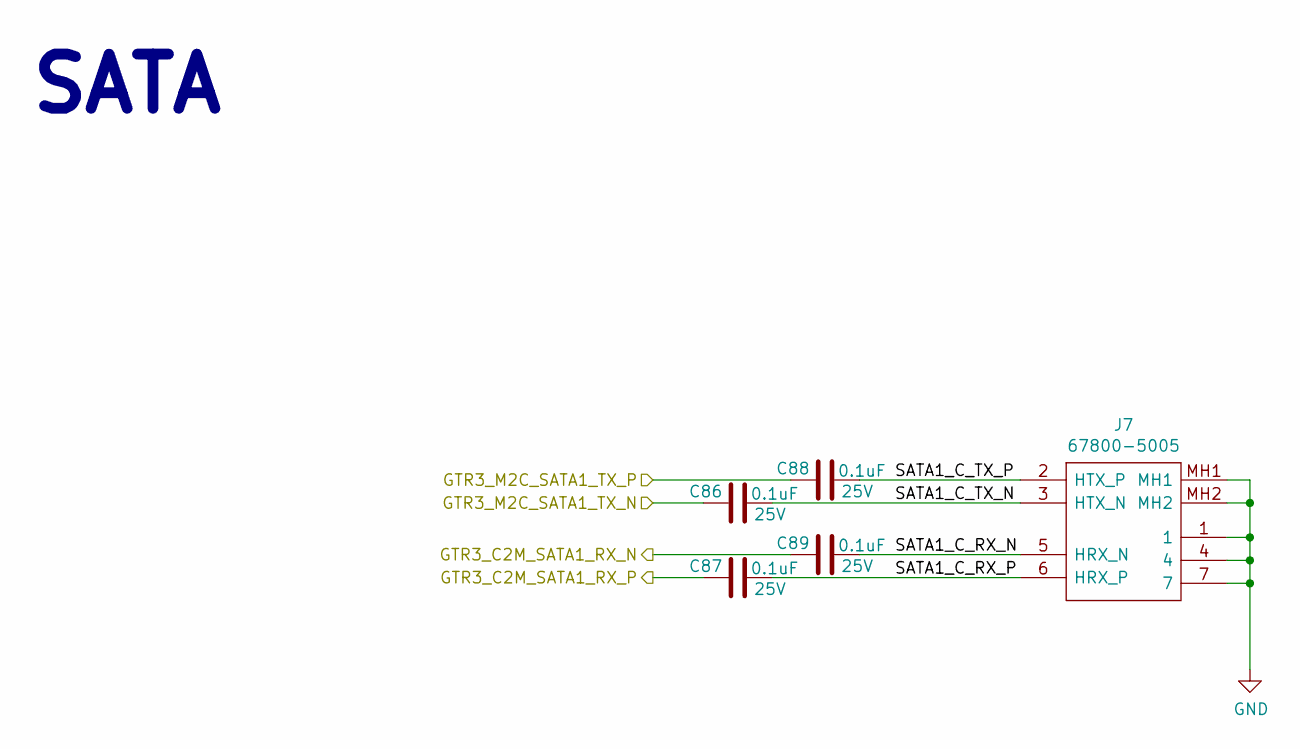
[picture p22: schematic SATA.kicad_sch]

Parts:
C86, C87, C88, C89: 0.1uF; C_0402_1005Metric; Tolerance +-10%; Voltage 25V; PartNumber TMK105BJ104KVHF
J7: 67800-5005; 678005005; Mouser Part Number 538-67800-5005

Connections:
GND: J7.1, J7.4, J7.7, J7.MH1, J7.MH2
GTR3_C2M_SATA1_RX_N: C89.1
GTR3_C2M_SATA1_RX_P: C87.1
GTR3_M2C_SATA1_TX_N: C86.1
GTR3_M2C_SATA1_TX_P: C88.1
SATA1_C_RX_N: C89.2, J7.5 (HRX_N)
SATA1_C_RX_P: C87.2, J7.6 (HRX_P)
SATA1_C_TX_N: C86.2, J7.3 (HTX_N)
SATA1_C_TX_P: C88.2, J7.2 (HTX_P)

Notes on the sheet:
SATA
