ApotheoTech/Aper-Oculus/SLVS-EC_FRAMOS.kicad_sch

## KiCad design SLVS-EC_FRAMOS.kicad_sch (2023-12-22)

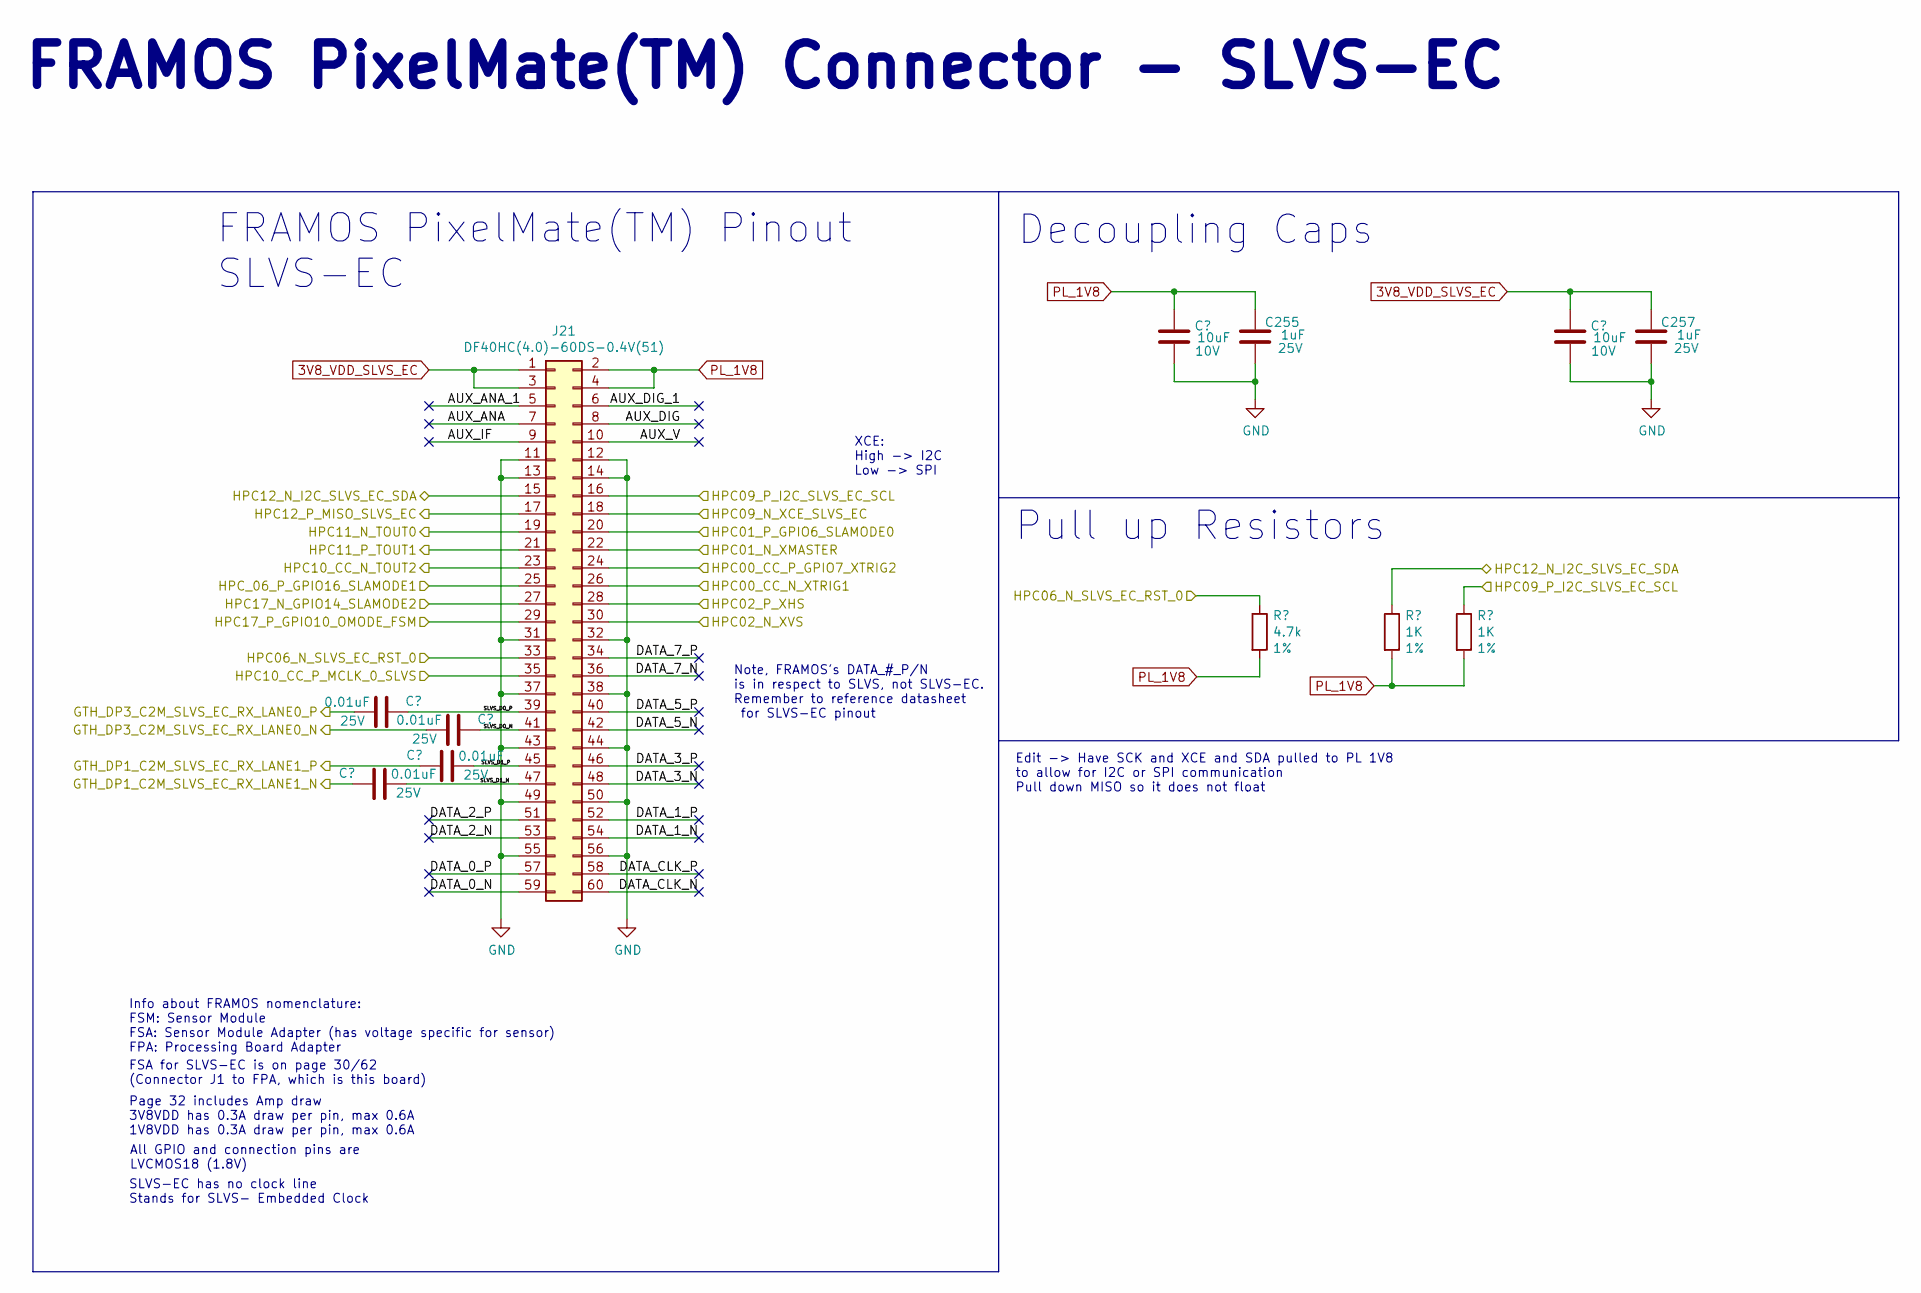
[picture p23: schematic SLVS-EC_FRAMOS.kicad_sch]

Parts:
C254, C256: 10uF; C_0402_1005Metric; Tolerance +-20%; Voltage 10V; PartNumber CL05A106MP5NUNC
C255, C257: 1uF; C_0402_1005Metric; Tolerance +-10%; Voltage 25V; PartNumber C1005X5R1E105K050BE
C259, C260, C261, C262: 0.01uF; C_0402_1005Metric; Tolerance +-10%; Voltage 25V; PartNumber 04023D103KAT2A
J21: DF40HC(4.0)-60DS-0.4V(51); DF40HC4060DS04V51
R45, R46: 1K; R_0402_1005Metric; Tolerance 1%; PartNumber ERJ-2RKF1001X‎
R217: 4.7k; R_0402_1005Metric; Tolerance 1%; PartNumber CRCW04024K70FKED

Connections:
3V8_VDD_SLVS_EC: C256.2, C257.2, J21.1, J21.3
AUX_ANA: J21.7
AUX_ANA_1: J21.5
AUX_DIG: J21.8
AUX_DIG_1: J21.6
AUX_IF: J21.9
AUX_V: J21.10
DATA_0_N: J21.59
DATA_0_P: J21.57
DATA_1_N: J21.54
DATA_1_P: J21.52
DATA_2_N: J21.53
DATA_2_P: J21.51
DATA_3_N: J21.48
DATA_3_P: J21.46
DATA_5_N: J21.42
DATA_5_P: J21.40
DATA_7_N: J21.36
DATA_7_P: J21.34
DATA_CLK_N: J21.60
DATA_CLK_P: J21.58
GND: C254.1, C255.1, C256.1, C257.1, J21.11, J21.12, J21.13, J21.14, J21.31, J21.32, J21.37, J21.38, J21.43, J21.44, J21.49, J21.50, J21.55, J21.56
GTH_DP1_C2M_SLVS_EC_RX_LANE1_N: C259.2
GTH_DP1_C2M_SLVS_EC_RX_LANE1_P: C260.2
GTH_DP3_C2M_SLVS_EC_RX_LANE0_N: C261.1
GTH_DP3_C2M_SLVS_EC_RX_LANE0_P: C262.1
HPC00_CC_N_XTRIG1: J21.26
HPC00_CC_P_GPIO7_XTRIG2: J21.24
HPC01_N_XMASTER: J21.22
HPC01_P_GPIO6_SLAMODE0: J21.20
HPC02_N_XVS: J21.30
HPC02_P_XHS: J21.28
HPC06_N_SLVS_EC_RST_0: J21.33, R217.1
HPC09_N_XCE_SLVS_EC: J21.18
HPC09_P_I2C_SLVS_EC_SCL: J21.16, R46.1
HPC10_CC_N_TOUT2: J21.23
HPC10_CC_P_MCLK_0_SLVS: J21.35
HPC11_N_TOUT0: J21.19
HPC11_P_TOUT1: J21.21
HPC12_N_I2C_SLVS_EC_SDA: J21.15, R45.1
HPC12_P_MISO_SLVS_EC: J21.17
HPC17_N_GPIO14_SLAMODE2: J21.27
HPC17_P_GPIO10_OMODE_FSM: J21.29
HPC_06_P_GPIO16_SLAMODE1: J21.25
PL_1V8: C254.2, C255.2, J21.2, J21.4, R45.2, R46.2, R217.2
SLVS_D0_N: C261.2, J21.41
SLVS_D0_P: C262.2, J21.39
SLVS_D1_N: C259.1, J21.47
SLVS_D1_P: C260.1, J21.45

Notes on the sheet:
FRAMOS PixelMate(TM) Pinout SLVS-EC
Note, FRAMOS's DATA_#_P/N is in respect to SLVS, not SLVS-EC. Remember to reference datasheet for SLVS-EC pinout
Decoupling Caps
Info about FRAMOS nomenclature: FSM: Sensor Module FSA: Sensor Module Adapter (has voltage specific for sensor) FPA: Processing Board Adapter
XCE: High -> I2C Low -> SPI
All GPIO and connection pins are LVCMOS18 (1.8V)
SLVS-EC has no clock line Stands for SLVS- Embedded Clock
Page 32 includes Amp draw 3V8VDD has 0.3A draw per pin, max 0.6A 1V8VDD has 0.3A draw per pin, max 0.6A
Edit -> Have SCK and XCE and SDA pulled to PL 1V8 to allow for I2C or SPI communication Pull down MISO so it does not float
FSA for SLVS-EC is on page 30/62 (Connector J1 to FPA, which is this board)
Pull up Resistors
FRAMOS PixelMate(TM) Connector - SLVS-EC
