ApotheoTech/Aper-Oculus/SOM240_1.kicad_sch

## KiCad design SOM240_1.kicad_sch (2023-12-22)

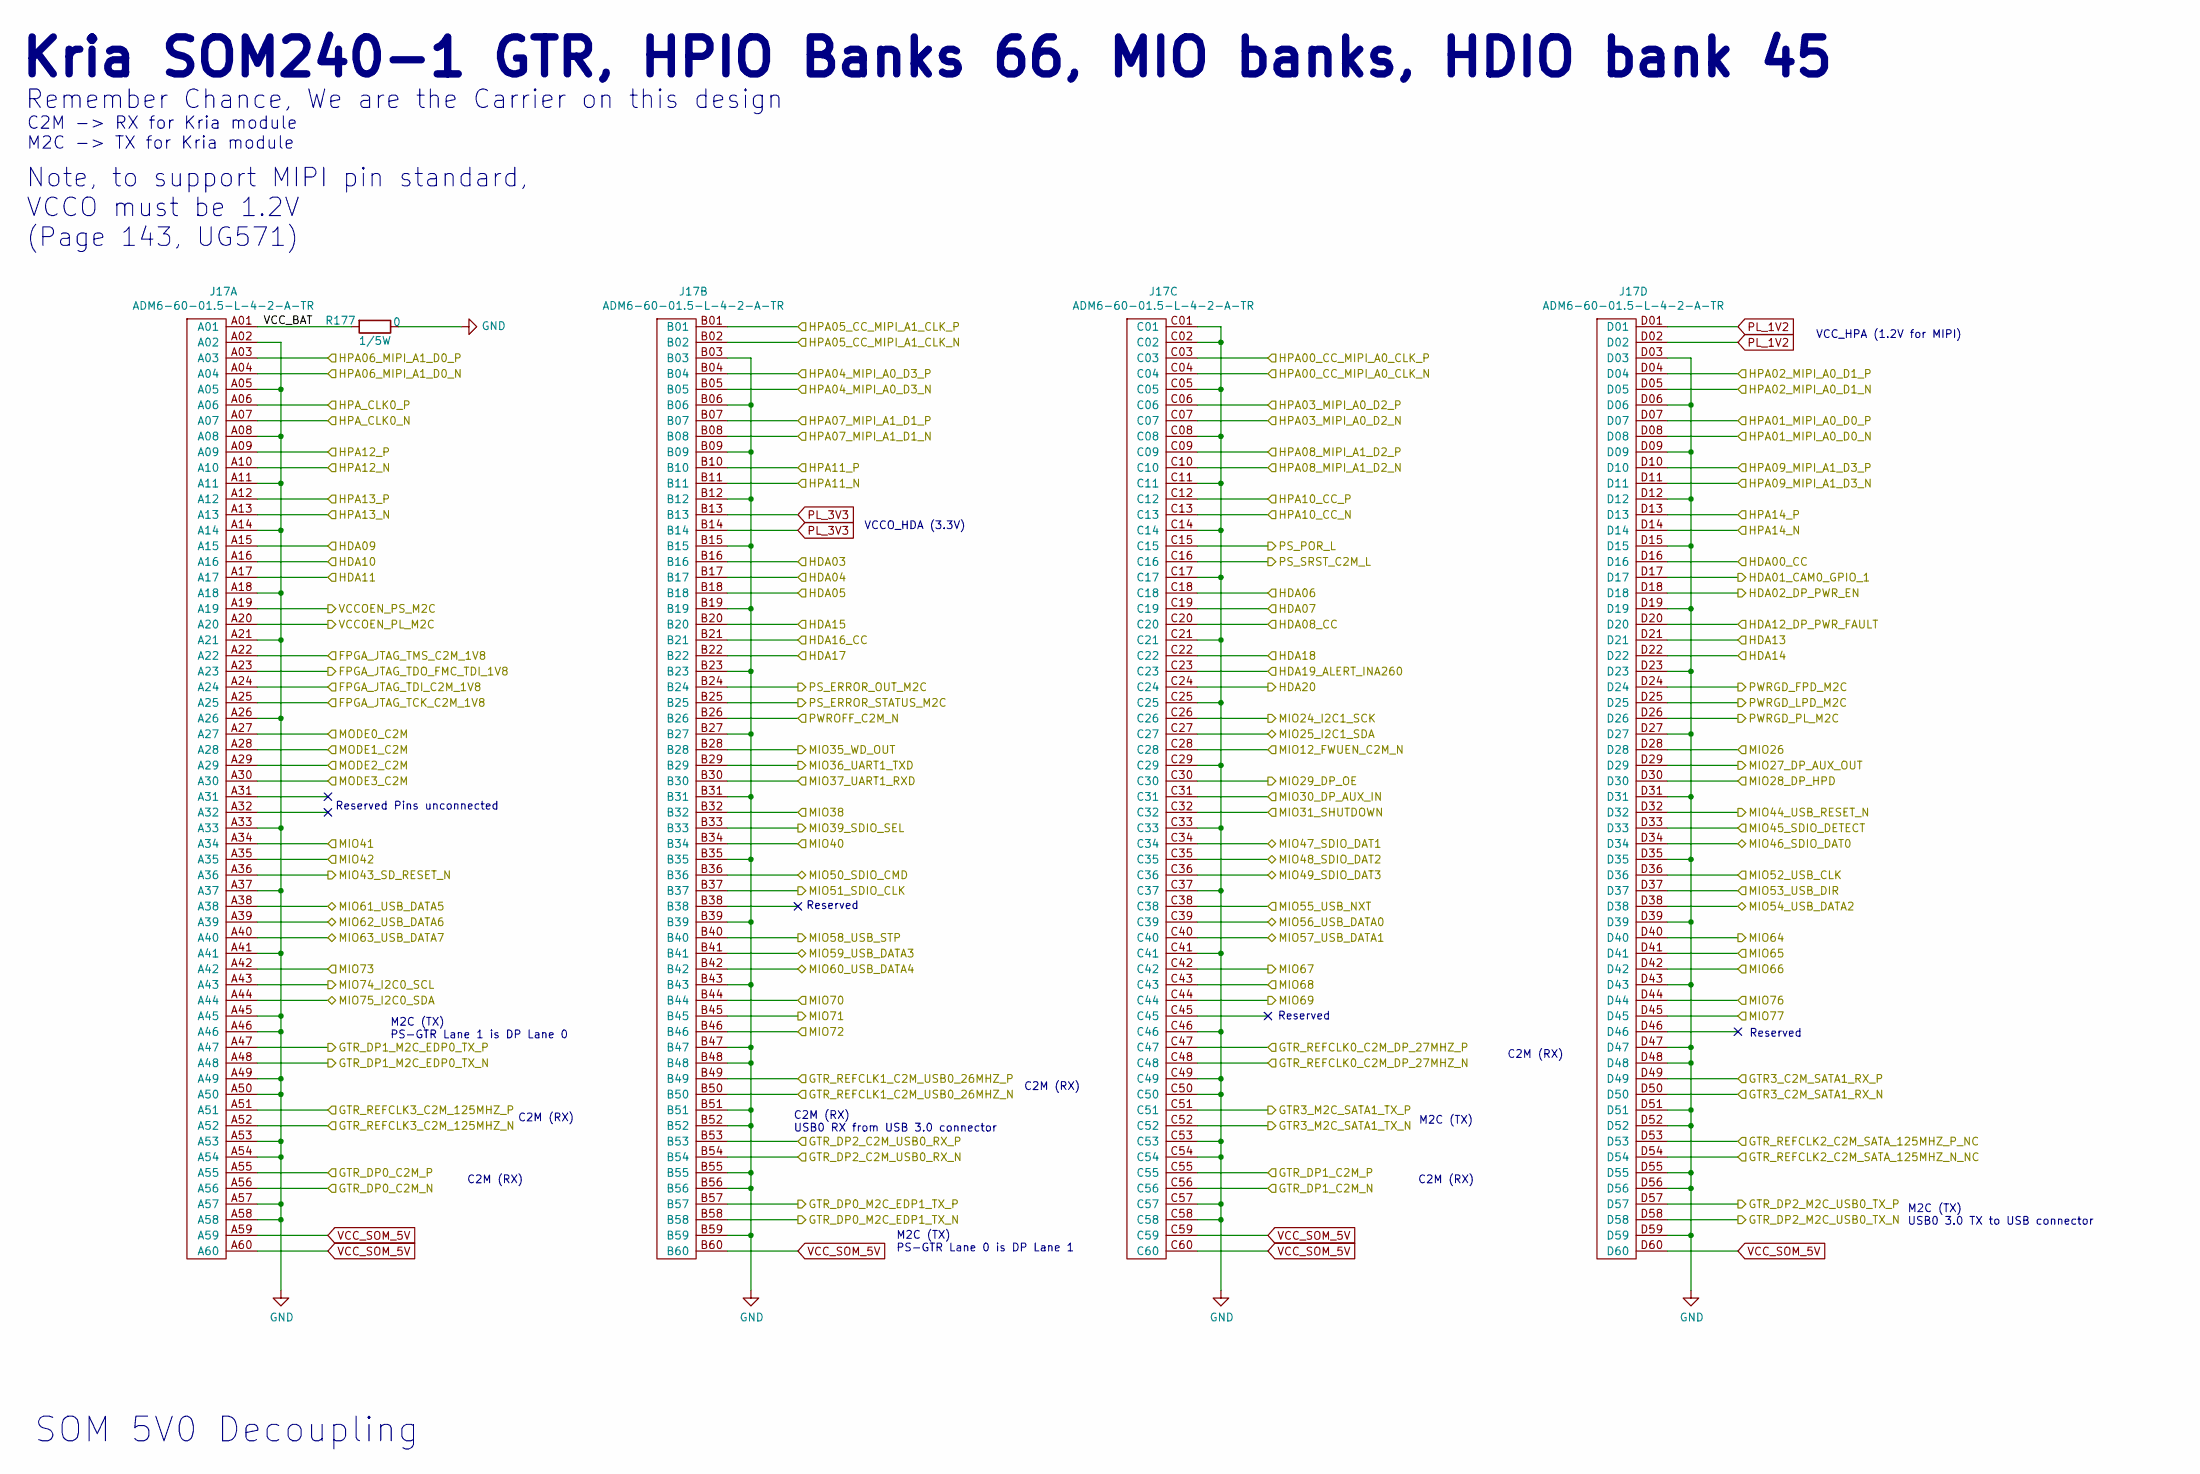
[picture p24: schematic SOM240_1.kicad_sch]

Parts:
J17: ADM6-60-01.5-L-4-2-A-TR
R177: 0; R_0402_1005Metric; PartNumber CRCW04020000Z0EDHP

Connections:
FPGA_JTAG_TCK_C2M_1V8: J17.A25
FPGA_JTAG_TDI_C2M_1V8: J17.A24
FPGA_JTAG_TDO_FMC_TDI_1V8: J17.A23
FPGA_JTAG_TMS_C2M_1V8: J17.A22
GND: J17.A02, J17.A05, J17.A08, J17.A11, J17.A14, J17.A18, J17.A21, J17.A26, J17.A33, J17.A37, J17.A41, J17.A45, J17.A46, J17.A49, J17.A50, J17.A53, J17.A54, J17.A57, J17.A58, J17.B03, J17.B06, J17.B09, J17.B12, J17.B15, J17.B19, J17.B23, J17.B27, J17.B31, J17.B35, J17.B39, J17.B43, J17.B47, J17.B48, J17.B51, J17.B52, J17.B55, J17.B56, J17.B59, J17.C01, J17.C02, J17.C05, J17.C08, J17.C11, J17.C14, J17.C17, J17.C21, J17.C25, J17.C29, J17.C33, J17.C37, J17.C41, J17.C46, J17.C49, J17.C50, J17.C53, J17.C54, J17.C57, J17.C58, J17.D03, J17.D06, J17.D09, J17.D12, J17.D15, J17.D19, J17.D23, J17.D27, J17.D31, J17.D35, J17.D39, J17.D43, J17.D47, J17.D48, J17.D51, J17.D52, J17.D55, J17.D56, J17.D59, R177.1
GTR3_C2M_SATA1_RX_N: J17.D50
GTR3_C2M_SATA1_RX_P: J17.D49
GTR3_M2C_SATA1_TX_N: J17.C52
GTR3_M2C_SATA1_TX_P: J17.C51
GTR_DP0_C2M_N: J17.A56
GTR_DP0_C2M_P: J17.A55
GTR_DP0_M2C_EDP1_TX_N: J17.B58
GTR_DP0_M2C_EDP1_TX_P: J17.B57
GTR_DP1_C2M_N: J17.C56
GTR_DP1_C2M_P: J17.C55
GTR_DP1_M2C_EDP0_TX_N: J17.A48
GTR_DP1_M2C_EDP0_TX_P: J17.A47
GTR_DP2_C2M_USB0_RX_N: J17.B54
GTR_DP2_C2M_USB0_RX_P: J17.B53
GTR_DP2_M2C_USB0_TX_N: J17.D58
GTR_DP2_M2C_USB0_TX_P: J17.D57
GTR_REFCLK0_C2M_DP_27MHZ_N: J17.C48
GTR_REFCLK0_C2M_DP_27MHZ_P: J17.C47
GTR_REFCLK1_C2M_USB0_26MHZ_N: J17.B50
GTR_REFCLK1_C2M_USB0_26MHZ_P: J17.B49
GTR_REFCLK2_C2M_SATA_125MHZ_N_NC: J17.D54
GTR_REFCLK2_C2M_SATA_125MHZ_P_NC: J17.D53
GTR_REFCLK3_C2M_125MHZ_N: J17.A52
GTR_REFCLK3_C2M_125MHZ_P: J17.A51
HDA00_CC: J17.D16
HDA01_CAM0_GPIO_1: J17.D17
HDA02_DP_PWR_EN: J17.D18
HDA03: J17.B16
HDA04: J17.B17
HDA05: J17.B18
HDA06: J17.C18
HDA07: J17.C19
HDA08_CC: J17.C20
HDA09: J17.A15
HDA10: J17.A16
HDA11: J17.A17
HDA12_DP_PWR_FAULT: J17.D20
HDA13: J17.D21
HDA14: J17.D22
HDA15: J17.B20
HDA16_CC: J17.B21
HDA17: J17.B22
HDA18: J17.C22
HDA19_ALERT_INA260: J17.C23
HDA20: J17.C24
HPA00_CC_MIPI_A0_CLK_N: J17.C04
HPA00_CC_MIPI_A0_CLK_P: J17.C03
HPA01_MIPI_A0_D0_N: J17.D08
HPA01_MIPI_A0_D0_P: J17.D07
HPA02_MIPI_A0_D1_N: J17.D05
HPA02_MIPI_A0_D1_P: J17.D04
HPA03_MIPI_A0_D2_N: J17.C07
HPA03_MIPI_A0_D2_P: J17.C06
HPA04_MIPI_A0_D3_N: J17.B05
HPA04_MIPI_A0_D3_P: J17.B04
HPA05_CC_MIPI_A1_CLK_N: J17.B02
HPA05_CC_MIPI_A1_CLK_P: J17.B01
HPA06_MIPI_A1_D0_N: J17.A04
HPA06_MIPI_A1_D0_P: J17.A03
HPA07_MIPI_A1_D1_N: J17.B08
HPA07_MIPI_A1_D1_P: J17.B07
HPA08_MIPI_A1_D2_N: J17.C10
HPA08_MIPI_A1_D2_P: J17.C09
HPA09_MIPI_A1_D3_N: J17.D11
HPA09_MIPI_A1_D3_P: J17.D10
HPA10_CC_N: J17.C13
HPA10_CC_P: J17.C12
HPA11_N: J17.B11
HPA11_P: J17.B10
HPA12_N: J17.A10
HPA12_P: J17.A09
HPA13_N: J17.A13
HPA13_P: J17.A12
HPA14_N: J17.D14
HPA14_P: J17.D13
HPA_CLK0_N: J17.A07
HPA_CLK0_P: J17.A06
MIO12_FWUEN_C2M_N: J17.C28
MIO24_I2C1_SCK: J17.C26
MIO25_I2C1_SDA: J17.C27
MIO26: J17.D28
MIO27_DP_AUX_OUT: J17.D29
MIO28_DP_HPD: J17.D30
MIO29_DP_OE: J17.C30
MIO30_DP_AUX_IN: J17.C31
MIO31_SHUTDOWN: J17.C32
MIO35_WD_OUT: J17.B28
MIO36_UART1_TXD: J17.B29
MIO37_UART1_RXD: J17.B30
MIO38: J17.B32
MIO39_SDIO_SEL: J17.B33
MIO40: J17.B34
MIO41: J17.A34
MIO42: J17.A35
MIO43_SD_RESET_N: J17.A36
MIO44_USB_RESET_N: J17.D32
MIO45_SDIO_DETECT: J17.D33
MIO46_SDIO_DAT0: J17.D34
MIO47_SDIO_DAT1: J17.C34
MIO48_SDIO_DAT2: J17.C35
MIO49_SDIO_DAT3: J17.C36
MIO50_SDIO_CMD: J17.B36
MIO51_SDIO_CLK: J17.B37
MIO52_USB_CLK: J17.D36
MIO53_USB_DIR: J17.D37
MIO54_USB_DATA2: J17.D38
MIO55_USB_NXT: J17.C38
MIO56_USB_DATA0: J17.C39
MIO57_USB_DATA1: J17.C40
MIO58_USB_STP: J17.B40
MIO59_USB_DATA3: J17.B41
MIO60_USB_DATA4: J17.B42
MIO61_USB_DATA5: J17.A38
MIO62_USB_DATA6: J17.A39
MIO63_USB_DATA7: J17.A40
MIO64: J17.D40
MIO65: J17.D41
MIO66: J17.D42
MIO67: J17.C42
MIO68: J17.C43
MIO69: J17.C44
MIO70: J17.B44
MIO71: J17.B45
MIO72: J17.B46
MIO73: J17.A42
MIO74_I2C0_SCL: J17.A43
MIO75_I2C0_SDA: J17.A44
MIO76: J17.D44
MIO77: J17.D45
MODE0_C2M: J17.A27
MODE1_C2M: J17.A28
MODE2_C2M: J17.A29
MODE3_C2M: J17.A30
PL_1V2: J17.D01, J17.D02
PL_3V3: J17.B13, J17.B14
PS_ERROR_OUT_M2C: J17.B24
PS_ERROR_STATUS_M2C: J17.B25
PS_POR_L: J17.C15
PS_SRST_C2M_L: J17.C16
PWRGD_FPD_M2C: J17.D24
PWRGD_LPD_M2C: J17.D25
PWRGD_PL_M2C: J17.D26
PWROFF_C2M_N: J17.B26
VCCOEN_PL_M2C: J17.A20
VCCOEN_PS_M2C: J17.A19
VCC_BAT: J17.A01, R177.2
VCC_SOM_5V: J17.A59, J17.A60, J17.B60, J17.C59, J17.C60, J17.D60

Notes on the sheet:
C2M (RX) USB0 RX from USB 3.0 connector
SOM 5V0 Decoupling
Note, to support MIPI pin standard, VCCO must be 1.2V (Page 143, UG571)
Remember Chance, We are the Carrier on this design
M2C (TX) PS-GTR Lane 0 is DP Lane 1
C2M (RX)
Reserved
M2C (TX)
VCC_HPA (1.2V for MIPI)
C2M -> RX for Kria module M2C -> TX for Kria module
VCCO_HDA (3.3V)
M2C (TX) PS-GTR Lane 1 is DP Lane 0
Kria SOM240-1 GTR, HPIO Banks 66, MIO banks, HDIO bank 45
Reserved Pins unconnected
M2C (TX) USB0 3.0 TX to USB connector
