ApotheoTech/Aper-Oculus/UART_JTAG.kicad_sch

## KiCad design UART_JTAG.kicad_sch (2023-12-22)

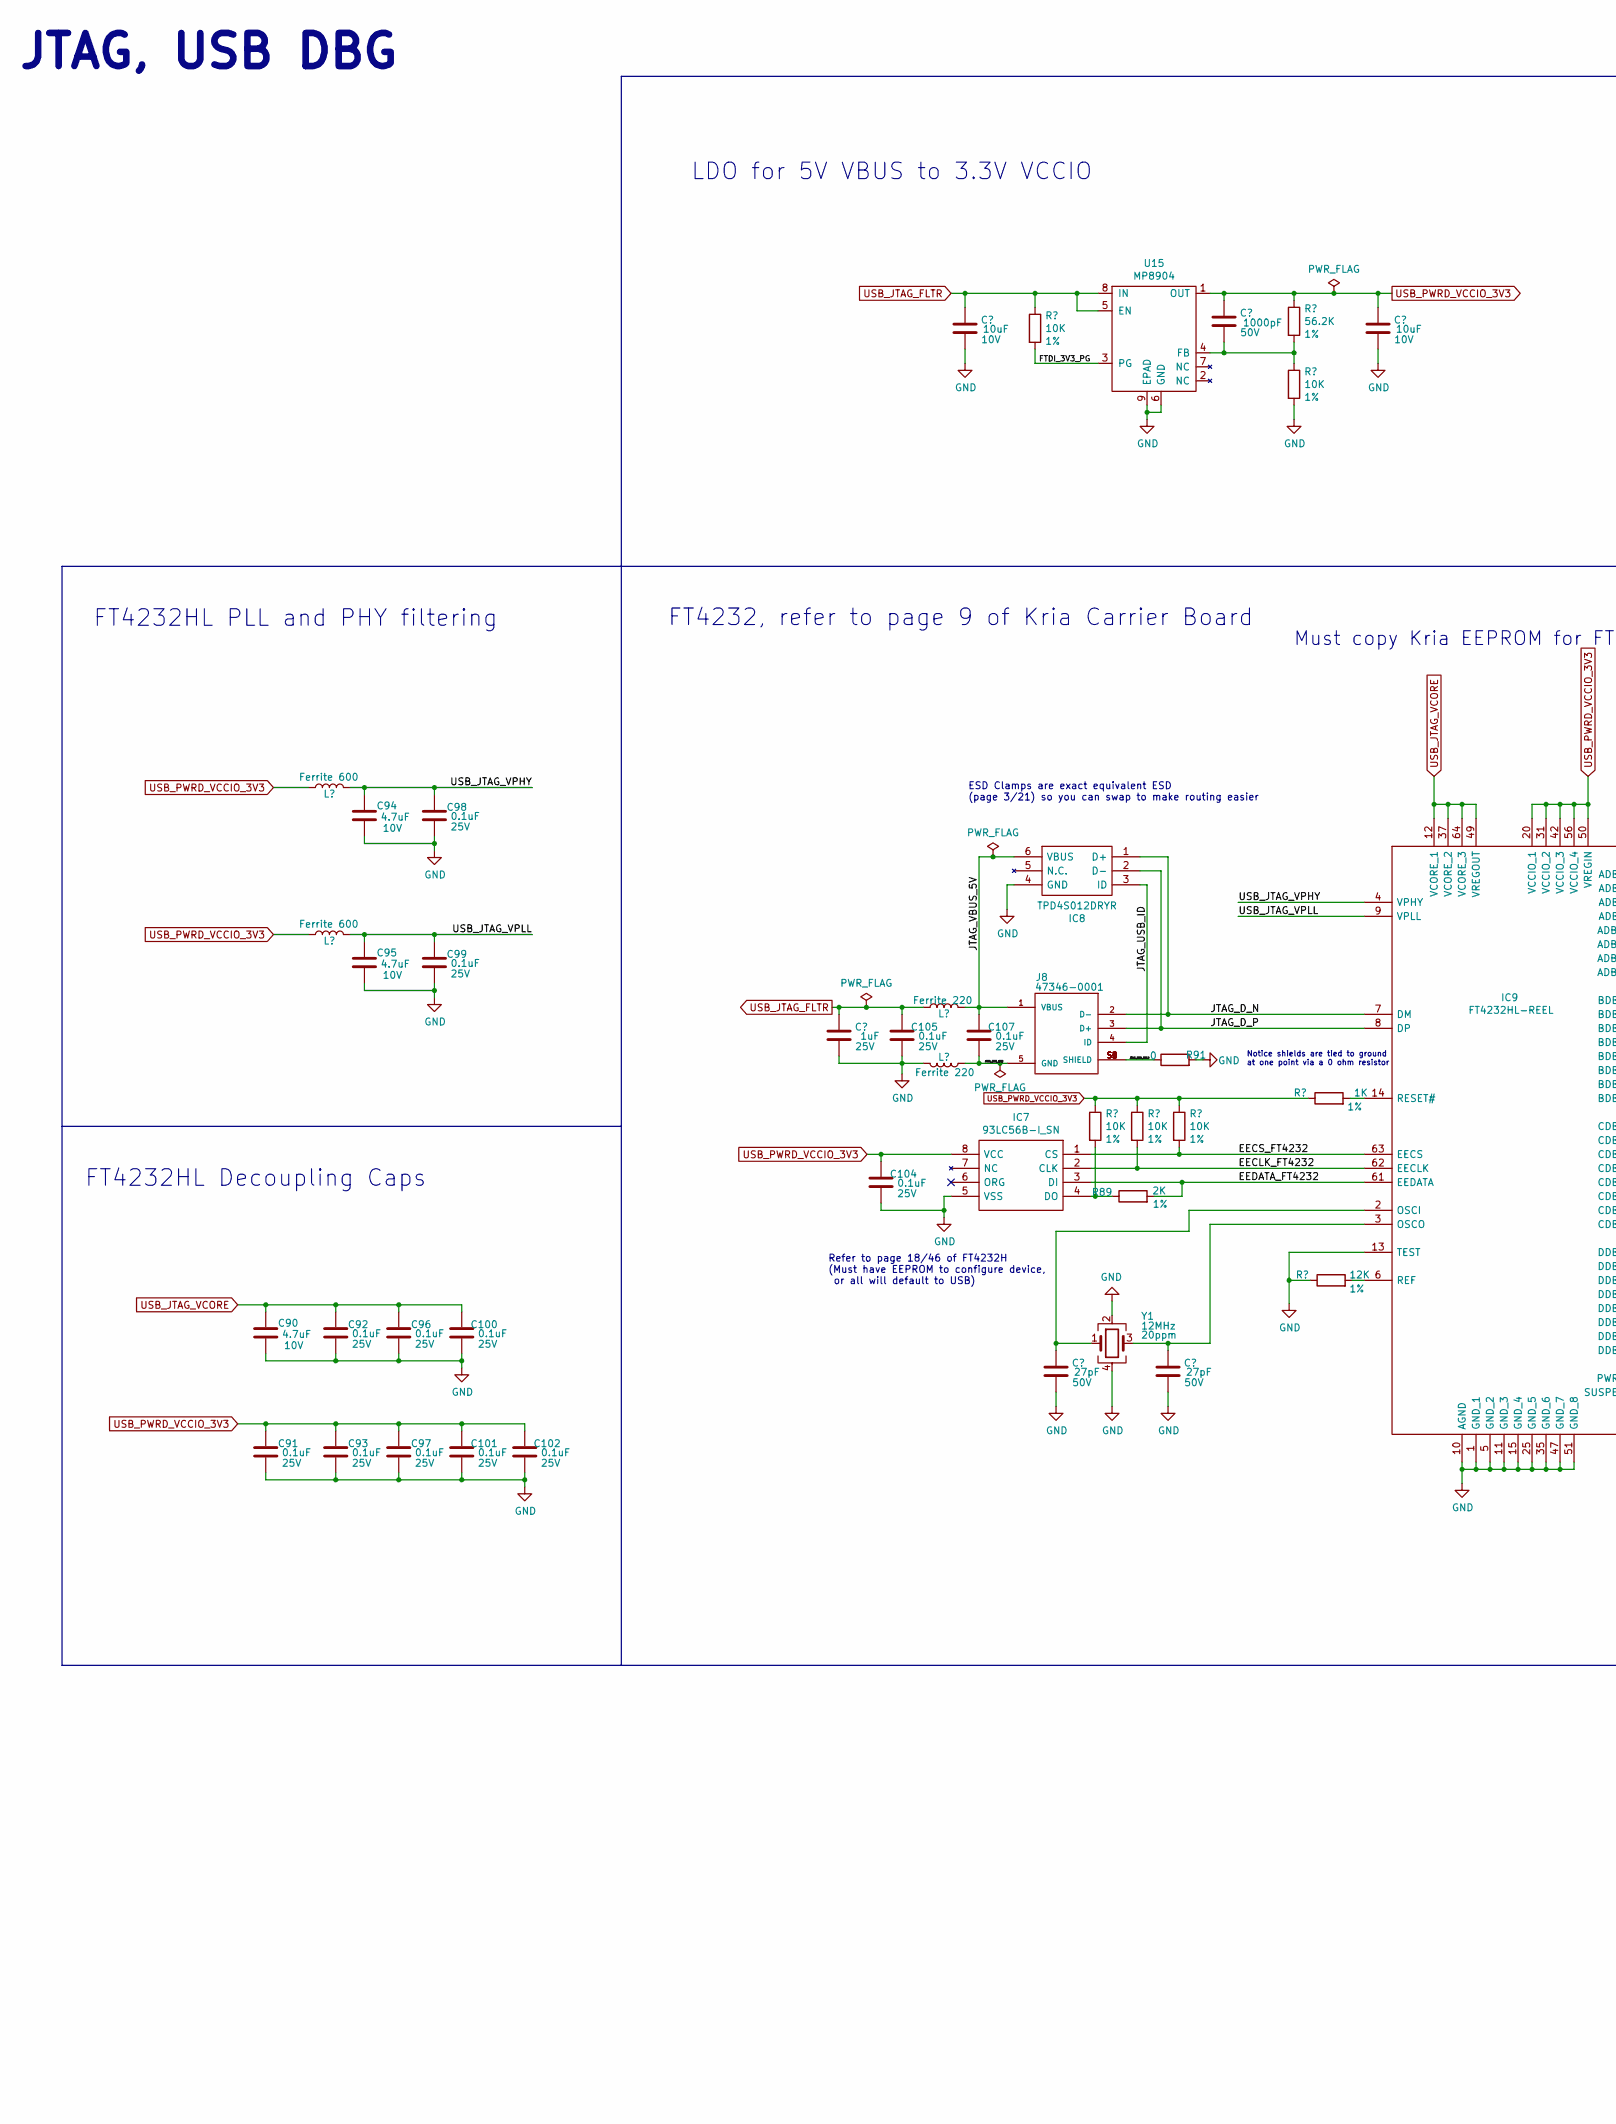
[picture p25: schematic UART_JTAG.kicad_sch, part in row 1, column 1]

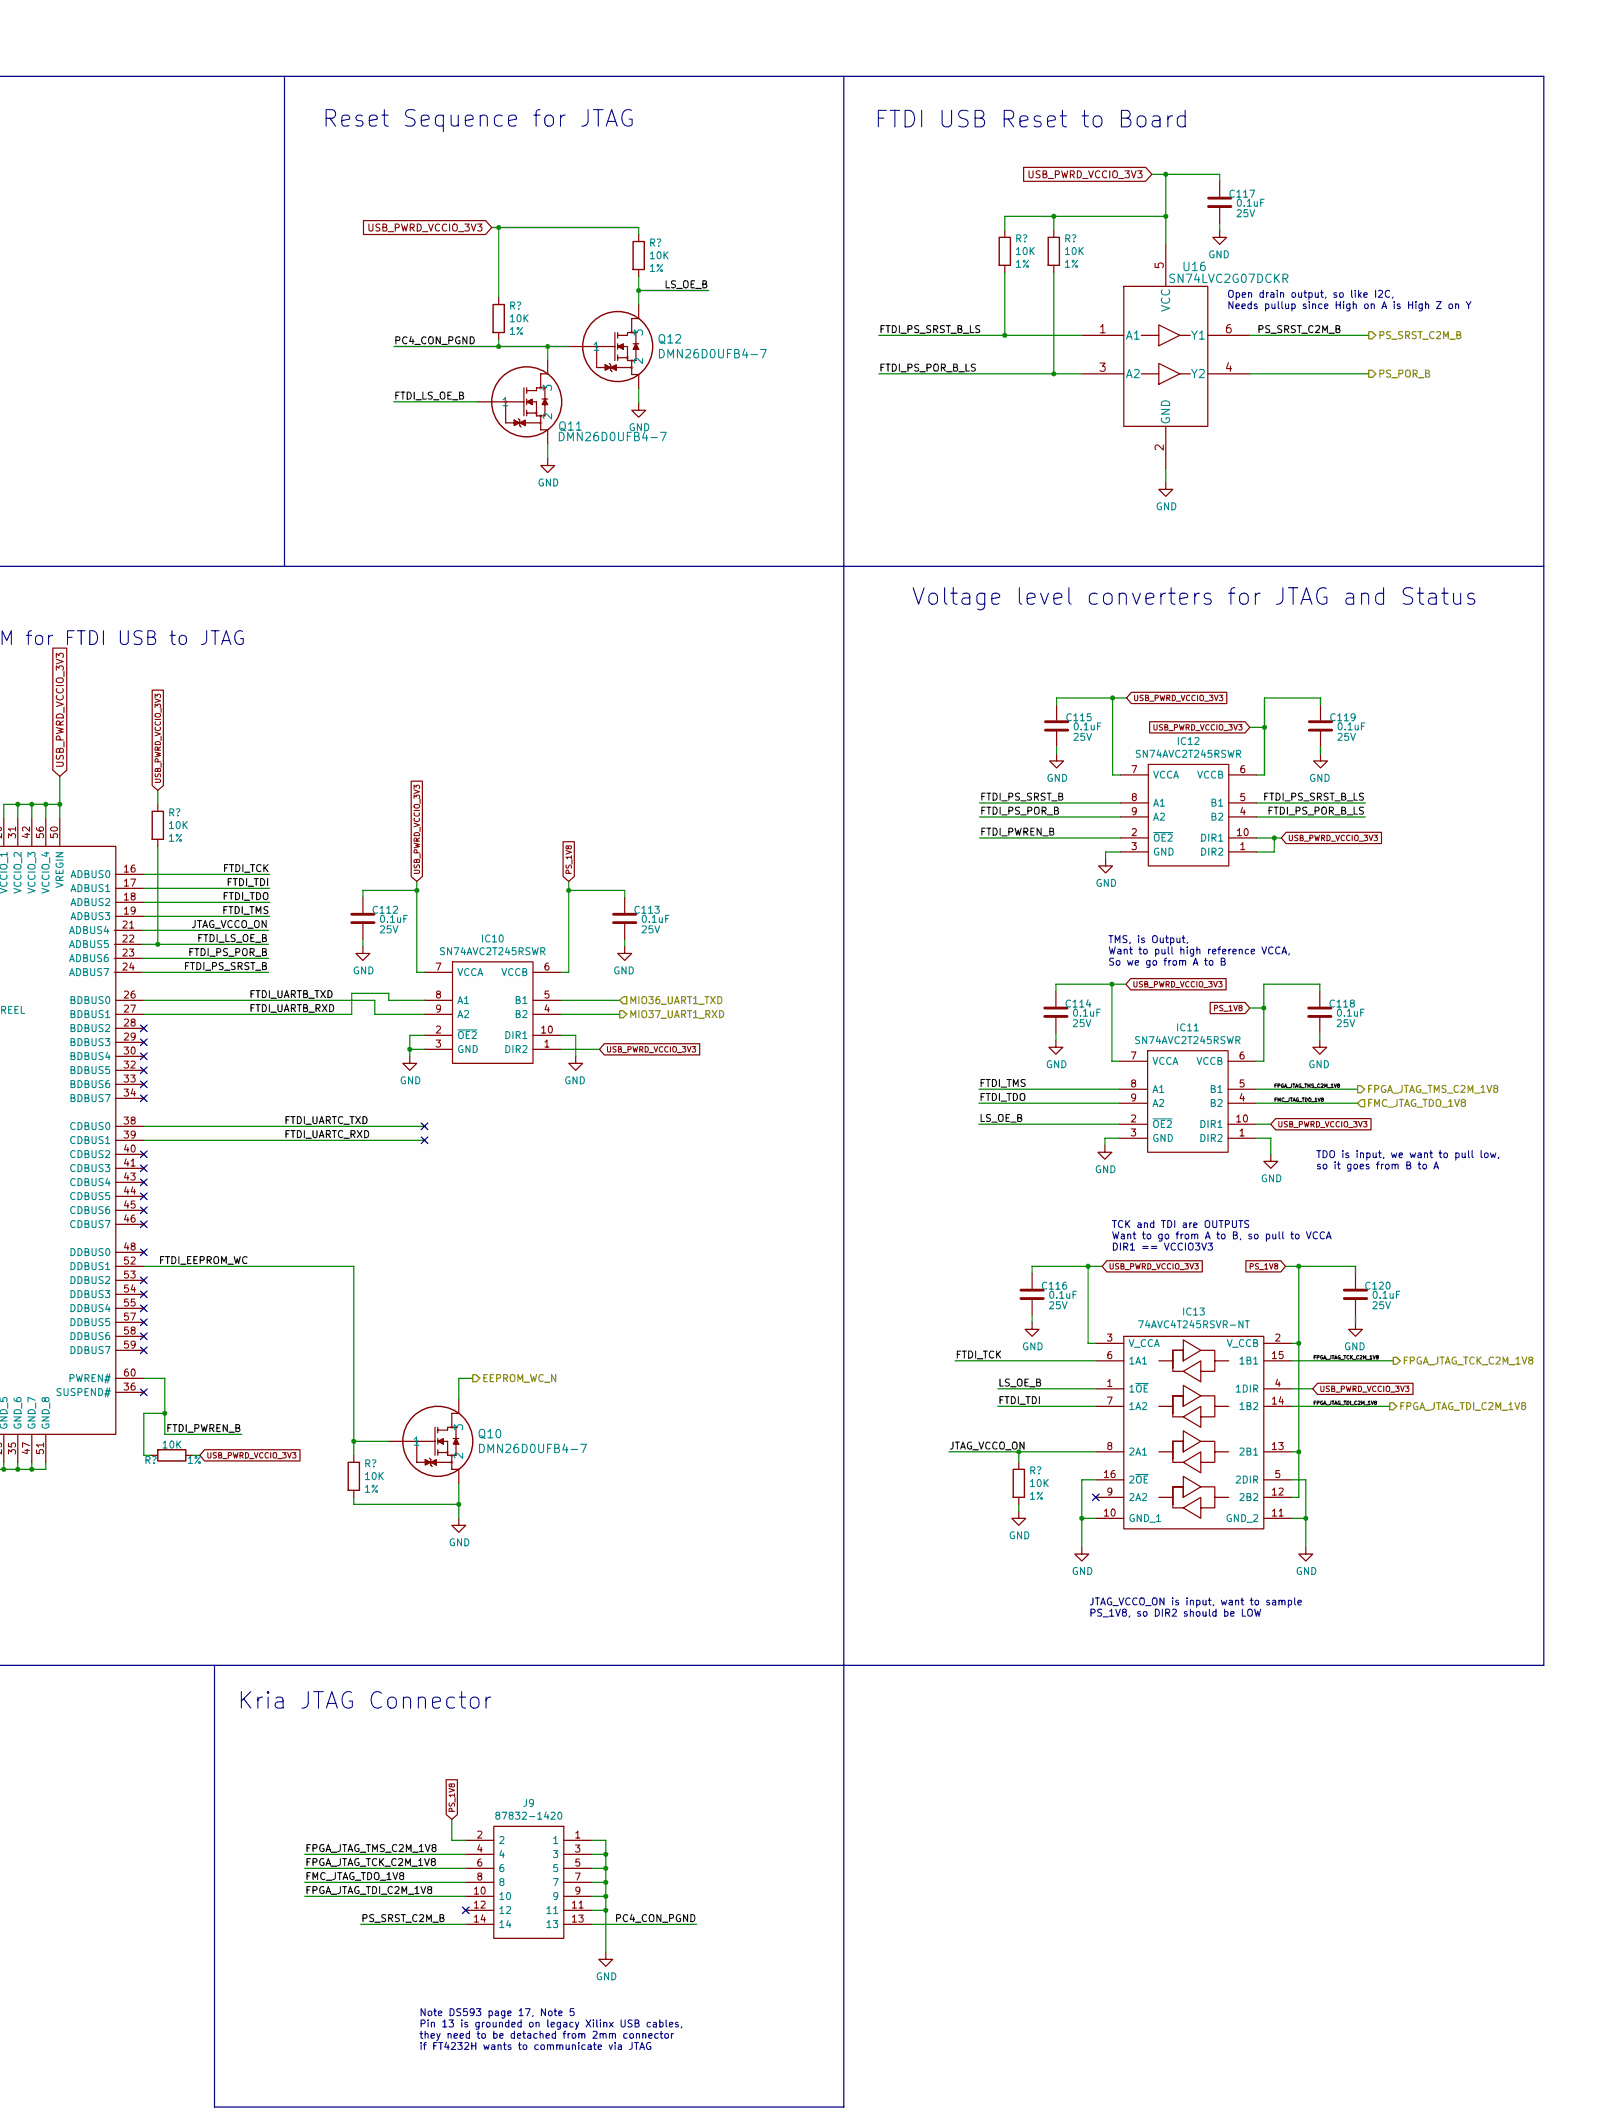
[picture p26: schematic UART_JTAG.kicad_sch, part in row 1, column 2]

Parts:
C90, C94, C95: 4.7uF; C_0402_1005Metric; Tolerance +-10%; Voltage 10V; PartNumber CL05A475KP5NRNC
C91, C92, C93, C96, C97, C98, C99, C100, C101, C102, C104, C105, C107, C112, C113, C114, C115, C116, C117, C118, C119, C120: 0.1uF; C_0402_1005Metric; Tolerance +-10%; Voltage 25V; PartNumber TMK105BJ104KVHF
C103: 1uF; C_0402_1005Metric; Tolerance +-10%; Voltage 25V; PartNumber C1005X5R1E105K050BE
C106, C111: 10uF; C_0402_1005Metric; Tolerance +-20%; Voltage 10V; PartNumber CL05A106MP5NUNC
C108, C109: 27pF; C_0402_1005Metric; Tolerance +-5%; Voltage 50V; PartNumber C0402C270J5GACTU
C110: 1000pF; C_0402_1005Metric; Tolerance +-10%; Voltage 50V; PartNumber C1005X7R1H102K050BA
IC7: 93LC56B-I_SN; Mouser Part Number 579-93LC56BISN
IC8: TPD4S012DRYR; Mouser Part Number 595-TPD4S012DRYR
IC9: FT4232HL-REEL; Mouser Part Number 895-FT4232HL
IC10, IC11, IC12: SN74AVC2T245RSWR; Mouser Part Number 595-SN74AVC2T245RSWR
IC13: 74AVC4T245RSVR-NT; Mouser Part Number 595-74AVC4T245RSVRNT
J8: 47346-0001; MOLEX_47346-0001
J9: 87832-1420; Mouser Part Number 538-87832-1420
L10, L11: Ferrite 600; L_0805_2012Metric; PartNumber HZ0805E601R-10
L12, L13: Ferrite 220; L_0603_1608Metric; PartNumber MPZ1608S221ATA00
Q10, Q11, Q12: DMN26D0UFB4-7
R87, R88, R90, R92, R94, R97, R98, R99, R100, R101, R102, R103, R104: 10K; R_0402_1005Metric; Tolerance 1%; PartNumber ERJ-2RKF1002X
R89: 2K; R_0402_1005Metric; Tolerance 1%; PartNumber ERJ-2RKF2001X
R91: 0; R_0402_1005Metric; PartNumber CRCW04020000Z0EDHP
R93: 56.2K; R_0402_1005Metric; Tolerance 1%; PartNumber ERJ-2RKF5622X
R95: 1K; R_0402_1005Metric; Tolerance 1%; PartNumber ERJ-2RKF1001X‎
R96: 12K; R_0402_1005Metric; Tolerance 1%; PartNumber ERJ-2RKF1202X
U15: MP8904; MP8904DD
U16: SN74LVC2G07DCKR; SN74AXC1T45DCKR
Y1: 12MHz; Crystal_3.2x2.5mm_12MHz; Tolerance 20ppm; PartNumber RH100-12.000-18-2030-EXT-TR

Connections:
EECLK_FT4232: IC7.2 (CLK), IC9.62 (EECLK), R90.2
EECS_FT4232: IC7.1 (CS), IC9.63 (EECS), R92.2
EEDATA_FT4232: IC7.3 (DI), IC9.61 (EEDATA), R89.2
EEPROM_WC_N: Q10.3
FMC_JTAG_TDO_1V8: IC11.4 (B2), J9.8
FPGA_JTAG_TCK_C2M_1V8: IC13.15 (1B1), J9.6
FPGA_JTAG_TDI_C2M_1V8: IC13.14 (1B2), J9.10
FPGA_JTAG_TMS_C2M_1V8: IC11.5 (B1), J9.4
FTDI_3V3_PG: R87.2, U15.3 (PG)
FTDI_EEPROM_WC: IC9.52 (DDBUS1), Q10.1, R99.1
FTDI_LS_OE_B: IC9.22 (ADBUS5), Q11.1, R97.2
FTDI_PS_POR_B: IC9.23 (ADBUS6), IC12.9 (A2)
FTDI_PS_POR_B_LS: IC12.4 (B2), R104.2, U16.3 (A2)
FTDI_PS_SRST_B: IC9.24 (ADBUS7), IC12.8 (A1)
FTDI_PS_SRST_B_LS: IC12.5 (B1), R102.2, U16.1 (A1)
FTDI_PWREN_B: IC9.60 (PWREN#), IC12.2 (~OE2), R98.2
FTDI_TCK: IC9.16 (ADBUS0), IC13.6 (1A1)
FTDI_TDI: IC9.17 (ADBUS1), IC13.7 (1A2)
FTDI_TDO: IC9.18 (ADBUS2), IC11.9 (A2)
FTDI_TMS: IC9.19 (ADBUS3), IC11.8 (A1)
FTDI_UARTB_RXD: IC9.27 (BDBUS1), IC10.8 (A1)
FTDI_UARTB_TXD: IC9.26 (BDBUS0), IC10.9 (A2)
FTDI_UARTC_RXD: IC9.39 (CDBUS1)
FTDI_UARTC_TXD: IC9.38 (CDBUS0)
GND: C90.2, C91.1, C92.1, C93.1, C94.2, C95.2, C96.1, C97.1, C98.1, C99.1, C100.1, C101.1, C102.1, C103.1, C104.1, C105.1, C106.1, C108.1, C109.1, C111.1, C112.1, C113.1, C114.1, C115.1, C116.1, C117.1, C118.1, C119.1, C120.1, IC7.5 (VSS), IC8.4 (GND), IC9.1 (GND_1), IC9.5 (GND_2), IC9.10 (AGND), IC9.11 (GND_3), IC9.13 (TEST), IC9.15 (GND_4), IC9.25 (GND_5), IC9.35 (GND_6), IC9.47 (GND_7), IC9.51 (GND_8), IC10.2 (~OE2), IC10.3 (GND), IC10.10 (DIR1), IC11.1 (DIR2), IC11.3 (GND), IC12.3 (GND), IC13.5 (2DIR), IC13.10 (GND_1), IC13.11 (GND_2), IC13.16 (2~OE), J9.1, J9.3, J9.5, J9.7, J9.9, J9.11, L13.2, Q10.2, Q11.2, Q12.2, R91.2, R94.2, R96.1, R99.2, R103.2, U15.6 (GND), U15.9 (EPAD), U16.2 (GND), Y1.2, Y1.4
JTAG_D_N: IC8.1 (D+), IC9.7 (DM), J8.2 (D-)
JTAG_D_P: IC8.2 (D-), IC9.8 (DP), J8.3 (D+)
JTAG_USB_GND: C107.1, J8.5 (GND), L13.1
JTAG_USB_ID: IC8.3 (ID), J8.4 (ID)
JTAG_USB_SHLD: J8.S1 (SHIELD), J8.S2 (SHIELD), J8.S3 (SHIELD), J8.S4 (SHIELD), J8.S5 (SHIELD), J8.S6 (SHIELD), R91.1
JTAG_VBUS_5V: C107.2, IC8.6 (VBUS), J8.1 (VBUS), L12.2
JTAG_VCCO_ON: IC9.21 (ADBUS4), IC13.8 (2A1), R103.1
LS_OE_B: IC11.2 (~OE2), IC13.1 (1~OE), Q12.3, R101.2
MIO36_UART1_TXD: IC10.5 (B1)
MIO37_UART1_RXD: IC10.4 (B2)
unnamed: C108.2, IC9.2 (OSCI), Y1.1
unnamed: C109.2, IC9.3 (OSCO), Y1.3
unnamed: C110.1, R93.2, R94.1, U15.4 (FB)
unnamed: IC7.4 (DO), R88.2, R89.1
unnamed: IC9.6 (REF), R96.2
unnamed: IC9.14 (RESET#), R95.2
PC4_CON_PGND: J9.13, Q11.3, Q12.1, R100.2
PS_1V8: C113.2, C118.2, C120.2, IC10.6 (VCCB), IC11.6 (VCCB), IC13.2 (V_CCB), IC13.12 (2B2), IC13.13 (2B1), J9.2
PS_POR_B: U16.4 (Y2)
PS_SRST_C2M_B: J9.14, U16.6 (Y1)
USB_JTAG_FLTR: C103.2, C105.2, C106.2, L12.1, R87.1, U15.5 (EN), U15.8 (IN)
USB_JTAG_VCORE: C90.1, C92.2, C96.2, C100.2, IC9.12 (VCORE_1), IC9.37 (VCORE_2), IC9.49 (VREGOUT), IC9.64 (VCORE_3)
USB_JTAG_VPHY: C94.1, C98.2, IC9.4 (VPHY), L10.2
USB_JTAG_VPLL: C95.1, C99.2, IC9.9 (VPLL), L11.2
USB_PWRD_VCCIO_3V3: C91.2, C93.2, C97.2, C101.2, C102.2, C104.2, C110.2, C111.2, C112.2, C114.2, C115.2, C116.2, C117.2, C119.2, IC7.8 (VCC), IC9.20 (VCCIO_1), IC9.31 (VCCIO_2), IC9.42 (VCCIO_3), IC9.50 (VREGIN), IC9.56 (VCCIO_4), IC10.1 (DIR2), IC10.7 (VCCA), IC11.7 (VCCA), IC11.10 (DIR1), IC12.1 (DIR2), IC12.6 (VCCB), IC12.7 (VCCA), IC12.10 (DIR1), IC13.3 (V_CCA), IC13.4 (1DIR), L10.1, L11.1, R88.1, R90.1, R92.1, R93.1, R95.1, R97.1, R98.1, R100.1, R101.1, R102.1, R104.1, U15.1 (OUT), U16.5 (VCC)

Notes on the sheet:
Must copy Kria EEPROM for FTDI USB to JTAG
ESD Clamps are exact equivalent ESD (page 3/21) so you can swap to make routing easier
TCK and TDI are OUTPUTS Want to go from A to B, so pull to VCCA DIR1 == VCCIO3V3
Reset Sequence for JTAG
Kria JTAG Connector
FT4232HL PLL and PHY filtering
Note DS593 page 17, Note 5 Pin 13 is grounded on legacy Xilinx USB cables, they need to be detached from 2mm connector if FT4232H wants to communicate via JTAG
FT4232, refer to page 9 of Kria Carrier Board
FTDI USB Reset to Board
JTAG_VCCO_ON is input, want to sample PS_1V8, so DIR2 should be LOW
Voltage level converters for JTAG and Status
Refer to page 18/46 of FT4232H (Must have EEPROM to configure device, or all will default to USB)
Notice shields are tied to ground at one point via a 0 ohm resistor
Open drain output, so like I2C, Needs pullup since High on A is High Z on Y
JTAG, USB DBG
FT4232HL Decoupling Caps
TMS, is Output, Want to pull high reference VCCA, So we go from A to B
TDO is input, we want to pull low, so it goes from B to A
LDO for 5V VBUS to 3.3V VCCIO
