ApotheoTech/Aper-Oculus/USB-3_0.kicad_sch

## KiCad design USB-3_0.kicad_sch (2023-12-22)

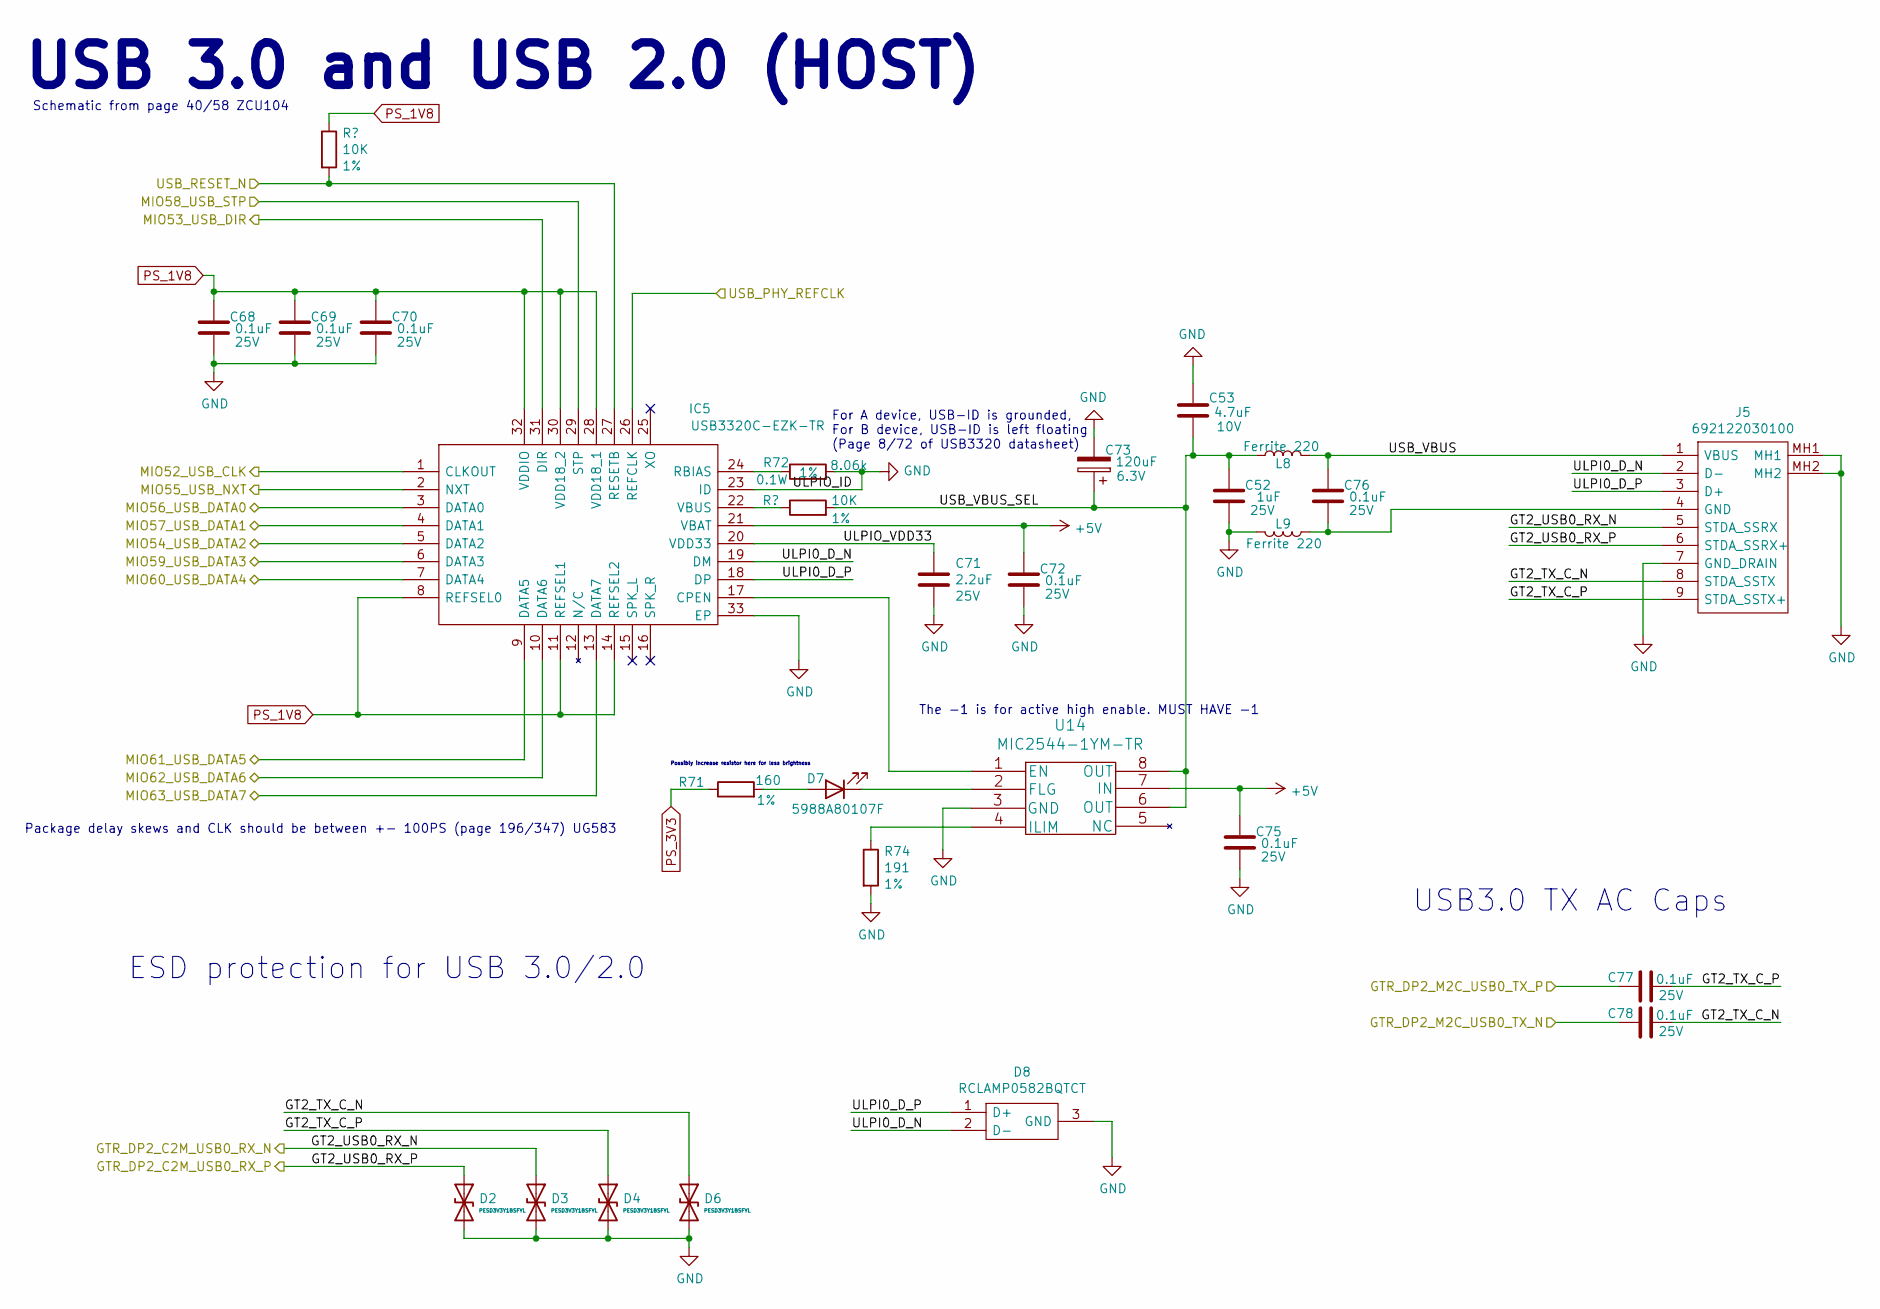
[picture p27: schematic USB-3_0.kicad_sch]

Parts:
C52: 1uF; C_0402_1005Metric; Tolerance +-10%; Voltage 25V; PartNumber C1005X5R1E105K050BE
C53: 4.7uF; C_0402_1005Metric; Tolerance +-10%; Voltage 10V; PartNumber CL05A475KP5NRNC
C68, C69, C70, C72, C75, C76, C77, C78: 0.1uF; C_0402_1005Metric; Tolerance +-10%; Voltage 25V; PartNumber TMK105BJ104KVHF
C71: 2.2uF; C_0805_2012Metric; Tolerance +-10%; Voltage 25V; PartNumber CL21B225KAFNNNE
C73: 120uF; C_0805_2012Metric; Tolerance +-10%; Voltage 6.3V; PartNumber CM21X5R107M06AT
D2, D3, D4, D6: PESD3V3Y1BSFYL; D_0201_0603Metric; PartNumber PESD3V3Y1BSFYL
D7: 5988A80107F; D_0402_1005Metric; PartNumber 5988A80107F
D8: RCLAMP0582BQTCT; PartNumber RCLAMP0582BQTCT
IC5: USB3320C-EZK-TR; Mouser Part Number 886-USB3320C-EZK-TR
J5: 692122030100; Mouser Part Number 710-692122030100
L8, L9: Ferrite 220; L_0603_1608Metric; PartNumber MPZ1608S221ATA00
R70, R73: 10K; R_0402_1005Metric; Tolerance 1%; PartNumber ERJ-2RKF1002X
R71: 160; R_0402_1005Metric; Tolerance 1%; PartNumber ERJ-2RKF1600X
R72: 8.06k; R_0402_1005Metric; Tolerance 1%; PartNumber ERJ-2RKF8061X‎
R74: 191; R_0402_1005Metric; Tolerance 1%; PartNumber CRCW0402191RFKED
U14: MIC2544-1YM-TR; PartNumber MIC2544-1YM-TR

Connections:
+5V: C72.2, C75.2, IC5.21 (VBAT), U14.7 (IN)
GND: C52.1, C53.1, C68.1, C69.1, C70.1, C71.2, C72.1, C73.2, C75.1, D2.2 (A2), D3.2 (A2), D4.2 (A2), D6.2 (A2), D8.3 (GND), IC5.23 (ID), IC5.33 (EP), J5.7 (GND_DRAIN), J5.MH1, J5.MH2, L9.2, R72.2, R74.2, U14.3 (GND)
GT2_TX_C_N: C78.2, D6.1 (A1), J5.8 (STDA_SSTX)
GT2_TX_C_P: C77.2, D4.1 (A1), J5.9 (STDA_SSTX+)
GT2_USB0_RX_N: D3.1 (A1), J5.5 (STDA_SSRX)
GT2_USB0_RX_P: D2.1 (A1), J5.6 (STDA_SSRX+)
GTR_DP2_M2C_USB0_TX_N: C78.1
GTR_DP2_M2C_USB0_TX_P: C77.1
MIO52_USB_CLK: IC5.1 (CLKOUT)
MIO53_USB_DIR: IC5.31 (DIR)
MIO54_USB_DATA2: IC5.5 (DATA2)
MIO55_USB_NXT: IC5.2 (NXT)
MIO56_USB_DATA0: IC5.3 (DATA0)
MIO57_USB_DATA1: IC5.4 (DATA1)
MIO58_USB_STP: IC5.29 (STP)
MIO59_USB_DATA3: IC5.6 (DATA3)
MIO60_USB_DATA4: IC5.7 (DATA4)
MIO61_USB_DATA5: IC5.9 (DATA5)
MIO62_USB_DATA6: IC5.10 (DATA6)
MIO63_USB_DATA7: IC5.13 (DATA7)
unnamed: C76.1, J5.4 (GND), L9.1
unnamed: D7.1 (K), U14.2 (FLG)
unnamed: D7.2 (A), R71.2
unnamed: IC5.17 (CPEN), U14.1 (EN)
unnamed: IC5.22 (VBUS), R73.1
unnamed: IC5.24 (RBIAS), R72.1
unnamed: R74.1, U14.4 (ILIM)
PS_1V8: C68.2, C69.2, C70.2, IC5.8 (REFSEL0), IC5.11 (REFSEL1), IC5.14 (REFSEL2), IC5.28 (VDD18_1), IC5.30 (VDD18_2), IC5.32 (VDDIO), R70.1
PS_3V3: R71.1
ULPI0_D_N: D8.2 (D-), IC5.19 (DM), J5.2 (D-)
ULPI0_D_P: D8.1 (D+), IC5.18 (DP), J5.3 (D+)
ULPIO_VDD33: C71.1, IC5.20 (VDD33)
USB_PHY_REFCLK: IC5.26 (REFCLK)
USB_RESET_N: IC5.27 (RESETB), R70.2
USB_VBUS: C76.2, J5.1 (VBUS), L8.2
USB_VBUS_SEL: C52.2, C53.2, C73.1, L8.1, R73.2, U14.6 (OUT), U14.8 (OUT)

Notes on the sheet:
For A device, USB-ID is grounded, For B device, USB-ID is left floating (Page 8/72 of USB3320 datasheet)
Package delay skews and CLK should be between +- 100PS (page 196/347) UG583
The -1 is for active high enable. MUST HAVE -1
Possibly increase resistor here for less brightness
USB3.0 TX AC Caps
Schematic from page 40/58 ZCU104
ESD protection for USB 3.0/2.0
USB 3.0 and USB 2.0 (HOST)
