ApotheoTech/Aper-Oculus/WD_EEPROM_PWR_LED.kicad_sch

## KiCad design WD_EEPROM_PWR_LED.kicad_sch (2023-12-22)

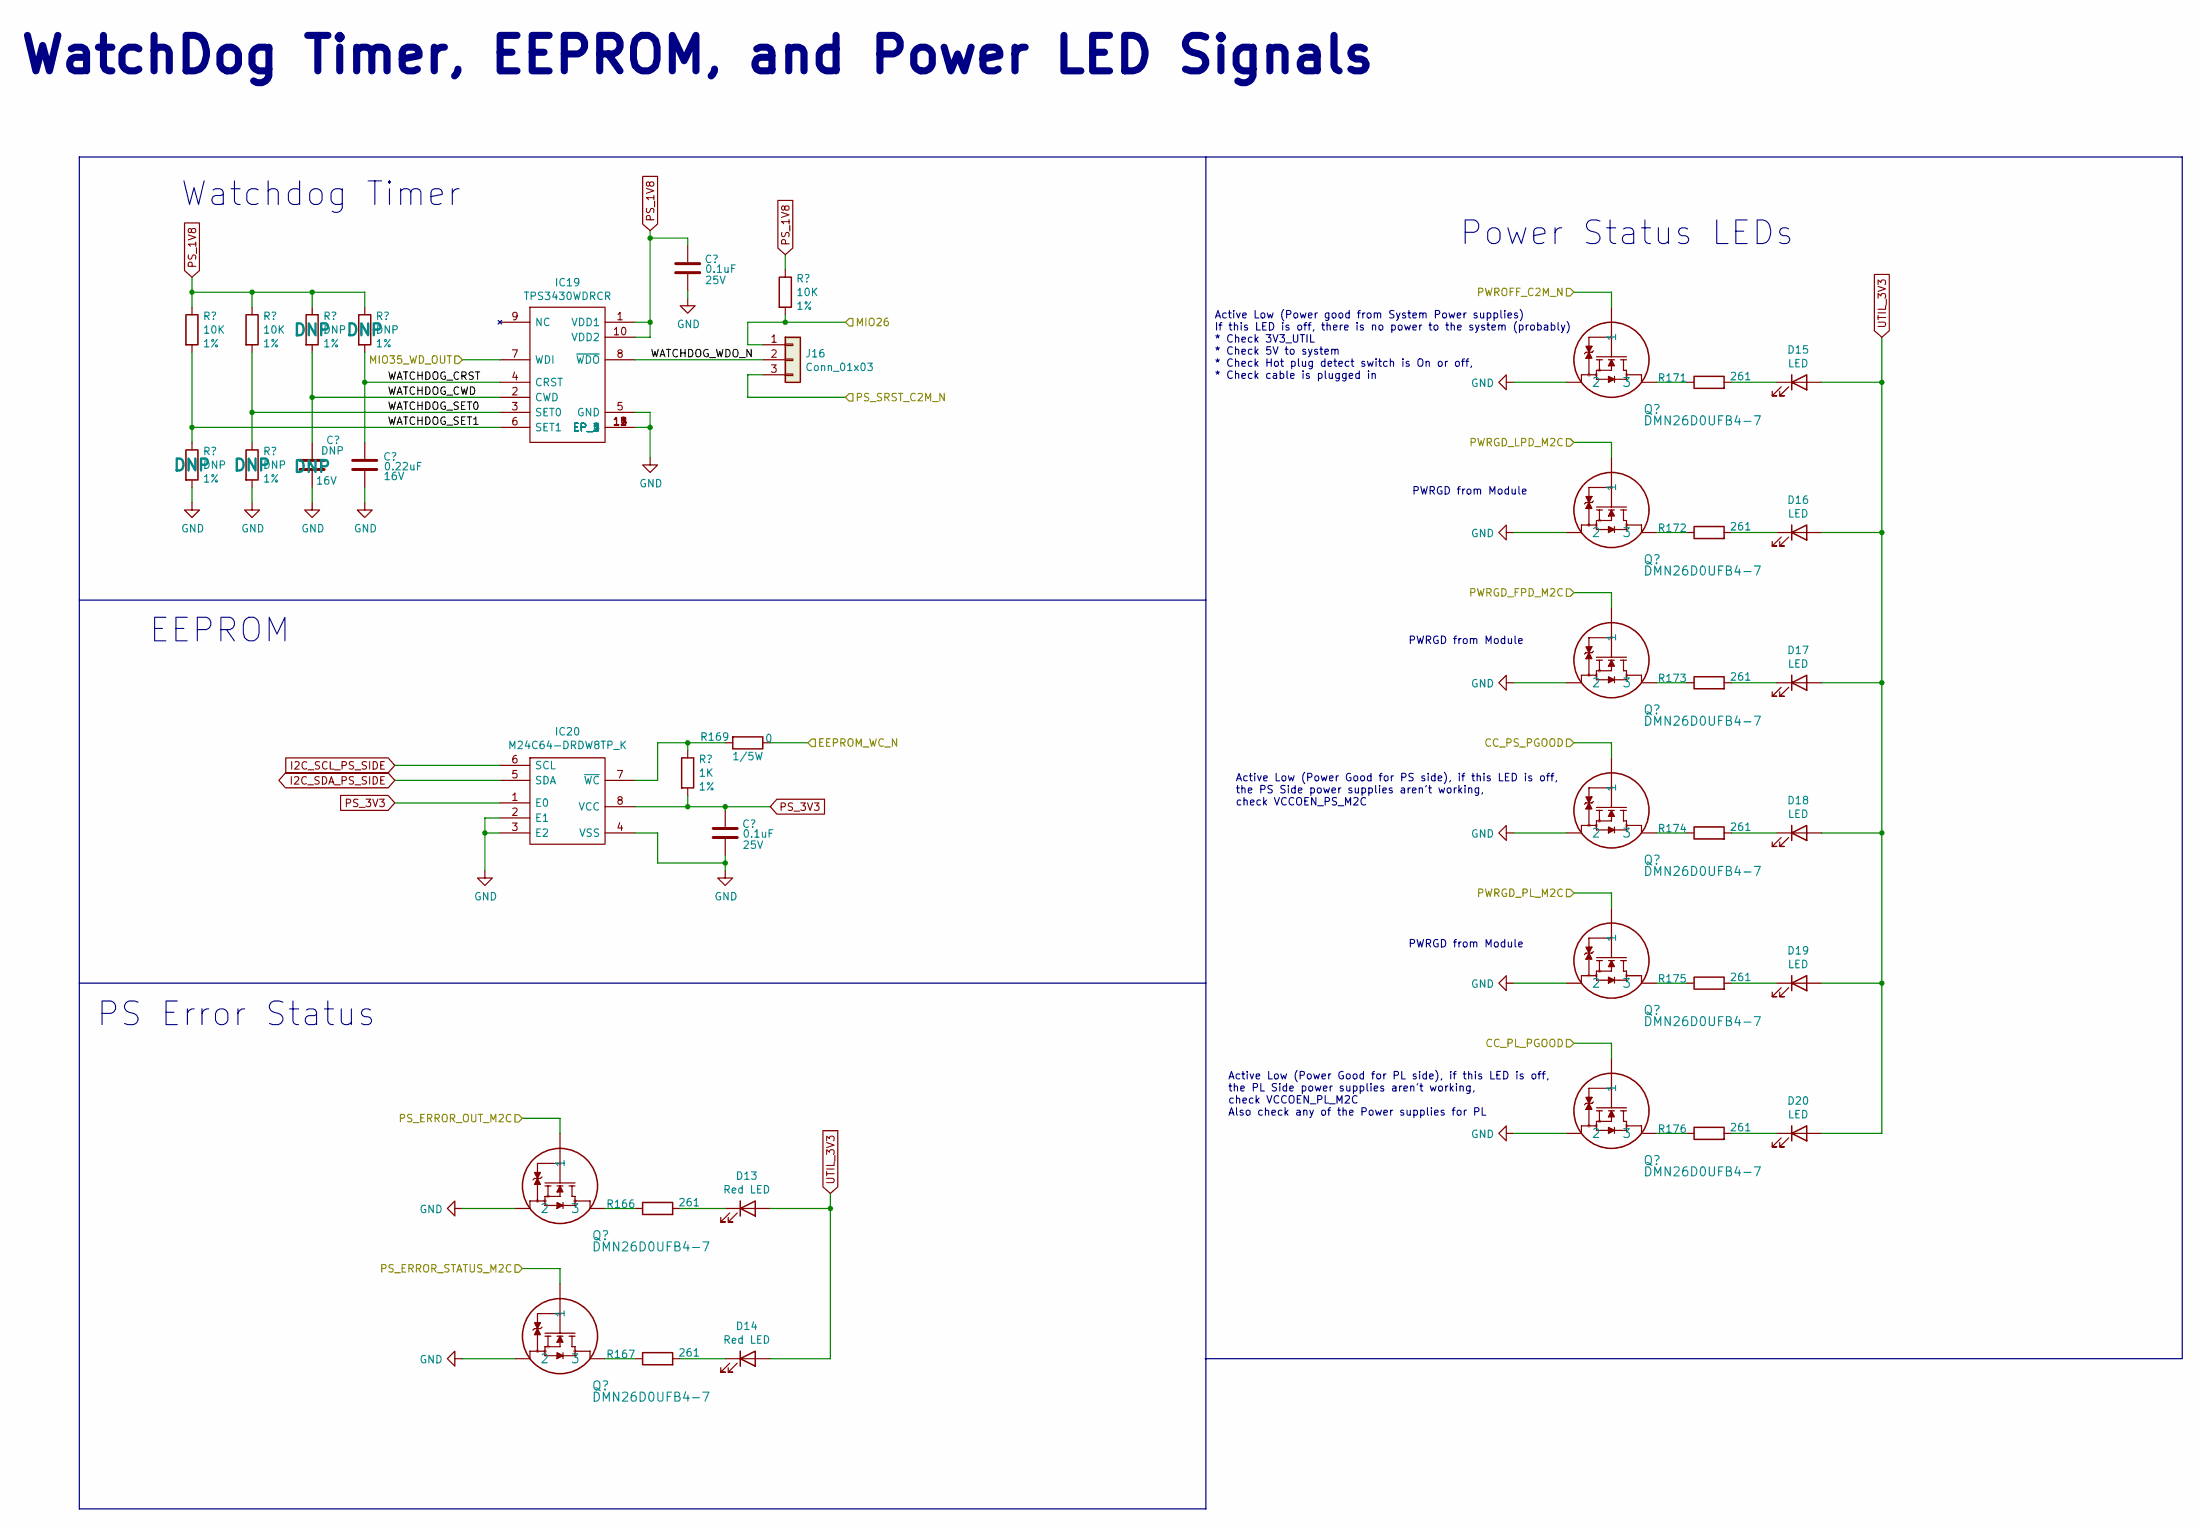
[picture p28: schematic WD_EEPROM_PWR_LED.kicad_sch]

Parts:
C196: DNP; C_0402_1005Metric; Tolerance +-10%; Voltage 16V; PartNumber CGA2B1X5R1C224K050BC
C197: 0.22uF; C_0402_1005Metric; Tolerance +-10%; Voltage 16V; PartNumber CGA2B1X5R1C224K050BC
C198, C199: 0.1uF; C_0402_1005Metric; Tolerance +-10%; Voltage 25V; PartNumber TMK105BJ104KVHF
D13, D14: Red LED; D_0603_1608Metric; PartNumber APT1608SURCK
D15, D16, D17, D18, D19, D20: LED; D_0603_1608Metric; PartNumber SML-LX0603GW-TR
IC19: TPS3430WDRCR; Mouser Part Number 595-TPS3430WDRCR
IC20: M24C64-DRDW8TP_K; Mouser Part Number 511-M24C64-DRDW8TP/K
J16: Conn_01x03; PinHeader_1x03_P2.54mm_Vertical
Q22, Q23, Q24, Q25, Q26, Q27, Q28, Q29: DMN26D0UFB4-7
R160, R162, R170: 10K; R_0402_1005Metric; Tolerance 1%; PartNumber ERJ-2RKF1002X
R161, R163, R164, R165: DNP; R_0402_1005Metric; Tolerance 1%; PartNumber ERJ-2RKF1002X
R166, R167, R171, R172, R173, R174, R175, R176: 261; R_0402_1005Metric; PartNumber ERJ-2RKF2610X
R168: 1K; R_0402_1005Metric; Tolerance 1%; PartNumber ERJ-2RKF1001X‎
R169: 0; R_0402_1005Metric; PartNumber CRCW04020000Z0EDHP

Connections:
CC_PL_PGOOD: Q29.1
CC_PS_PGOOD: Q27.1
EEPROM_WC_N: R169.1
GND: C196.1, C197.1, C198.1, C199.1, IC19.5 (GND), IC19.11 (EP_1), IC19.12 (EP_2), IC19.13 (EP_3), IC19.14 (EP_4), IC19.15 (EP_5), IC20.2 (E1), IC20.3 (E2), IC20.4 (VSS), Q22.2, Q23.2, Q24.2, Q25.2, Q26.2, Q27.2, Q28.2, Q29.2, R161.2, R163.2
I2C_SCL_PS_SIDE: IC20.6 (SCL)
I2C_SDA_PS_SIDE: IC20.5 (SDA)
MIO26: J16.1, R170.2
MIO35_WD_OUT: IC19.7 (WDI)
unnamed: D13.1 (K), R166.2
unnamed: D14.1 (K), R167.2
unnamed: D15.1 (K), R171.2
unnamed: D16.1 (K), R172.2
unnamed: D17.1 (K), R173.2
unnamed: D18.1 (K), R174.2
unnamed: D19.1 (K), R175.2
unnamed: D20.1 (K), R176.2
unnamed: IC20.7 (~WC), R168.1, R169.2
unnamed: Q22.3, R166.1
unnamed: Q23.3, R167.1
unnamed: Q24.3, R171.1
unnamed: Q25.3, R172.1
unnamed: Q26.3, R173.1
unnamed: Q27.3, R174.1
unnamed: Q28.3, R175.1
unnamed: Q29.3, R176.1
PS_1V8: C198.2, IC19.1 (VDD1), IC19.10 (VDD2), R160.1, R162.1, R164.1, R165.1, R170.1
PS_3V3: C199.2, IC20.1 (E0), IC20.8 (VCC), R168.2
PS_ERROR_OUT_M2C: Q22.1
PS_ERROR_STATUS_M2C: Q23.1
PS_SRST_C2M_N: J16.3
PWRGD_FPD_M2C: Q26.1
PWRGD_LPD_M2C: Q25.1
PWRGD_PL_M2C: Q28.1
PWROFF_C2M_N: Q24.1
UTIL_3V3: D13.2 (A), D14.2 (A), D15.2 (A), D16.2 (A), D17.2 (A), D18.2 (A), D19.2 (A), D20.2 (A)
WATCHDOG_CRST: C197.2, IC19.4 (CRST), R165.2
WATCHDOG_CWD: C196.2, IC19.2 (CWD), R164.2
WATCHDOG_SET0: IC19.3 (SET0), R162.2, R163.1
WATCHDOG_SET1: IC19.6 (SET1), R160.2, R161.1
WATCHDOG_WDO_N: IC19.8 (~WDO), J16.2

Notes on the sheet:
EEPROM
WatchDog Timer, EEPROM, and Power LED Signals
PWRGD from Module
Watchdog Timer
Active Low (Power good from System Power supplies) If this LED is off, there is no power to the system (probably) * Check 3V3_UTIL * Check 5V to system * Check Hot plug detect switch is On or off, * Check cable is plugged in
Active Low (Power Good for PS side), if this LED is off, the PS Side power supplies aren't working, check VCCOEN_PS_M2C
Power Status LEDs
Active Low (Power Good for PL side), if this LED is off, the PL Side power supplies aren't working, check VCCOEN_PL_M2C Also check any of the Power supplies for PL
PS Error Status
